maynej/Smart-Home/Imatges/10.png

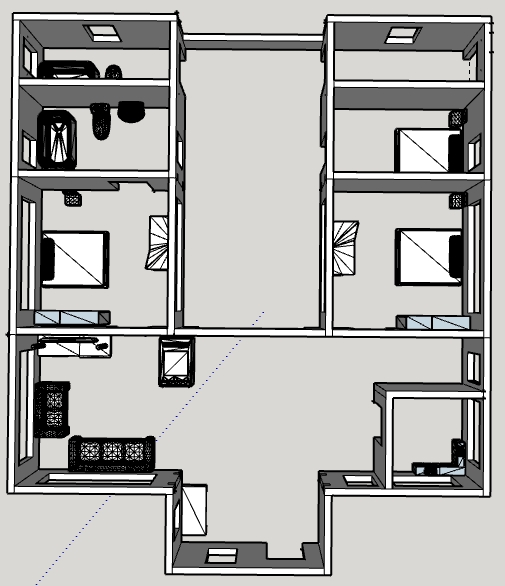
Imatges/10.png
