maynej/Smart-Home/Imatges/14.jpg

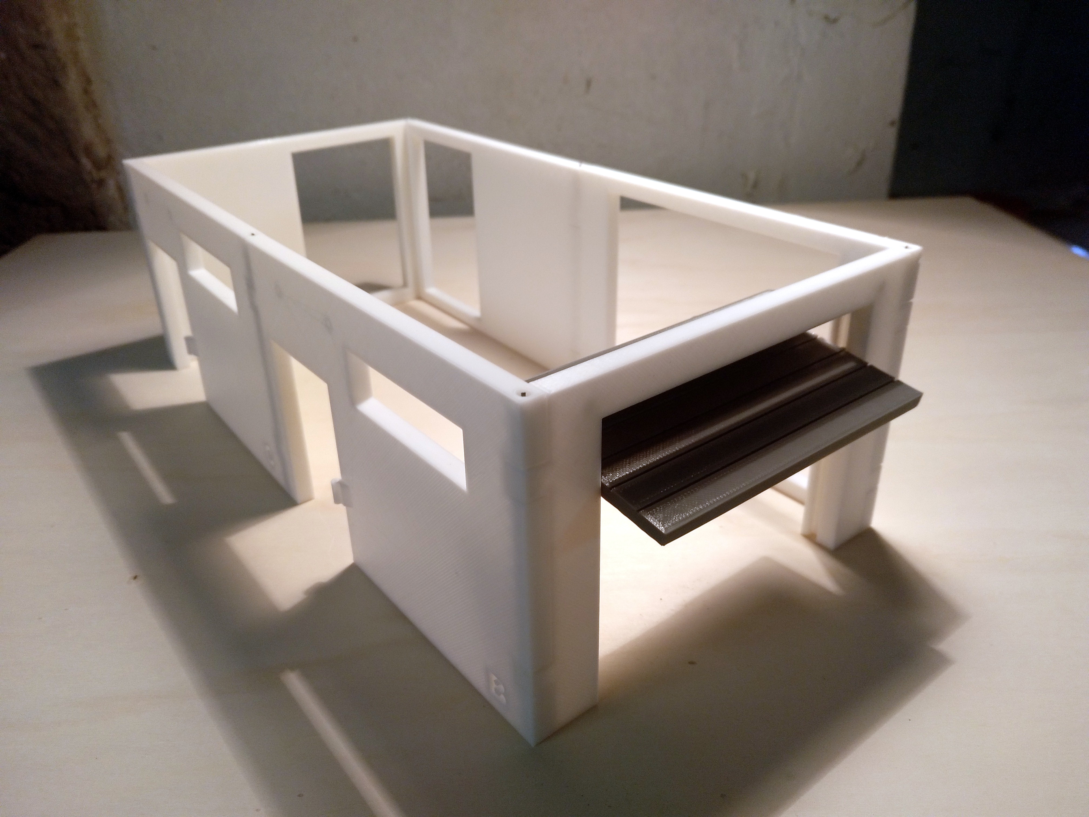
Imatges/14.jpg
