maynej/Smart-Home/Imatges/26.jpg

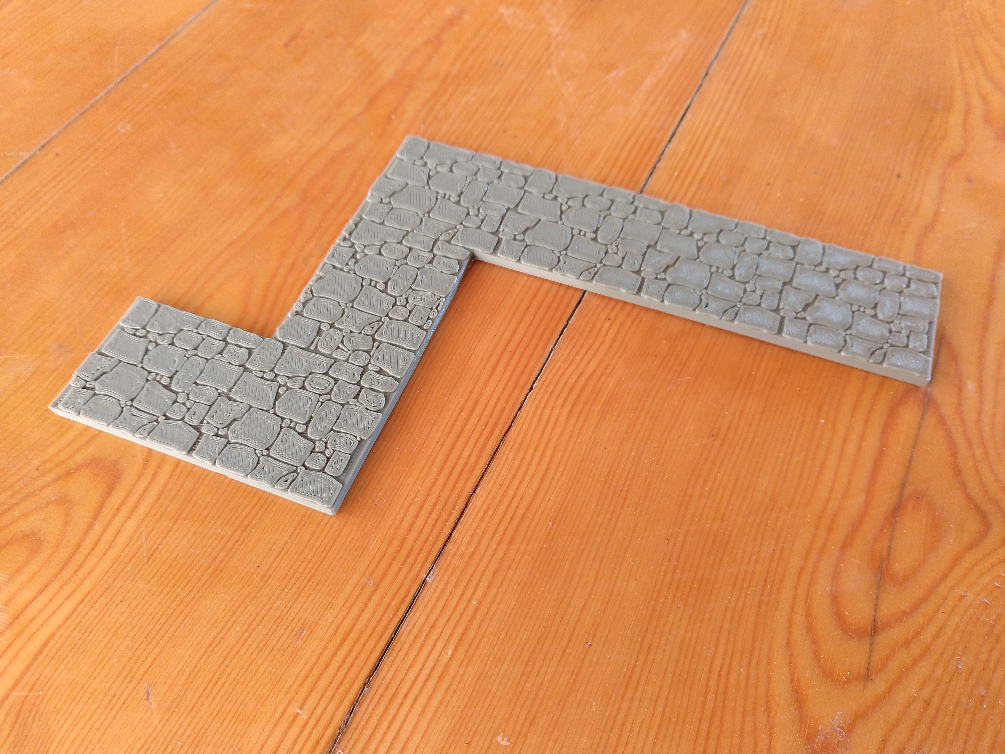
Imatges/26.jpg
