maynej/Smart-Home/Imatges/2020-08-14 22_23_18-Window.png

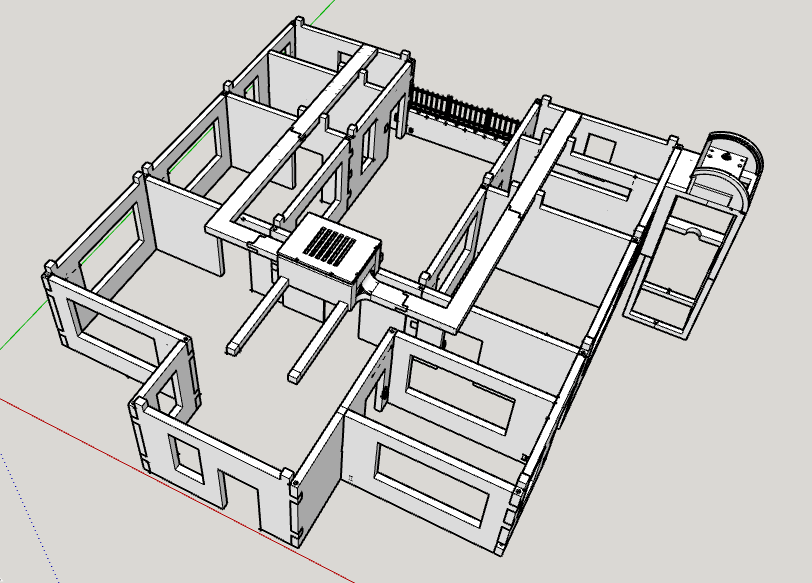
Imatges/2020-08-14 22_23_18-Window.png
