maynej/Smart-Home/Imatges/2020-08-14 22_24_21-Window.png

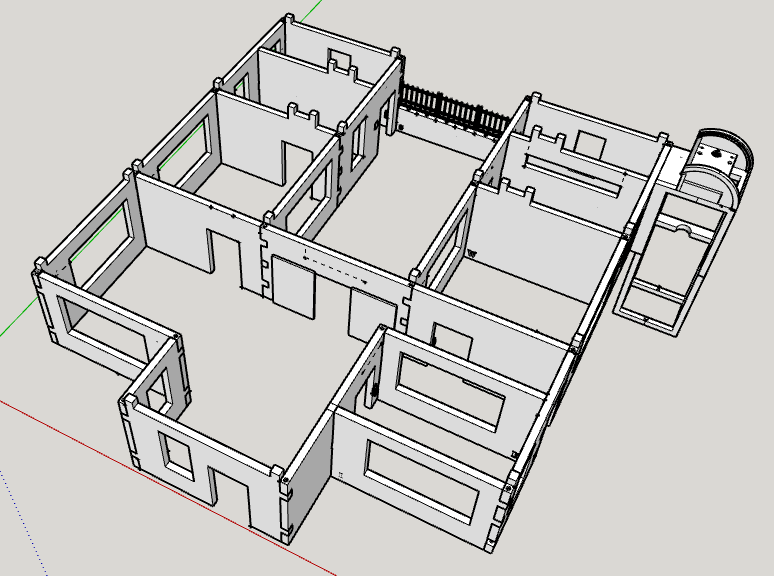
Imatges/2020-08-14 22_24_21-Window.png
