maynej/Smart-Home/Imatges/Casa1.png

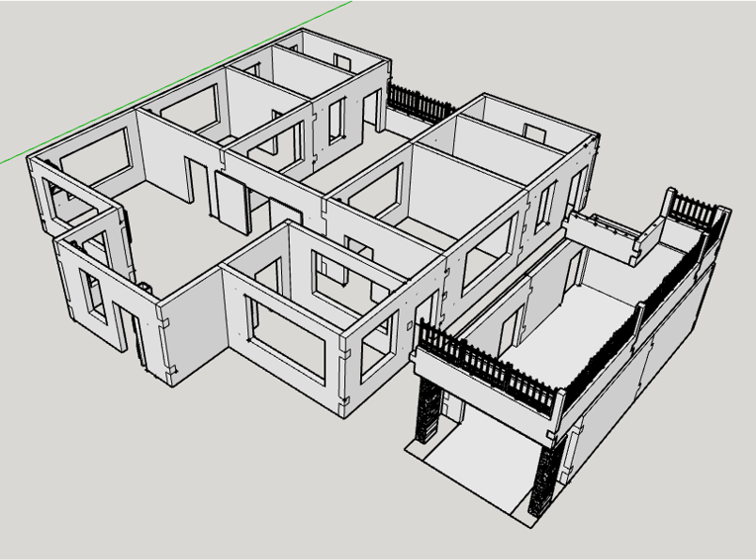
Imatges/Casa1.png
