maynej/Smart-Home/Imatges/IMG_20210501_202601_113.jpg

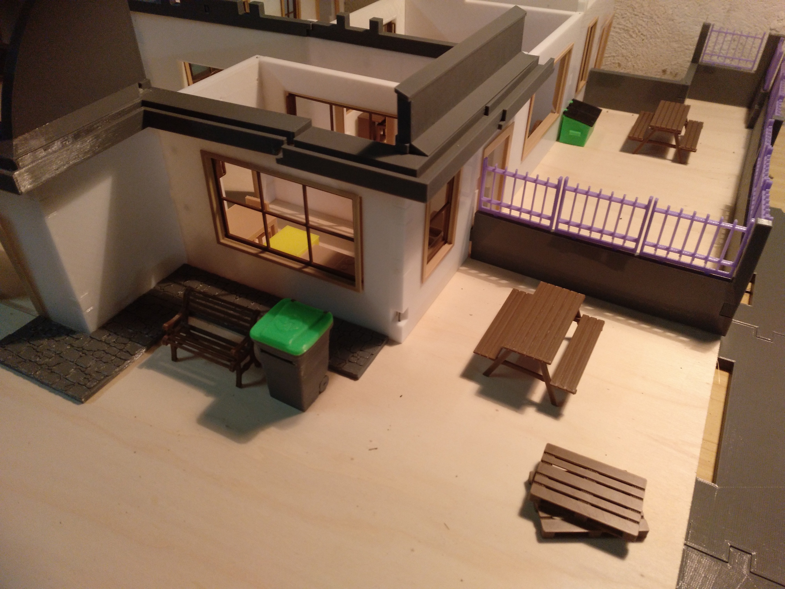
Imatges/IMG_20210501_202601_113.jpg
