maynej/Smart-Home/Imatges/IMG_20210501_202634_148~3.jpg

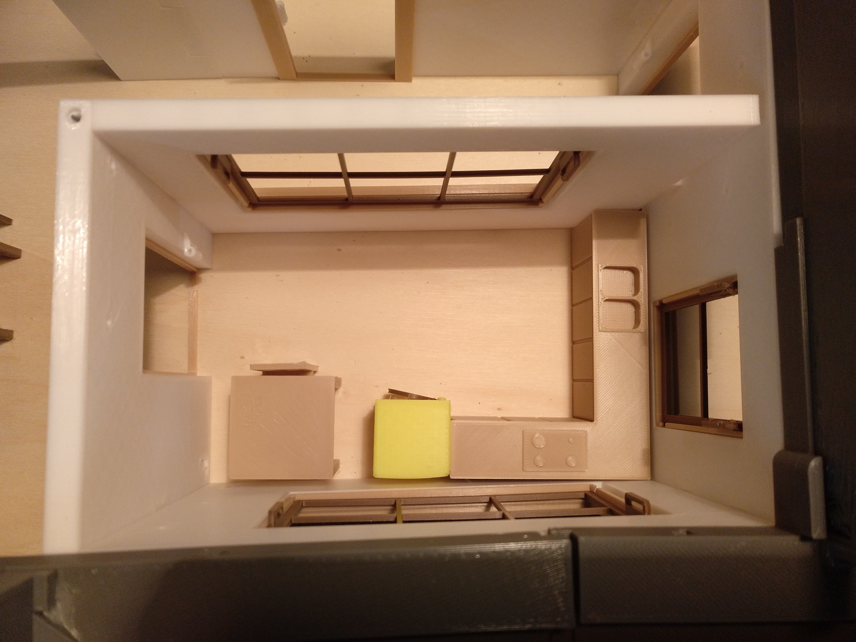
Imatges/IMG_20210501_202634_148~3.jpg
