maynej/Smart-Home/Imatges/IMG_20210501_202759_694~2.jpg

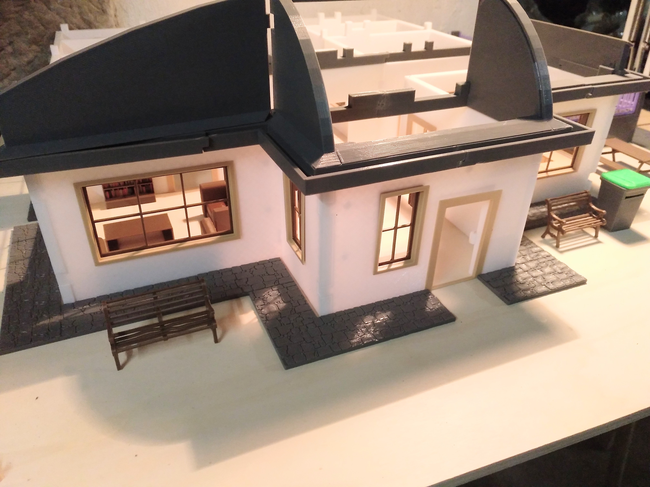
Imatges/IMG_20210501_202759_694~2.jpg
