maynej/Smart-Home/Imatges/IMG_20210501_202805_900~2.jpg

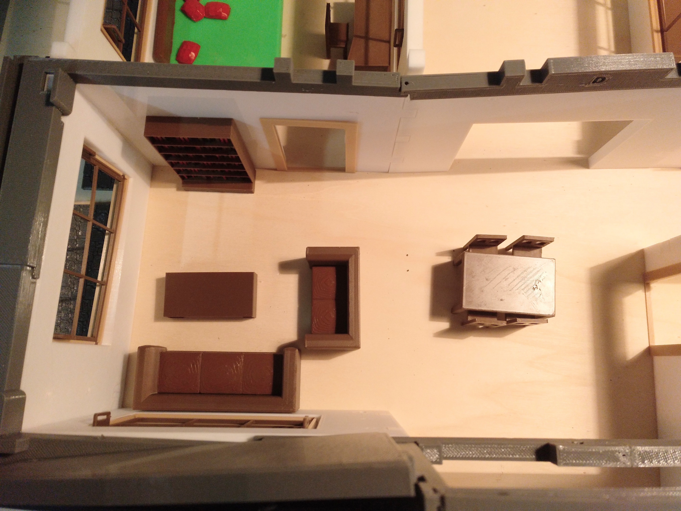
Imatges/IMG_20210501_202805_900~2.jpg
