maynej/Smart-Home/Imatges/IMG_20210501_202834_873.jpg

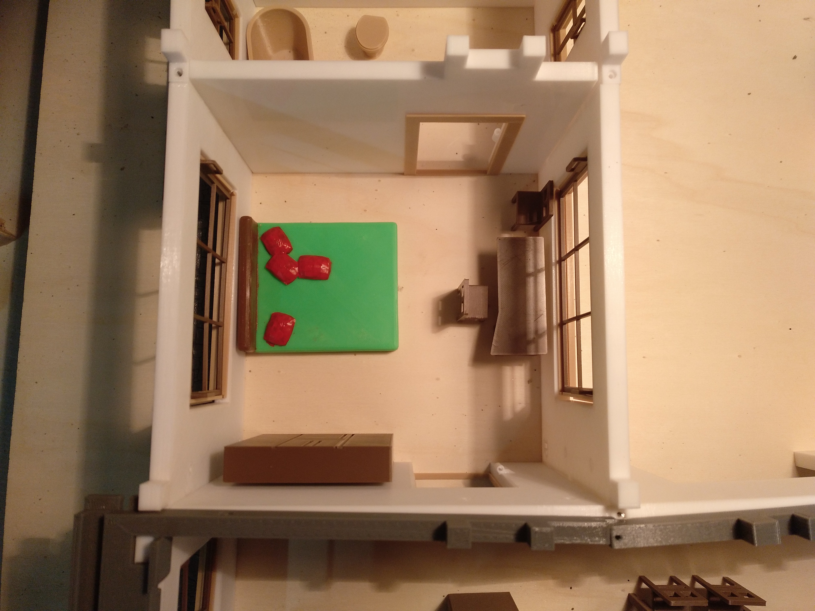
Imatges/IMG_20210501_202834_873.jpg
