maynej/Smart-Home/Imatges/IMG_20210501_202842_626.jpg

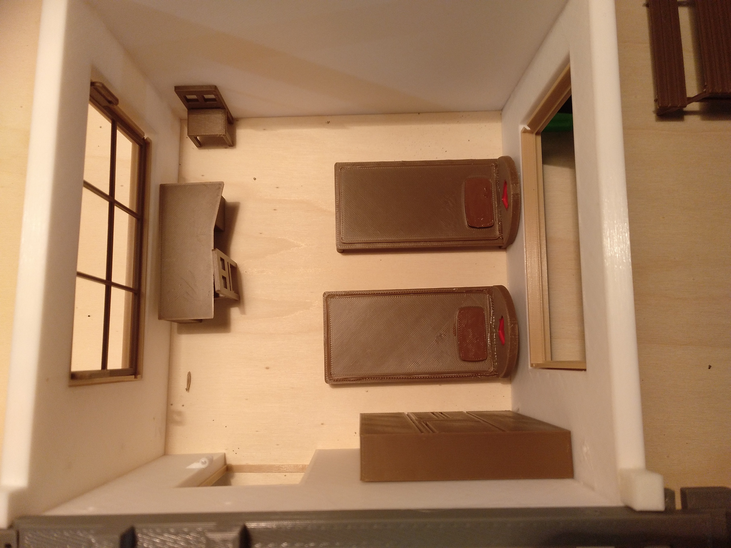
Imatges/IMG_20210501_202842_626.jpg
