maynej/Smart-Home/Imatges/IMG_20210501_202906_033.jpg

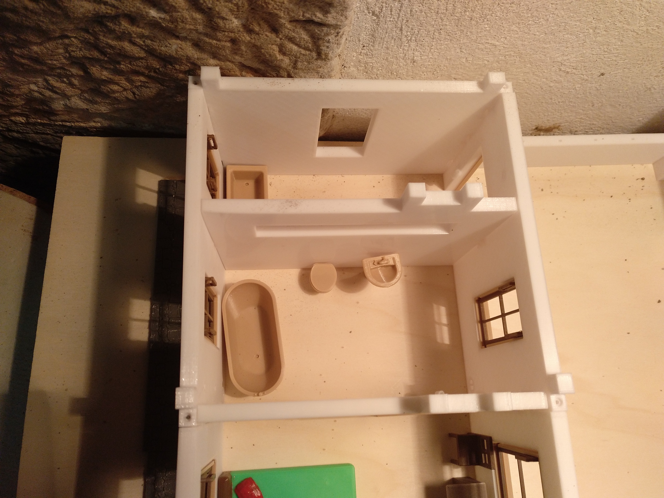
Imatges/IMG_20210501_202906_033.jpg
