maynej/Smart-Home/Imatges/IMG_20210501_202918_298~2.jpg

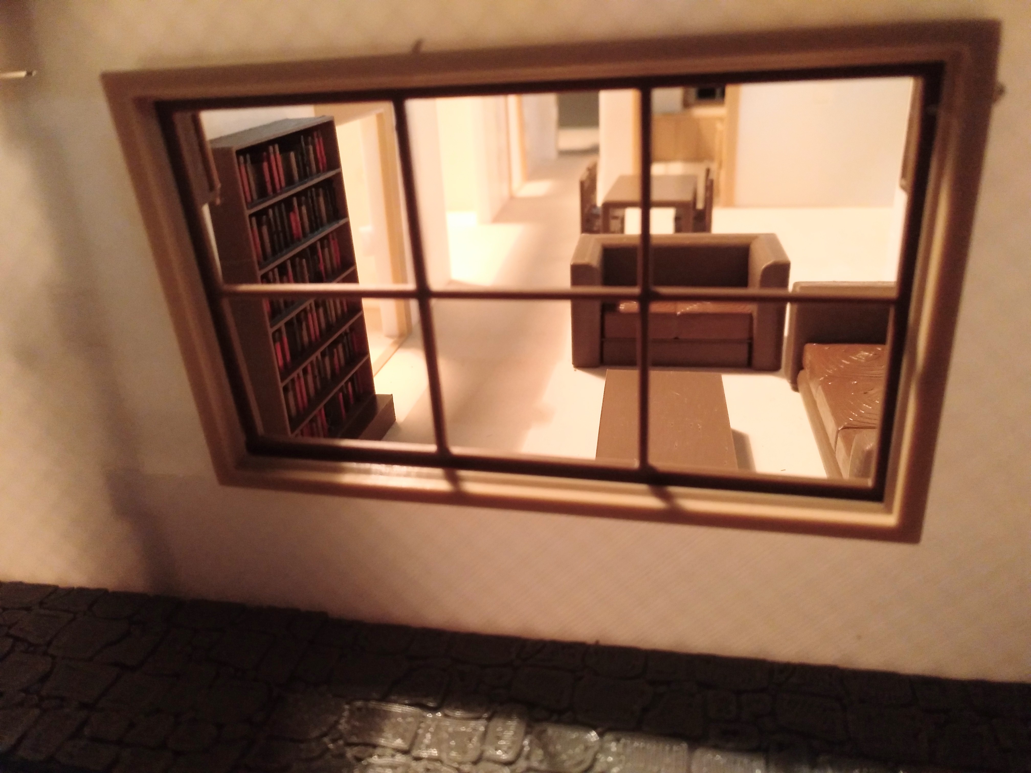
Imatges/IMG_20210501_202918_298~2.jpg
