maynej/Smart-Home/Imatges/IMG_20210501_202927_855.jpg

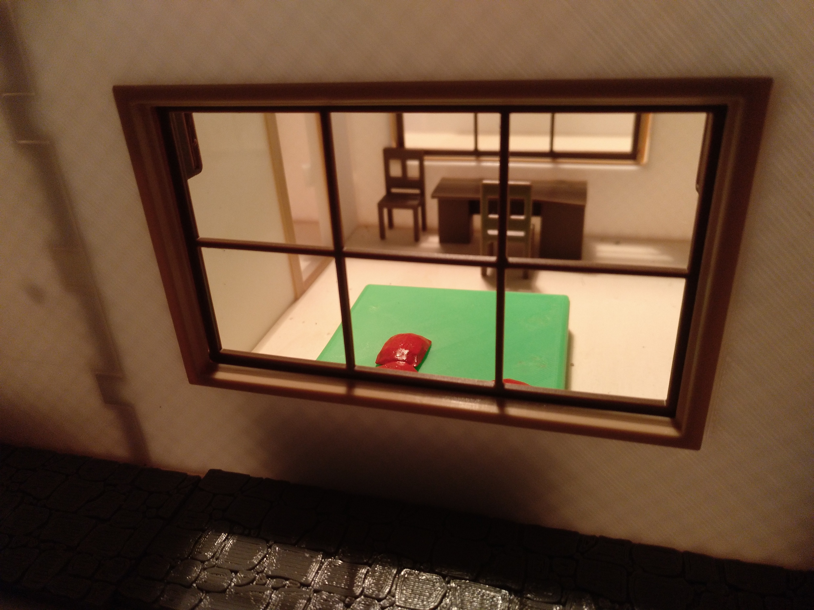
Imatges/IMG_20210501_202927_855.jpg
