maynej/Smart-Home/Imatges/IMG_20210501_202935_807.jpg

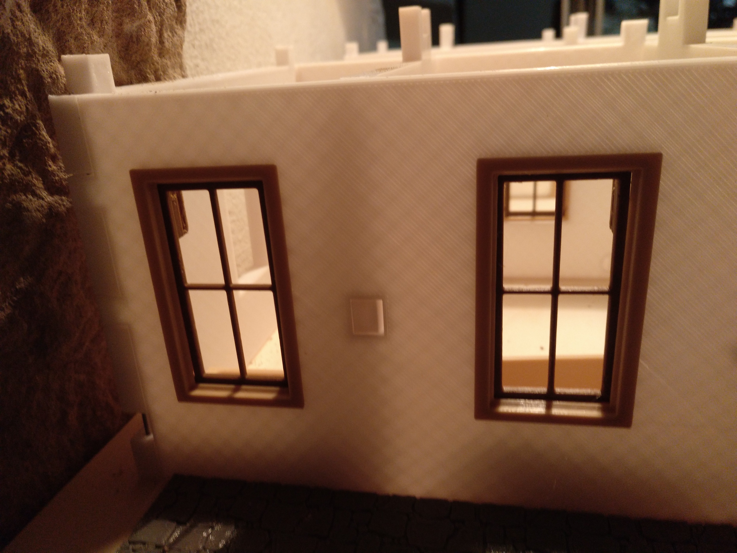
Imatges/IMG_20210501_202935_807.jpg
