maynej/Smart-Home/Imatges/IMG_20210501_202944_740.jpg

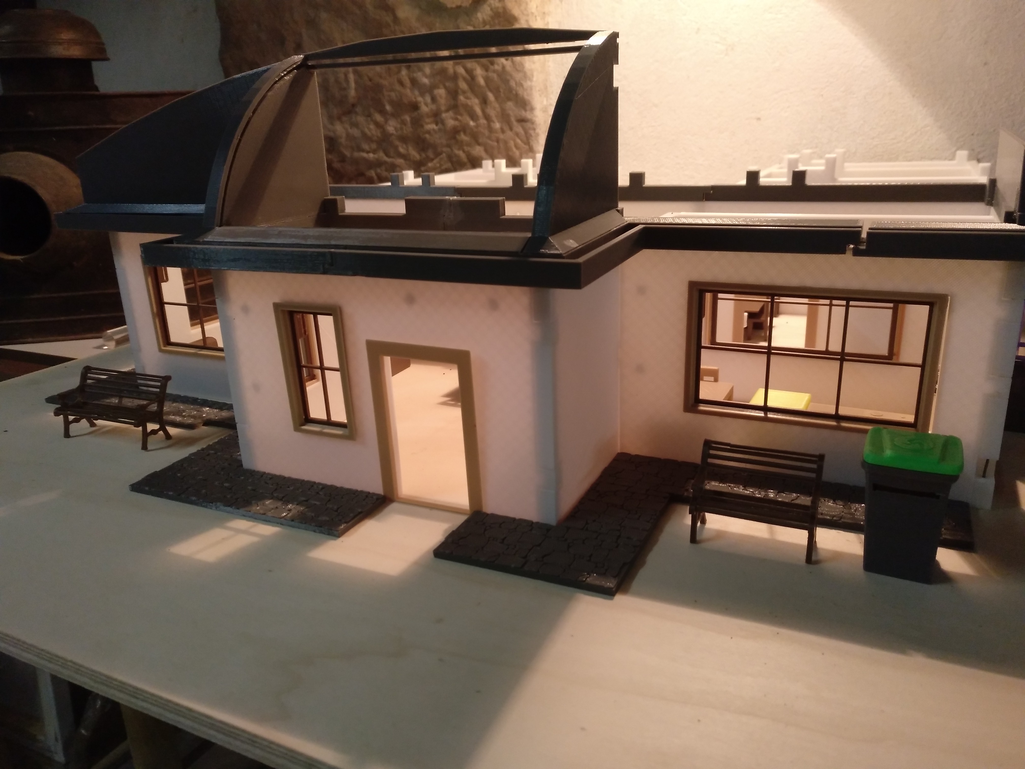
Imatges/IMG_20210501_202944_740.jpg
