maynej/Smart-Home/Imatges/IMG_20210501_202952_292.jpg

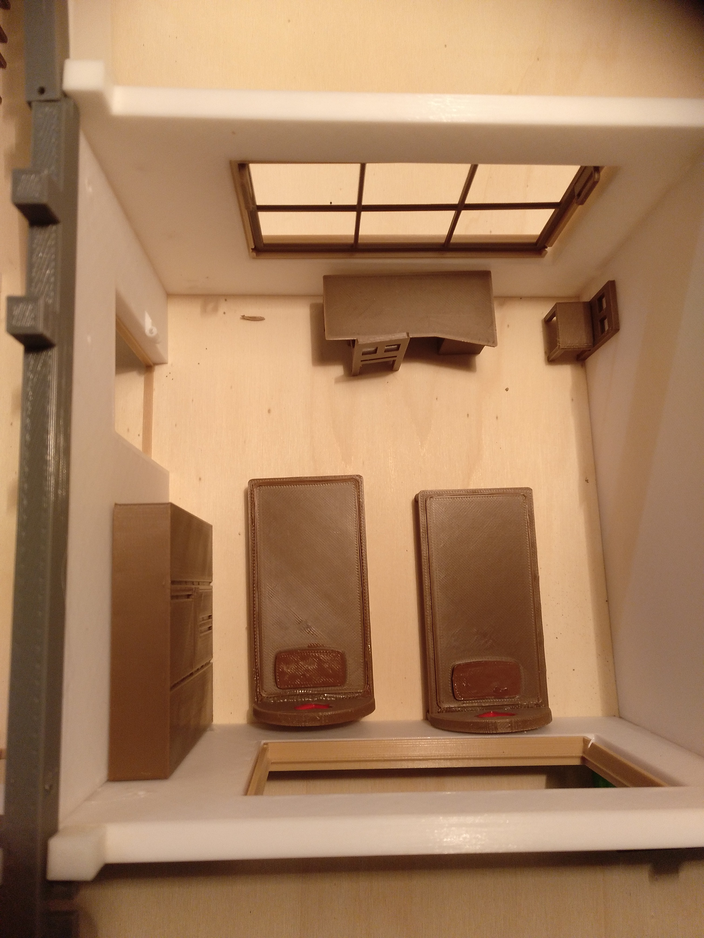
Imatges/IMG_20210501_202952_292.jpg
