maynej/Smart-Home/Imatges/IMG_20210501_203002_859.jpg

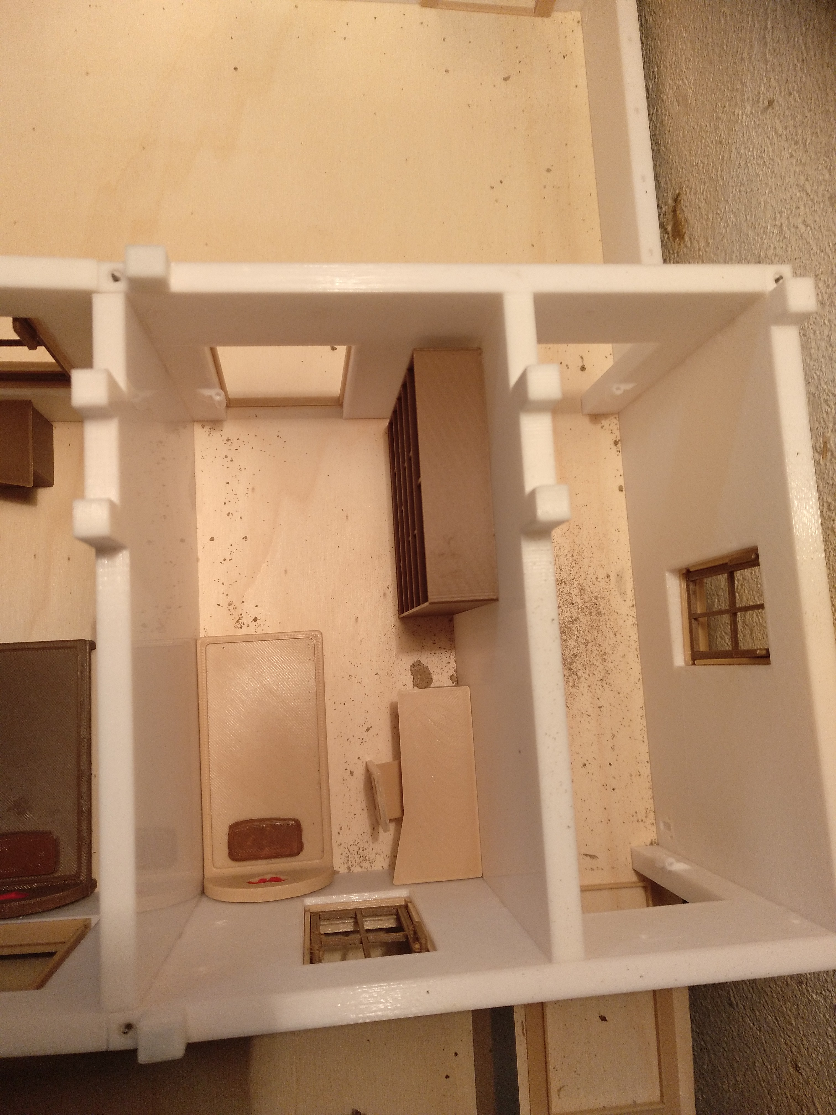
Imatges/IMG_20210501_203002_859.jpg
