maynej/Smart-Home/Imatges/P9200007.jpg

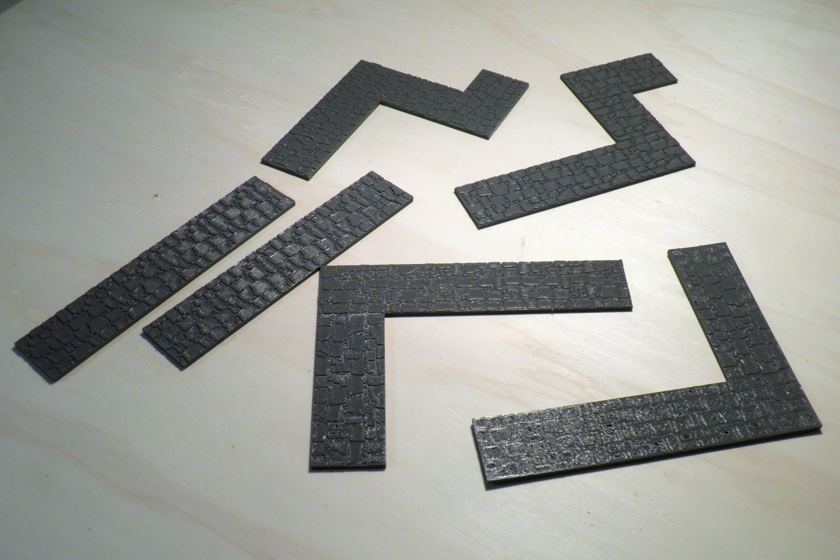
Imatges/P9200007.jpg
