maynej/Smart-Home/Imatges/WhatsApp Image 2020-09-02 at 09.48.22 (1).jpeg

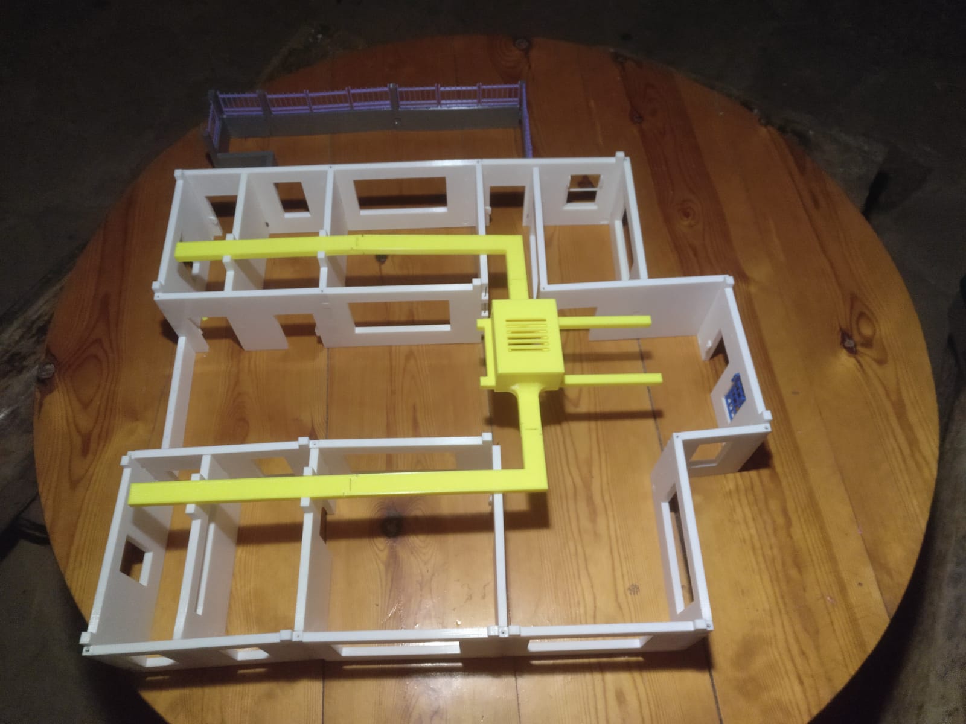
Imatges/WhatsApp Image 2020-09-02 at 09.48.22 (1).jpeg
