maynej/Smart-Home/Imatges/WhatsApp Image 2020-10-18 at 17.20.31.jpeg

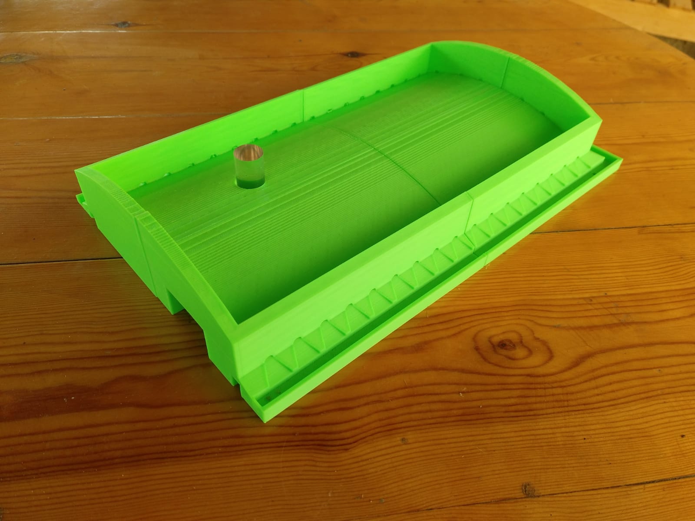
Imatges/WhatsApp Image 2020-10-18 at 17.20.31.jpeg
