maynej/Smart-Home/STL_SMARTHOME/Casa/Teulada/Teulada Frontal/TeuladaFrontal_a_transparent2.stl

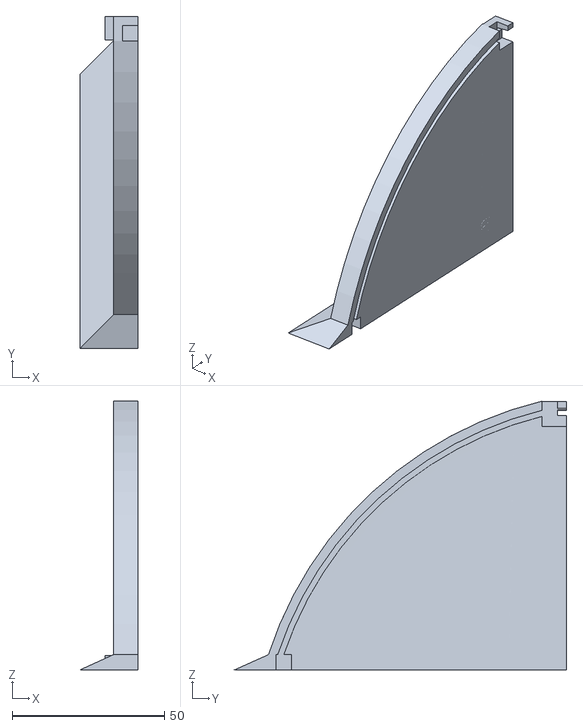
[picture p151: CAD file, 2021-07-27]
STL_SMARTHOME/Casa/Teulada/Teulada Frontal/TeuladaFrontal_a_transparent2.stl
19.0 x 109.0 x 88.2
