maynej/Smart-Home/STL_SMARTHOME/Casa/Teulada/TubDesaiguaCurb.stl

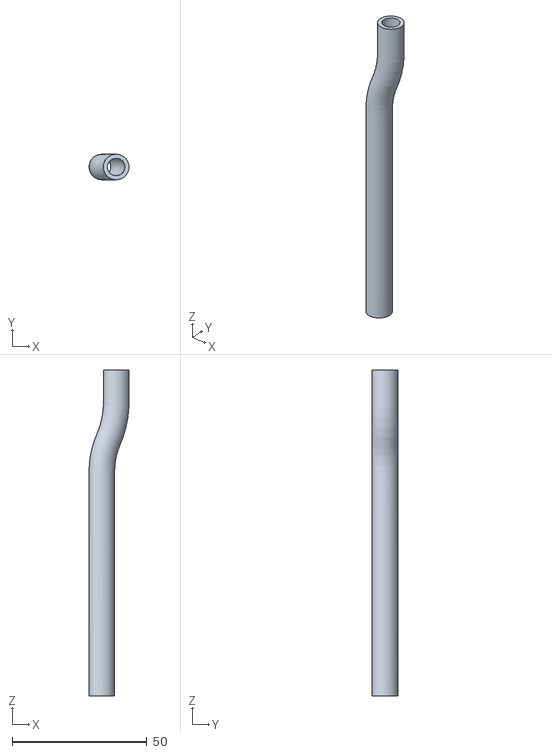
[picture p153: CAD file, 2021-07-27]
STL_SMARTHOME/Casa/Teulada/TubDesaiguaCurb.stl
14.8 x 9.49 x 120.9
