maynej/Smart-Home/STL_SMARTHOME/Casa/Vorera/VoreraEsquerraPedres3.stl

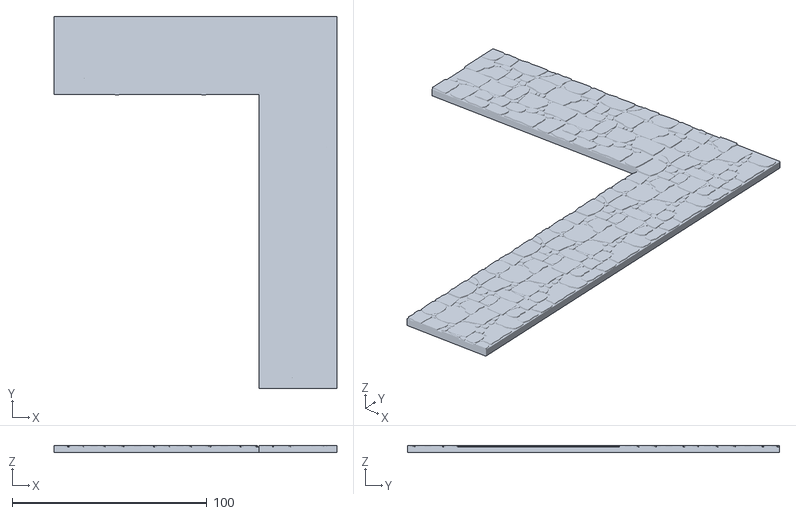
[picture p154: CAD file, 2021-07-27]
STL_SMARTHOME/Casa/Vorera/VoreraEsquerraPedres3.stl
145.3 x 191.0 x 3.71
