maynej/Smart-Home/STL_SMARTHOME/Garatge/PalancaPortaGaratge.stl

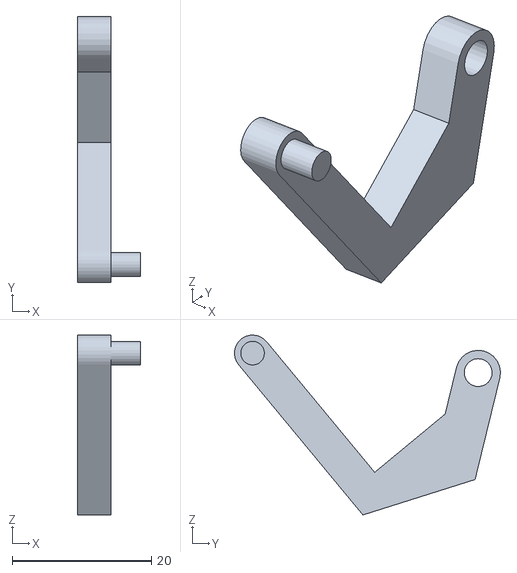
[picture p155: CAD file, 2021-07-27]
STL_SMARTHOME/Garatge/PalancaPortaGaratge.stl
9.00 x 38.1 x 25.8
