maynej/Smart-Home/STL_SMARTHOME/Jardi/GeneradorEolic/Motor.stl

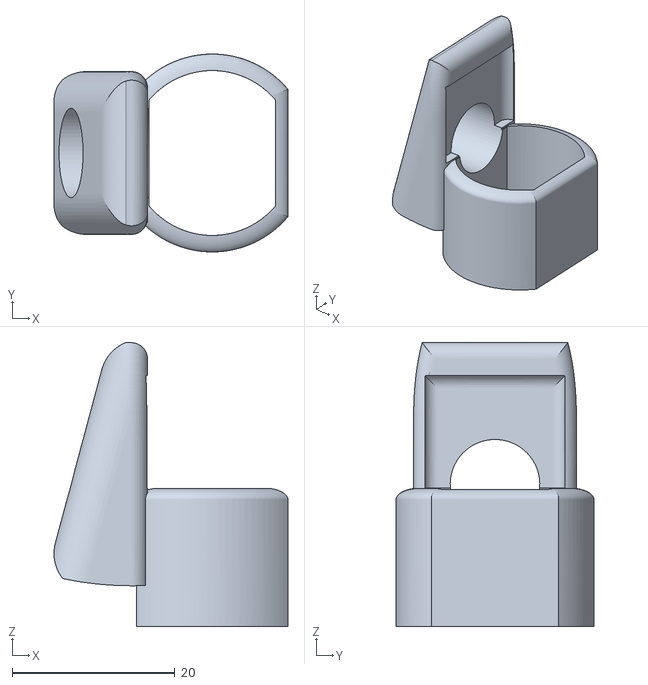
[picture p156: CAD file, 2021-07-27]
STL_SMARTHOME/Jardi/GeneradorEolic/Motor.stl
28.7 x 24.3 x 34.9
