maynej/Smart-Home/STL_SMARTHOME/Jardi/Piscina2.stl

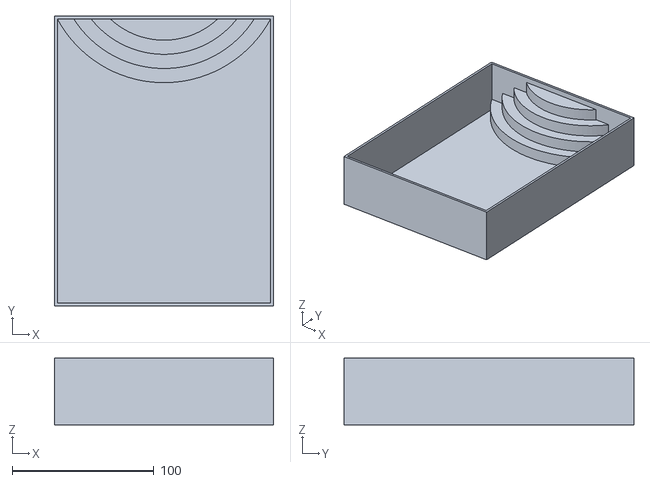
[picture p157: CAD file, 2021-07-27]
STL_SMARTHOME/Jardi/Piscina2.stl
154.5 x 204.5 x 47.0
