maynej/Smart-Home/STL_SMARTHOME/Jardi/SeguidorSolar/SuportCellulaSolar180x80.stl

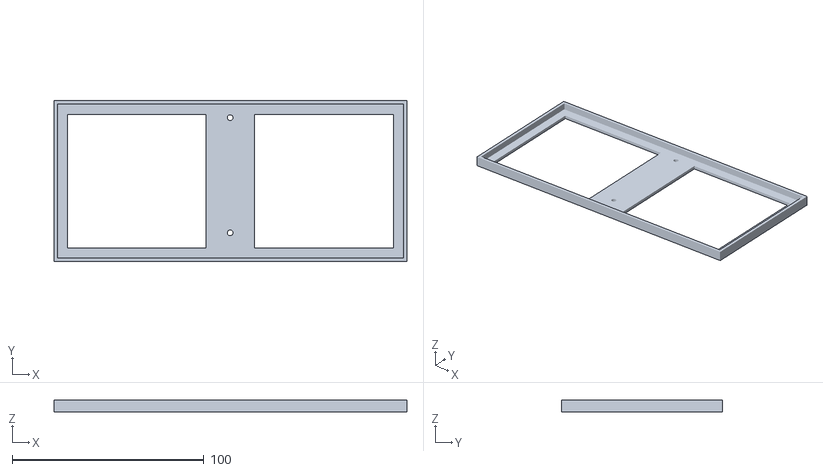
[picture p158: CAD file, 2021-07-27]
STL_SMARTHOME/Jardi/SeguidorSolar/SuportCellulaSolar180x80.stl
184.0 x 84.0 x 6.00
