maynej/Smart-Home/STL_SMARTHOME/Jardi/SolarWeather/front-cover.stl

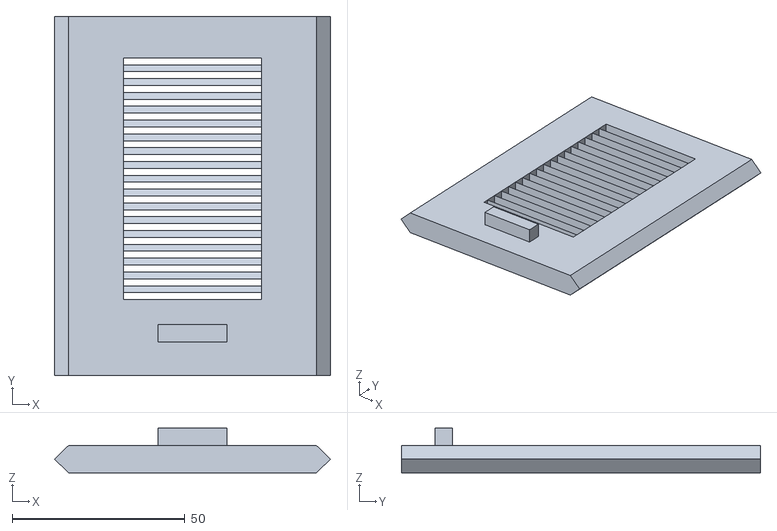
[picture p159: CAD file, 2021-07-27]
STL_SMARTHOME/Jardi/SolarWeather/front-cover.stl
80.0 x 104.0 x 13.0
