maynej/Smart-Home/STL_SMARTHOME/Jardi/TurbinaAigua/Cover.STL

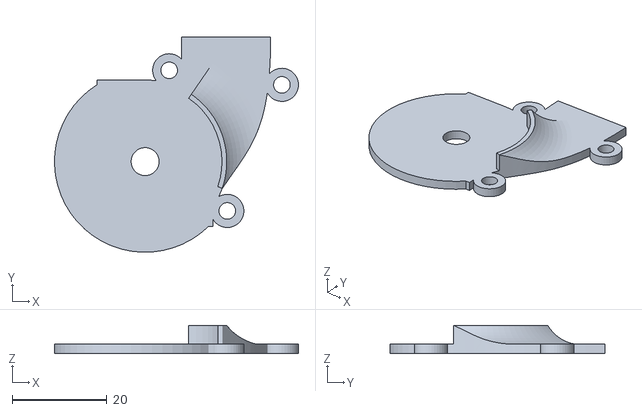
[picture p160: CAD file, 2021-07-27]
STL_SMARTHOME/Jardi/TurbinaAigua/Cover.STL
51.4 x 45.4 x 6.00
