maynej/Smart-Home/STL_SMARTHOME/Casa/AireCondicionat/AireCondicionatC.stl

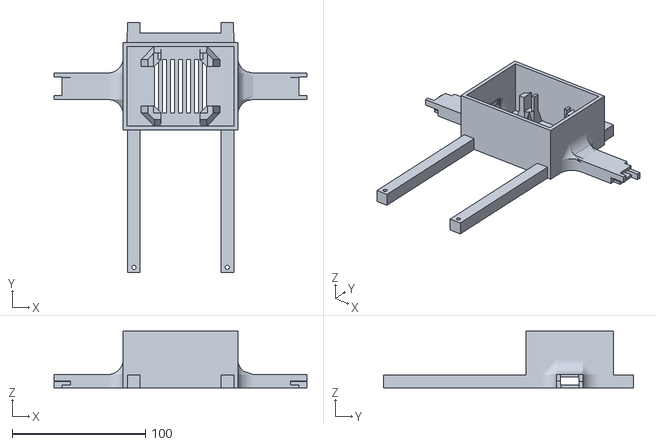
[picture p161: CAD file, 2021-07-27]
STL_SMARTHOME/Casa/AireCondicionat/AireCondicionatC.stl
190.0 x 188.0 x 42.5
