maynej/Smart-Home/STL_SMARTHOME/Casa/Ascensor/CabinaAscensorTapa.stl

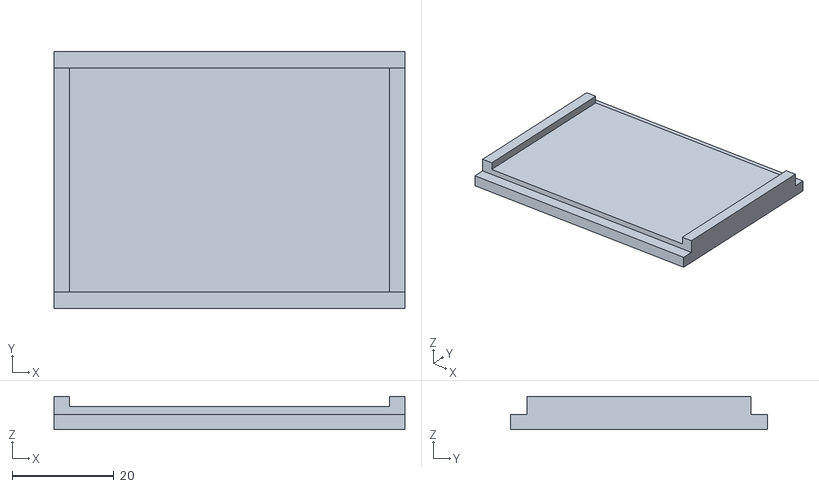
[picture p162: CAD file, 2021-07-27]
STL_SMARTHOME/Casa/Ascensor/CabinaAscensorTapa.stl
69.0 x 50.5 x 6.50
