maynej/Smart-Home/STL_SMARTHOME/Casa/Finestres/VidrieraGran.stl

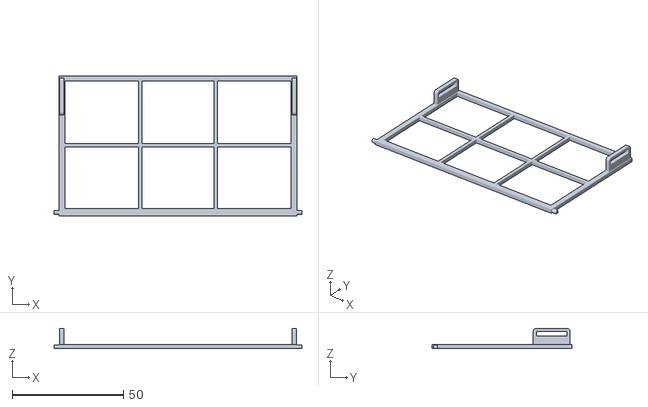
[picture p163: CAD file, 2021-07-27]
STL_SMARTHOME/Casa/Finestres/VidrieraGran.stl
111.4 x 62.8 x 9.18
