maynej/Smart-Home/STL_SMARTHOME/Casa/Mobiliari/Bany/WC.stl

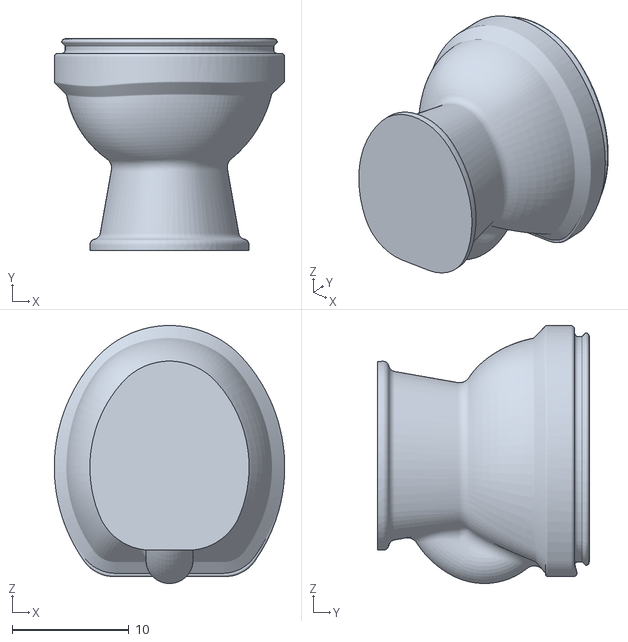
[picture p164: CAD file, 2021-07-27]
STL_SMARTHOME/Casa/Mobiliari/Bany/WC.stl
19.7 x 18.1 x 22.1
