maynej/Smart-Home/STL_SMARTHOME/Casa/Mobiliari/Cuina/TaulaCuina.stl

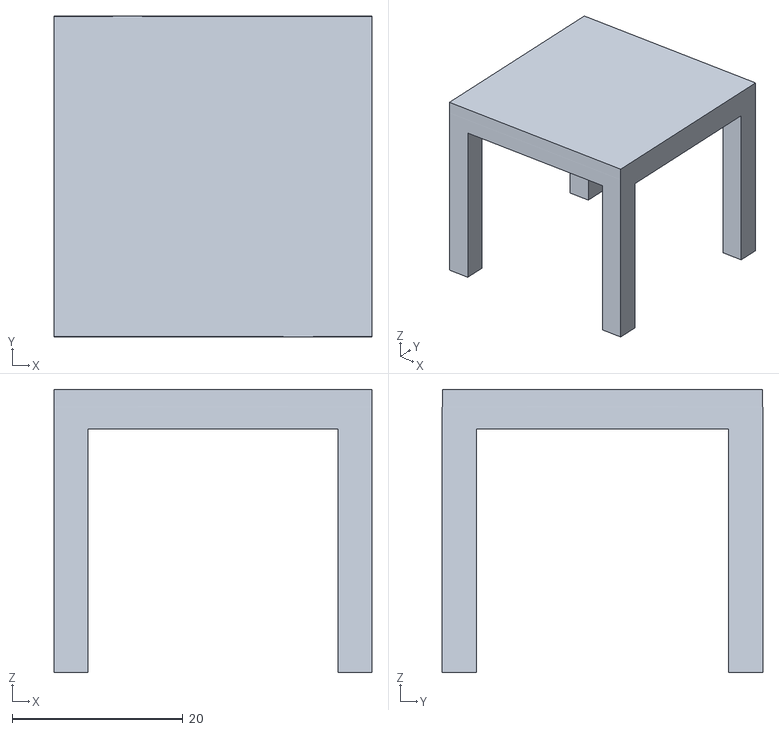
[picture p165: CAD file, 2021-07-27]
STL_SMARTHOME/Casa/Mobiliari/Cuina/TaulaCuina.stl
37.2 x 37.5 x 33.1
