maynej/Smart-Home/STL_SMARTHOME/Casa/Mobiliari/Dormitoris/Llit180x200.stl

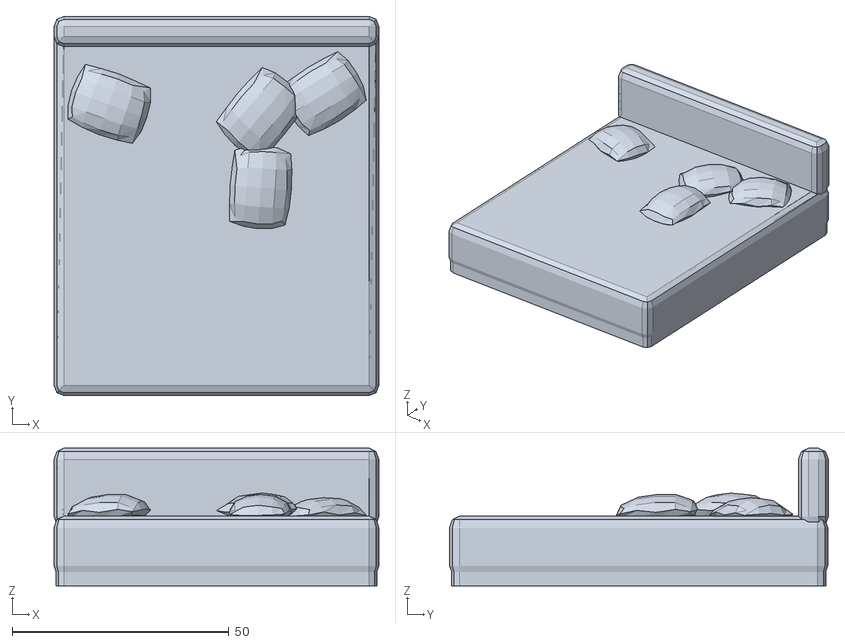
[picture p166: CAD file, 2021-07-27]
STL_SMARTHOME/Casa/Mobiliari/Dormitoris/Llit180x200.stl
75.0 x 87.5 x 31.8
