maynej/Smart-Home/STL_SMARTHOME/Casa/Mobiliari/Exterior/BancJardi.stl

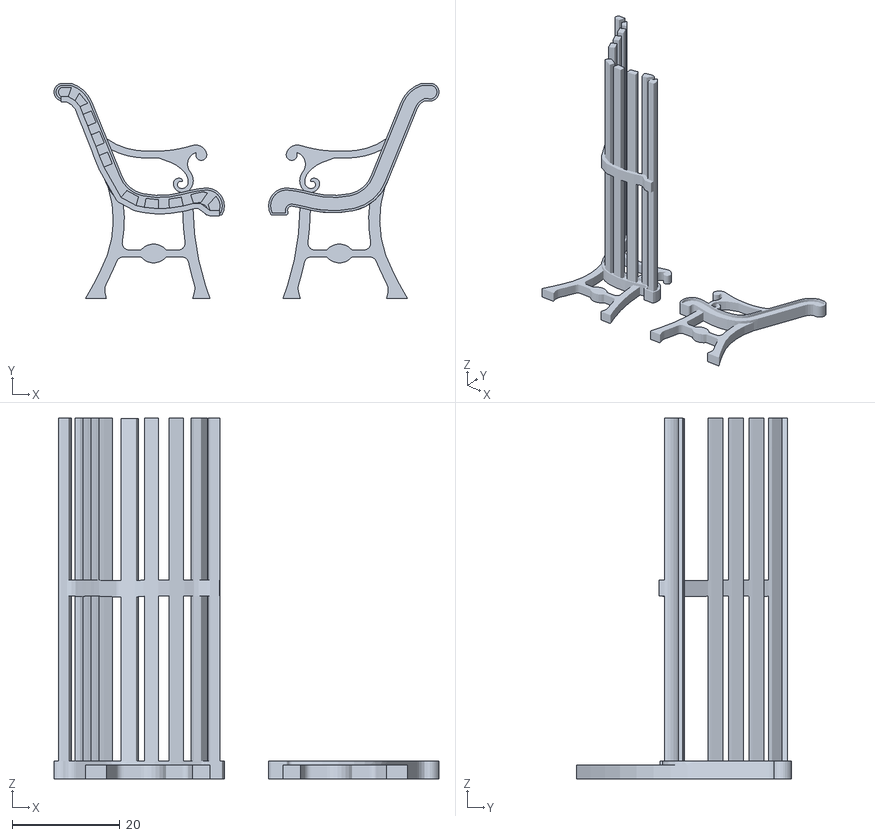
[picture p167: CAD file, 2021-07-27]
STL_SMARTHOME/Casa/Mobiliari/Exterior/BancJardi.stl
71.3 x 39.9 x 66.8
