maynej/Smart-Home/STL_SMARTHOME/Casa/Mobiliari/Salo/Taula.stl

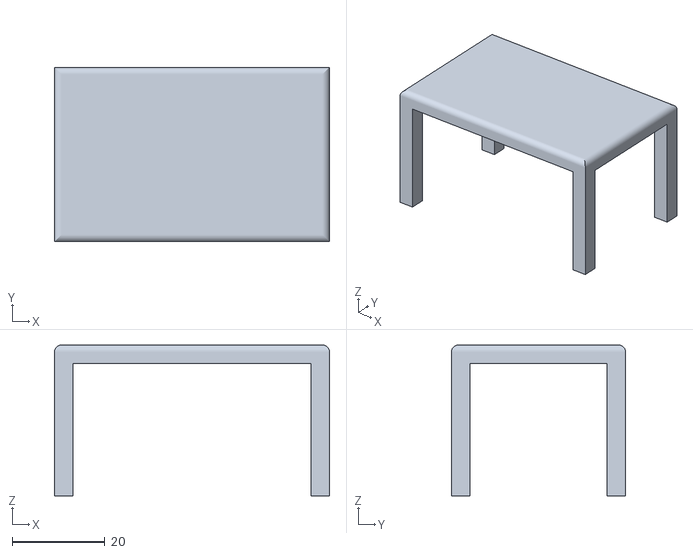
[picture p168: CAD file, 2021-07-27]
STL_SMARTHOME/Casa/Mobiliari/Salo/Taula.stl
59.2 x 37.5 x 32.5
