maynej/Smart-Home/STL_SMARTHOME/Casa/PatiGaratge/MurA.stl

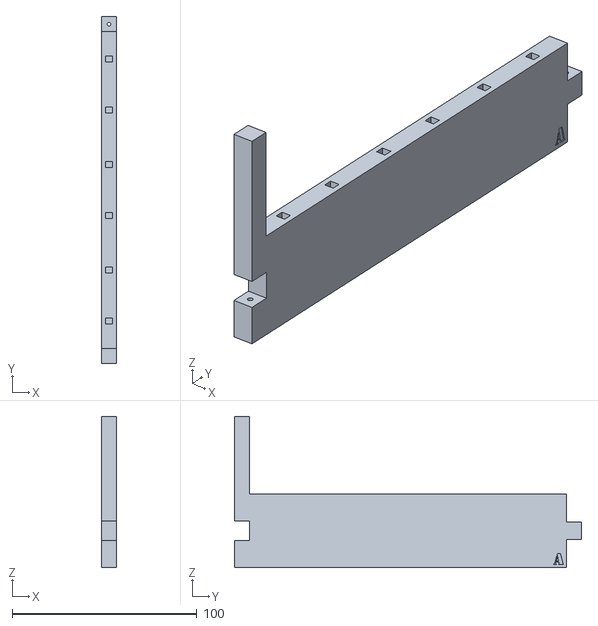
[picture p169: CAD file, 2021-07-27]
STL_SMARTHOME/Casa/PatiGaratge/MurA.stl
8.00 x 188.0 x 82.0
