maynej/Smart-Home/STL_SMARTHOME/Casa/Portes/Porta_Dreta.stl

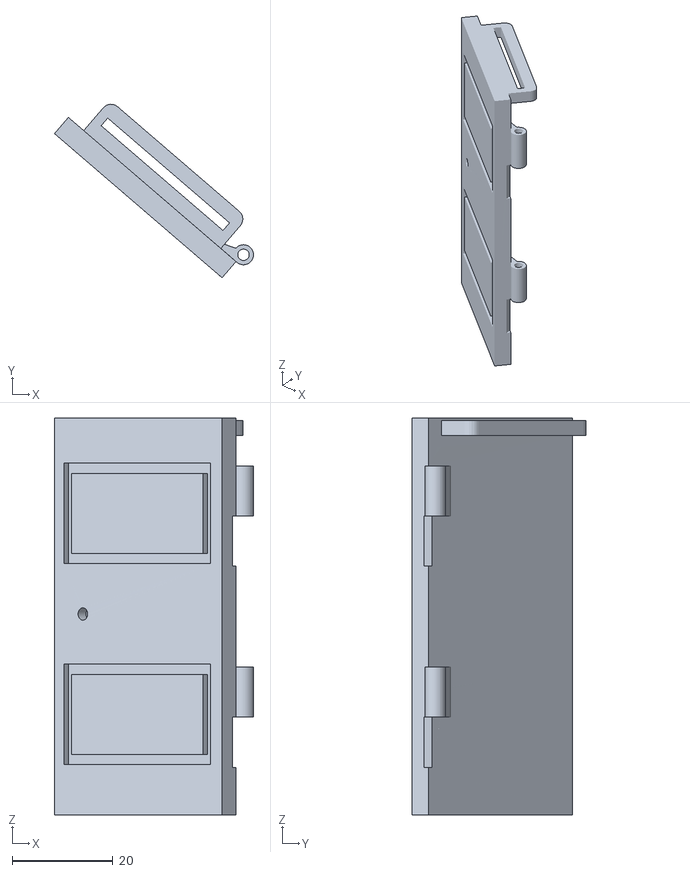
[picture p170: CAD file, 2021-07-27]
STL_SMARTHOME/Casa/Portes/Porta_Dreta.stl
39.6 x 34.5 x 79.0
