maynej/Smart-Home/STL_SMARTHOME/Casa/Teulada/Suport_Teulada Frontal/SuportTeuladaA.stl

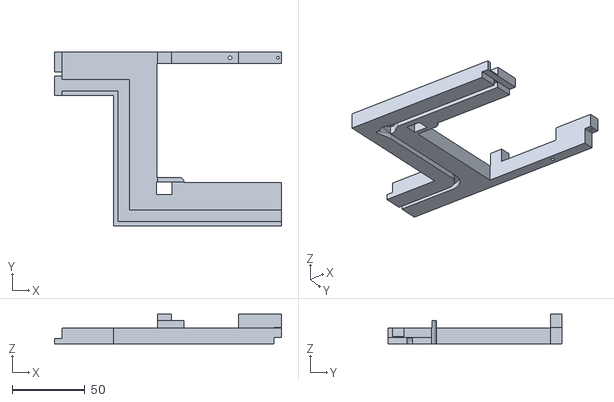
[picture p171: CAD file, 2021-07-27]
STL_SMARTHOME/Casa/Teulada/Suport_Teulada Frontal/SuportTeuladaA.stl
156.4 x 120.0 x 20.5
