maynej/Smart-Home/STL_SMARTHOME/Casa/Teulada/Teulada Frontal/TeuladaFrontal_a_transparent3.stl

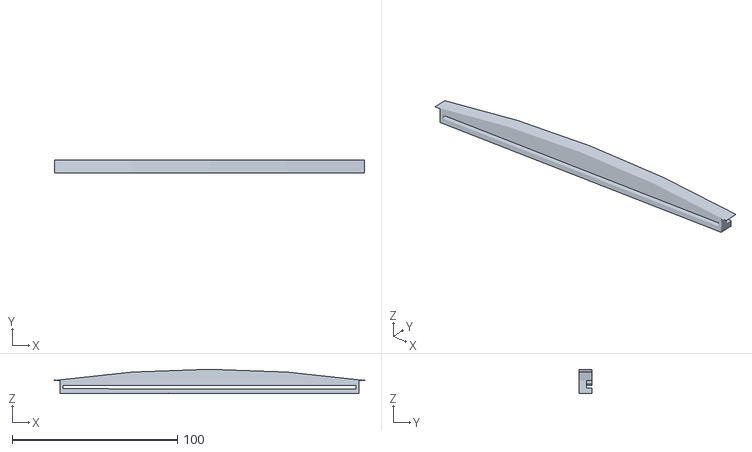
[picture p172: CAD file, 2021-07-27]
STL_SMARTHOME/Casa/Teulada/Teulada Frontal/TeuladaFrontal_a_transparent3.stl
187.5 x 8.02 x 14.8
