maynej/Smart-Home/STL_SMARTHOME/Casa/Vorera/VoreraDretaPedres1.stl

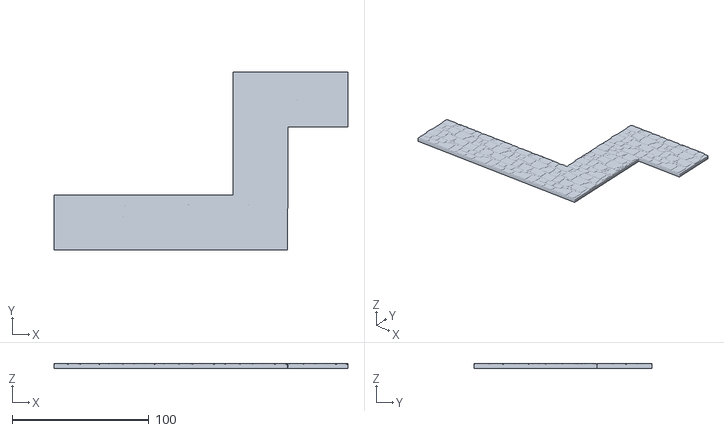
[picture p173: CAD file, 2021-07-27]
STL_SMARTHOME/Casa/Vorera/VoreraDretaPedres1.stl
214.8 x 129.7 x 3.81
