maynej/Smart-Home/STL_SMARTHOME/Garatge/GaratgeA.stl

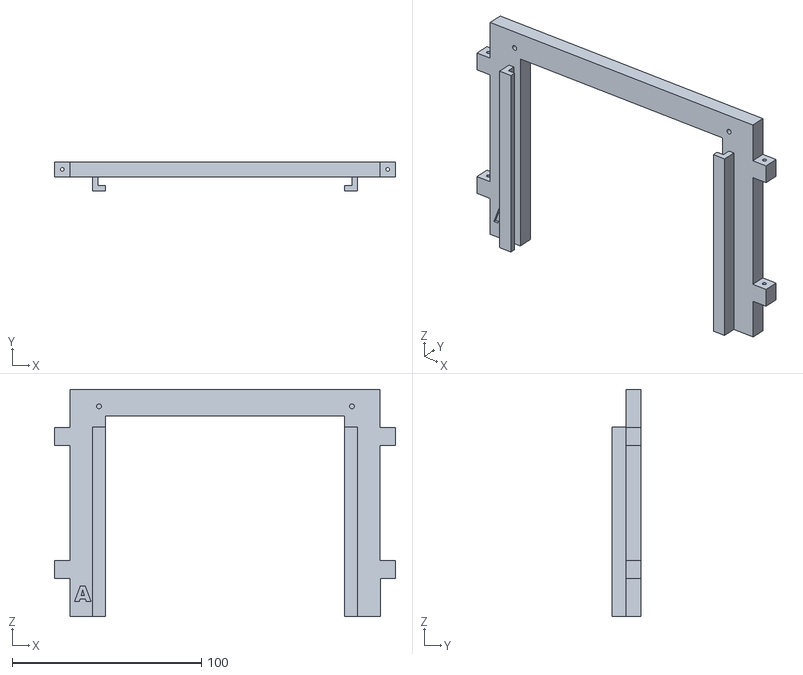
[picture p174: CAD file, 2021-07-27]
STL_SMARTHOME/Garatge/GaratgeA.stl
180.0 x 15.5 x 120.0
