maynej/Smart-Home/STL_SMARTHOME/Jardi/GeneradorEolic/PalesTurbina.stl

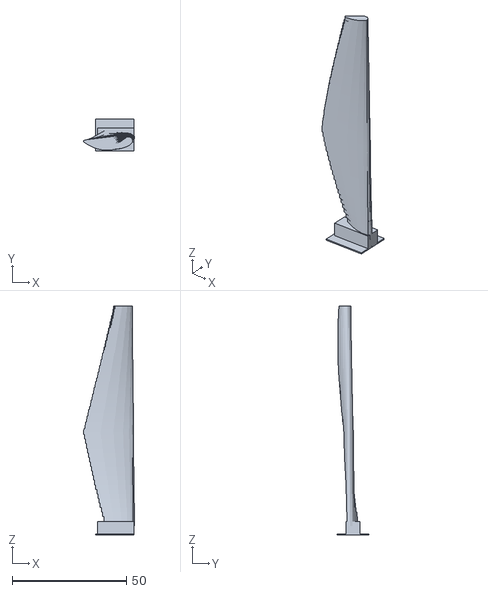
[picture p175: CAD file, 2021-07-27]
STL_SMARTHOME/Jardi/GeneradorEolic/PalesTurbina.stl
22.5 x 14.0 x 100.4
