maynej/Smart-Home/STL_SMARTHOME/Jardi/Hort.stl

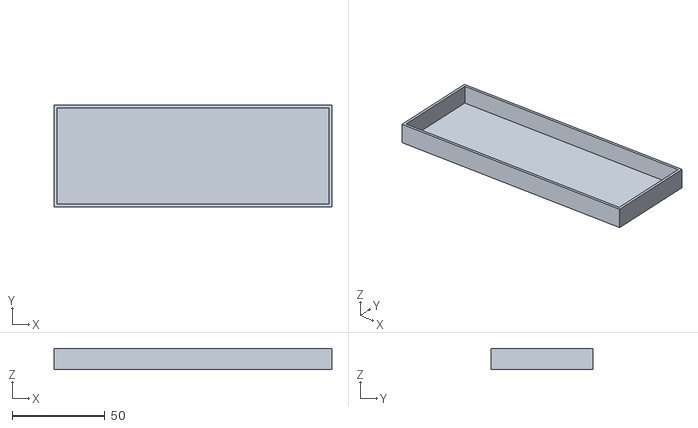
[picture p176: CAD file, 2021-07-27]
STL_SMARTHOME/Jardi/Hort.stl
150.0 x 55.0 x 11.5
