maynej/Smart-Home/STL_SMARTHOME/Jardi/SeguidorSolar/SuportCellulaSolar150x130.stl

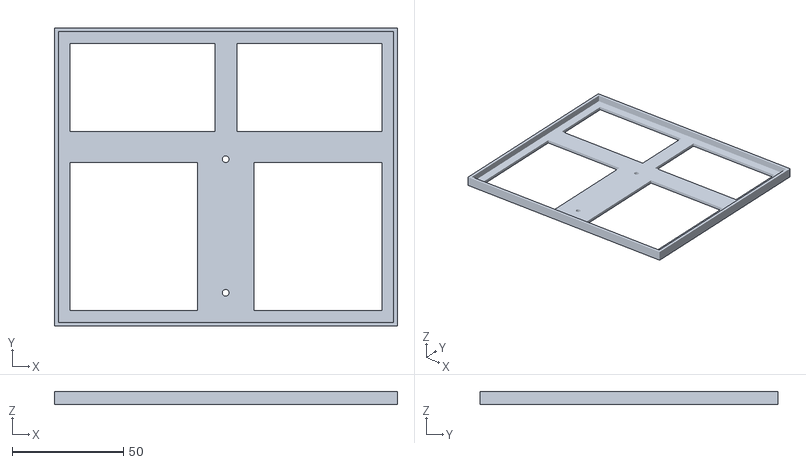
[picture p177: CAD file, 2021-07-27]
STL_SMARTHOME/Jardi/SeguidorSolar/SuportCellulaSolar150x130.stl
154.0 x 134.0 x 6.00
