maynej/Smart-Home/STL_SMARTHOME/Jardi/TurbinaAigua/Housing.STL

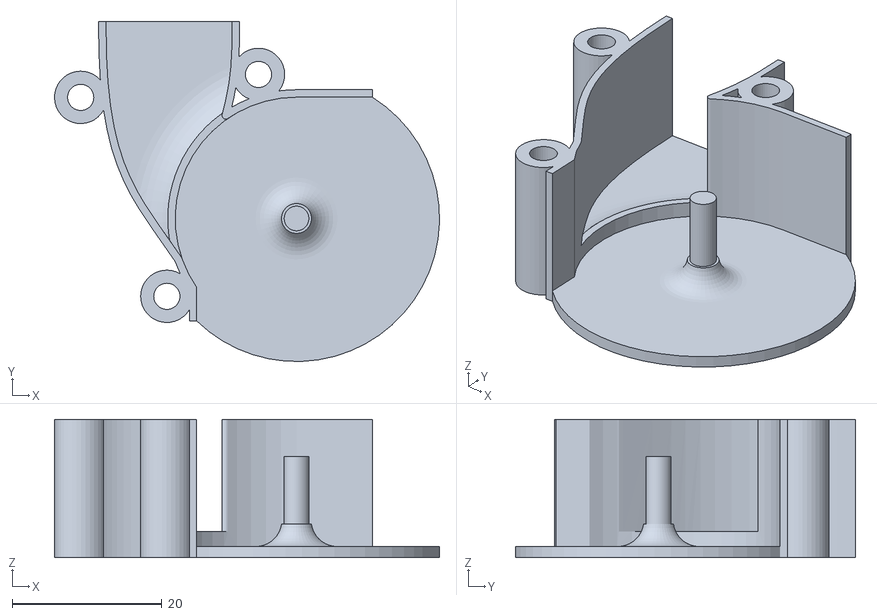
[picture p178: CAD file, 2021-07-27]
STL_SMARTHOME/Jardi/TurbinaAigua/Housing.STL
51.4 x 45.4 x 18.5
