maynej/Smart-Home/STL_SMARTHOME/Casa/AireCondicionat/TubAireE.stl

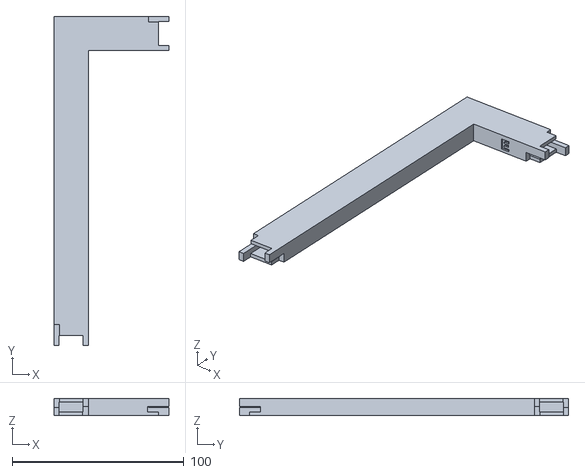
[picture p179: CAD file, 2021-07-27]
STL_SMARTHOME/Casa/AireCondicionat/TubAireE.stl
67.1 x 192.0 x 10.0
