maynej/Smart-Home/STL_SMARTHOME/Casa/Ascensor/Ascensor2.stl

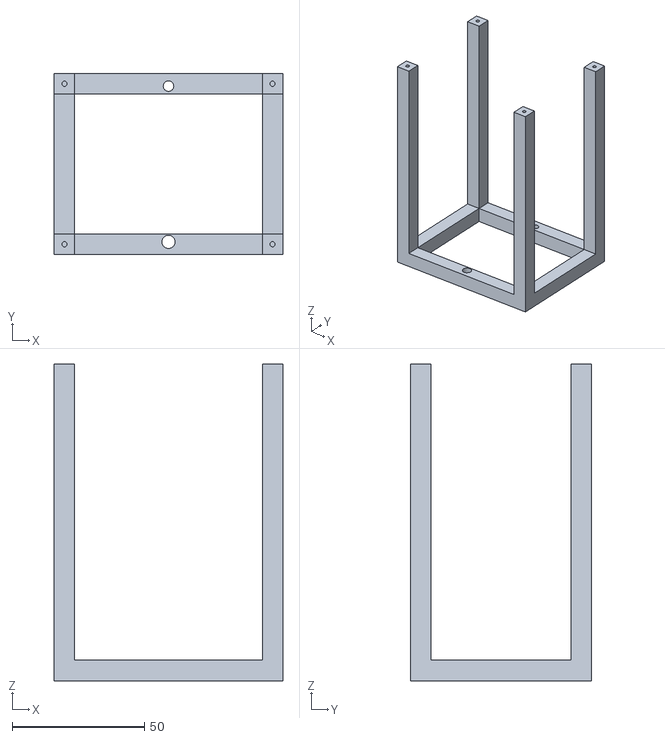
[picture p180: CAD file, 2021-07-27]
STL_SMARTHOME/Casa/Ascensor/Ascensor2.stl
86.5 x 68.5 x 120.0
