maynej/Smart-Home/STL_SMARTHOME/Casa/Finestres/VidrieraPetita.stl

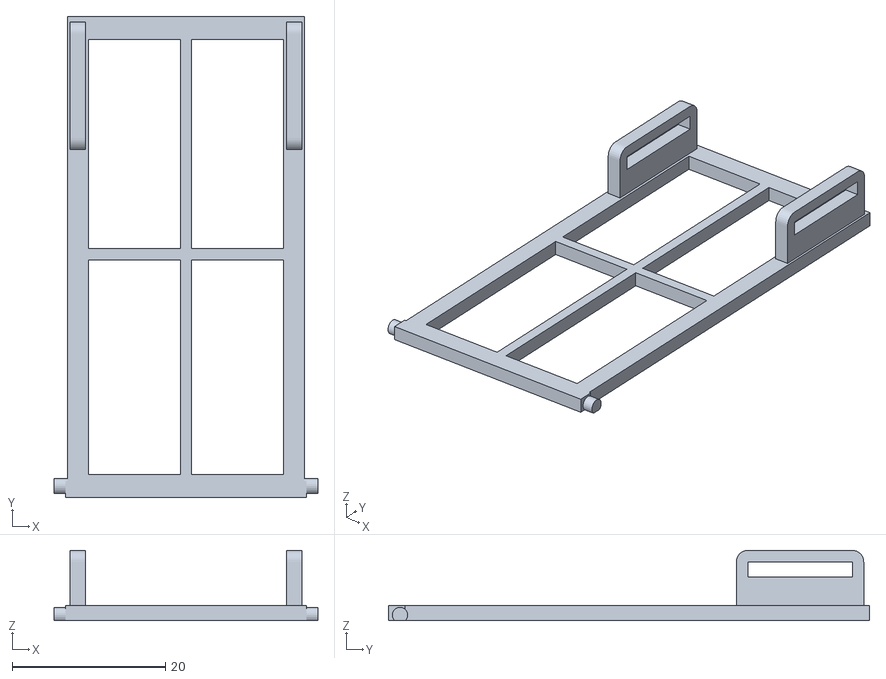
[picture p181: CAD file, 2021-07-27]
STL_SMARTHOME/Casa/Finestres/VidrieraPetita.stl
34.4 x 62.8 x 9.18
