maynej/Smart-Home/STL_SMARTHOME/Casa/Mobiliari/Bany/BanyeraRectangular.stl

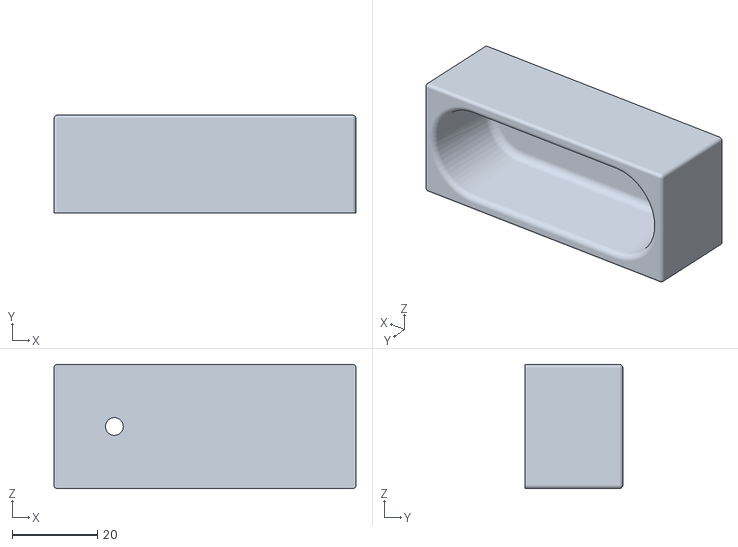
[picture p182: CAD file, 2021-07-27]
STL_SMARTHOME/Casa/Mobiliari/Bany/BanyeraRectangular.stl
70.8 x 22.9 x 29.2
