maynej/Smart-Home/STL_SMARTHOME/Casa/Mobiliari/Cuina/TapaRentadora.stl

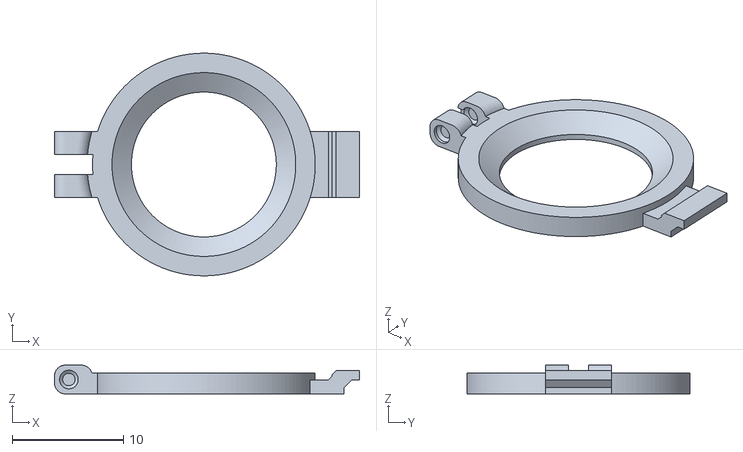
[picture p183: CAD file, 2021-07-27]
STL_SMARTHOME/Casa/Mobiliari/Cuina/TapaRentadora.stl
27.4 x 20.0 x 2.59
