maynej/Smart-Home/STL_SMARTHOME/Casa/Mobiliari/Dormitoris/Cadira.stl

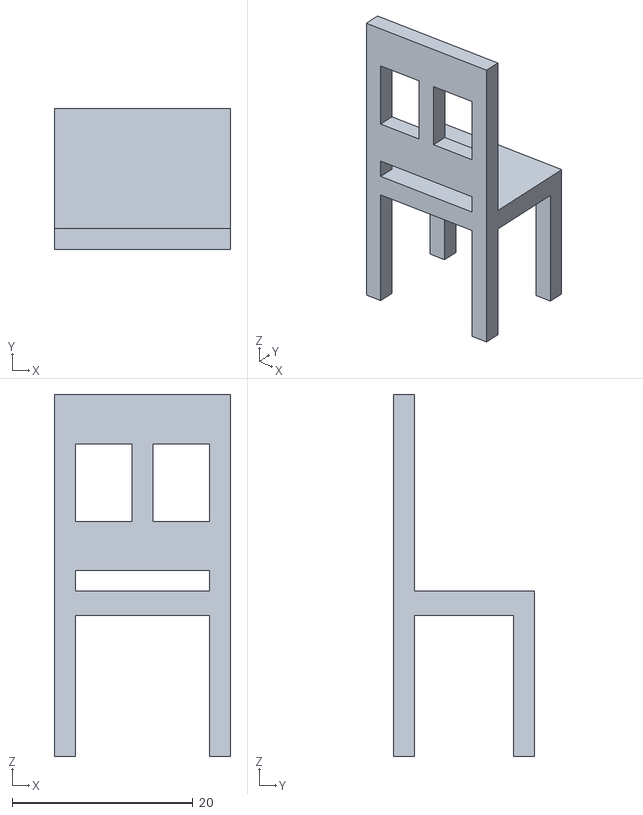
[picture p184: CAD file, 2021-07-27]
STL_SMARTHOME/Casa/Mobiliari/Dormitoris/Cadira.stl
19.5 x 15.6 x 40.1
