maynej/Smart-Home/STL_SMARTHOME/Casa/Mobiliari/Exterior/TaulaBase.stl

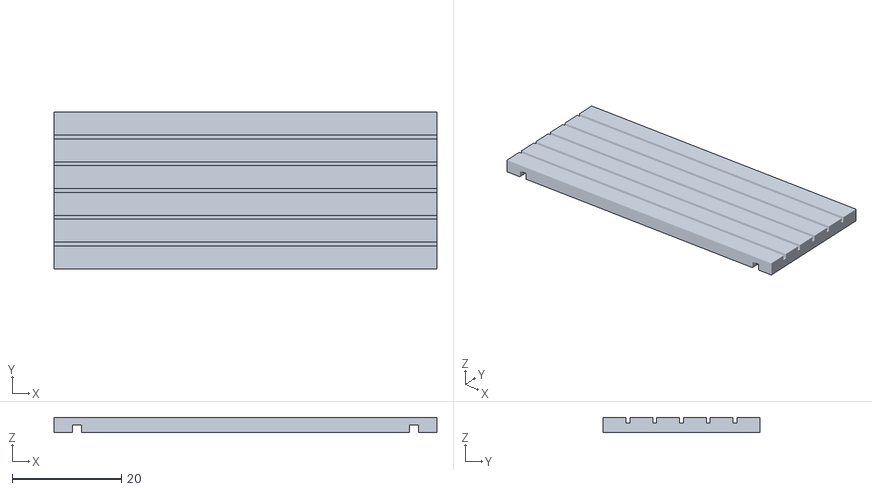
[picture p185: CAD file, 2021-07-27]
STL_SMARTHOME/Casa/Mobiliari/Exterior/TaulaBase.stl
70.0 x 28.7 x 2.80
