maynej/Smart-Home/STL_SMARTHOME/Casa/Mobiliari/Salo/Sofa3.stl

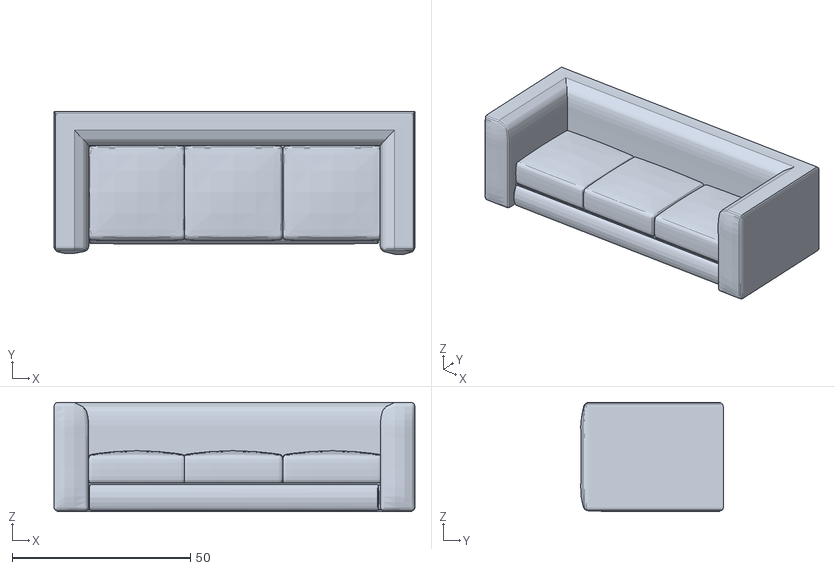
[picture p186: CAD file, 2021-07-27]
STL_SMARTHOME/Casa/Mobiliari/Salo/Sofa3.stl
101.3 x 40.0 x 30.6
