maynej/Smart-Home/STL_SMARTHOME/Casa/Parets/ParetA.stl

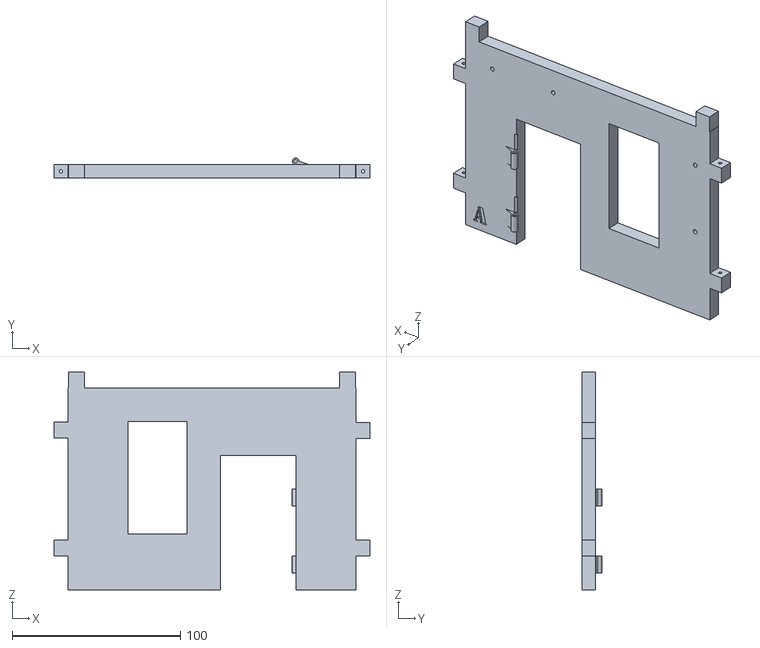
[picture p187: CAD file, 2021-07-27]
STL_SMARTHOME/Casa/Parets/ParetA.stl
188.0 x 12.0 x 129.5
