maynej/Smart-Home/STL_SMARTHOME/Casa/PatiGaratge/MurB.stl

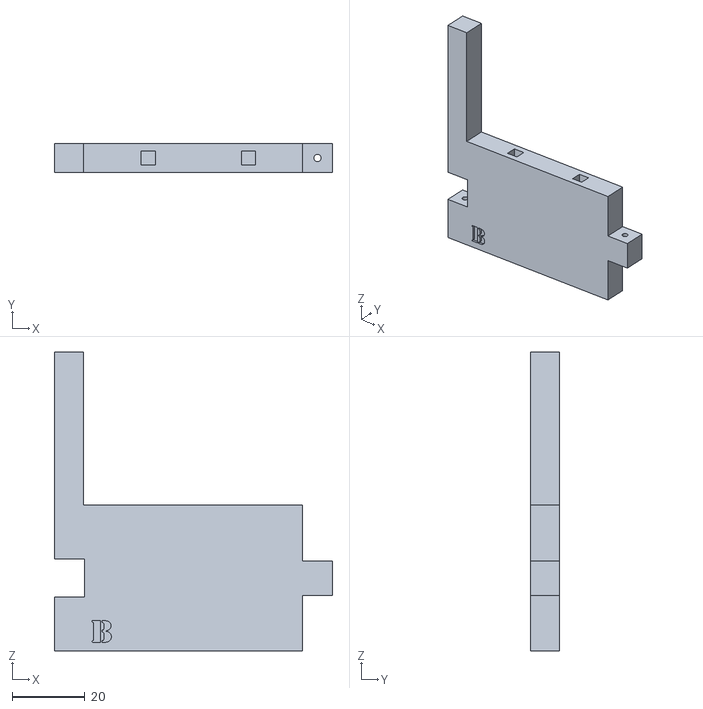
[picture p188: CAD file, 2021-07-27]
STL_SMARTHOME/Casa/PatiGaratge/MurB.stl
76.2 x 8.00 x 82.0
