maynej/Smart-Home/STL_SMARTHOME/Casa/Portes/Porta_Esquerra.stl

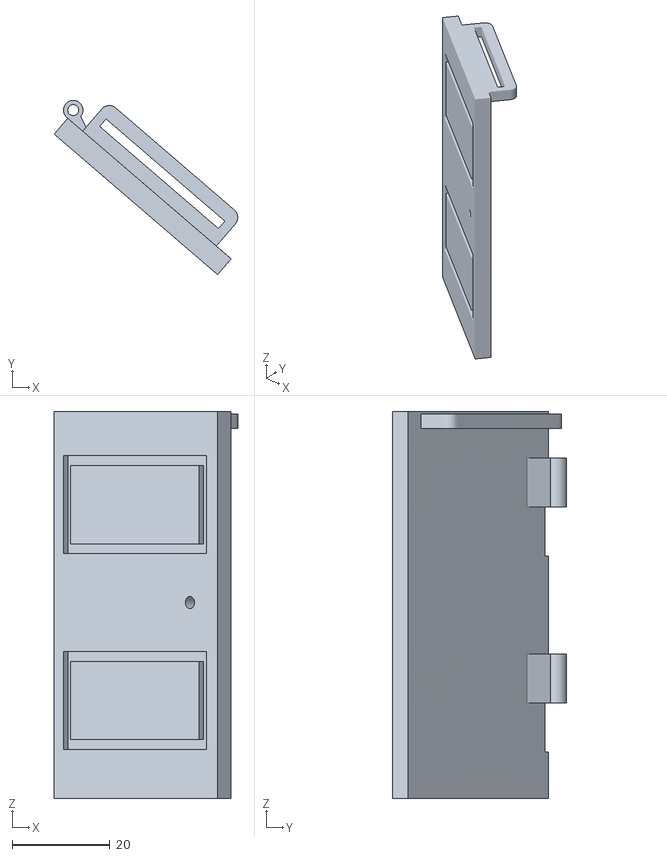
[picture p189: CAD file, 2021-07-27]
STL_SMARTHOME/Casa/Portes/Porta_Esquerra.stl
37.5 x 35.6 x 79.0
