maynej/Smart-Home/STL_SMARTHOME/Casa/Teulada/Suport_Teulada Frontal/SuportTeuladaB.stl

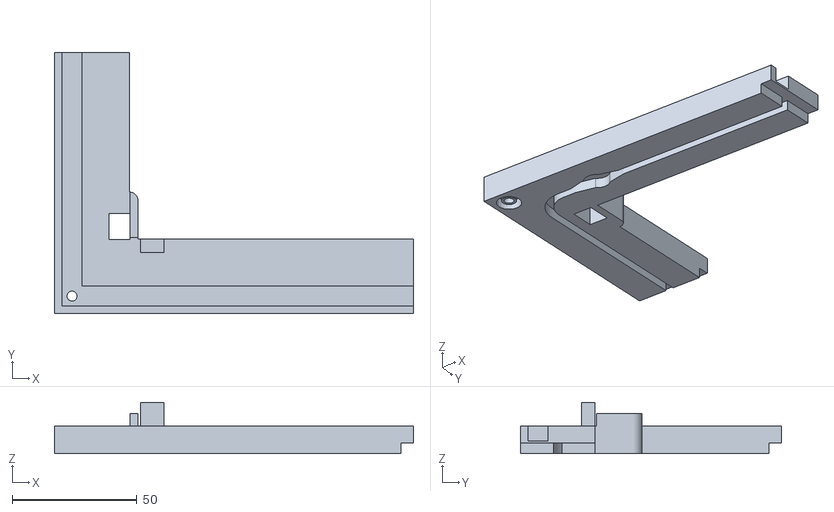
[picture p190: CAD file, 2021-07-27]
STL_SMARTHOME/Casa/Teulada/Suport_Teulada Frontal/SuportTeuladaB.stl
143.9 x 104.7 x 20.5
