maynej/Smart-Home/STL_SMARTHOME/Casa/Teulada/Teulada Frontal/TeuladaFrontal_e.stl

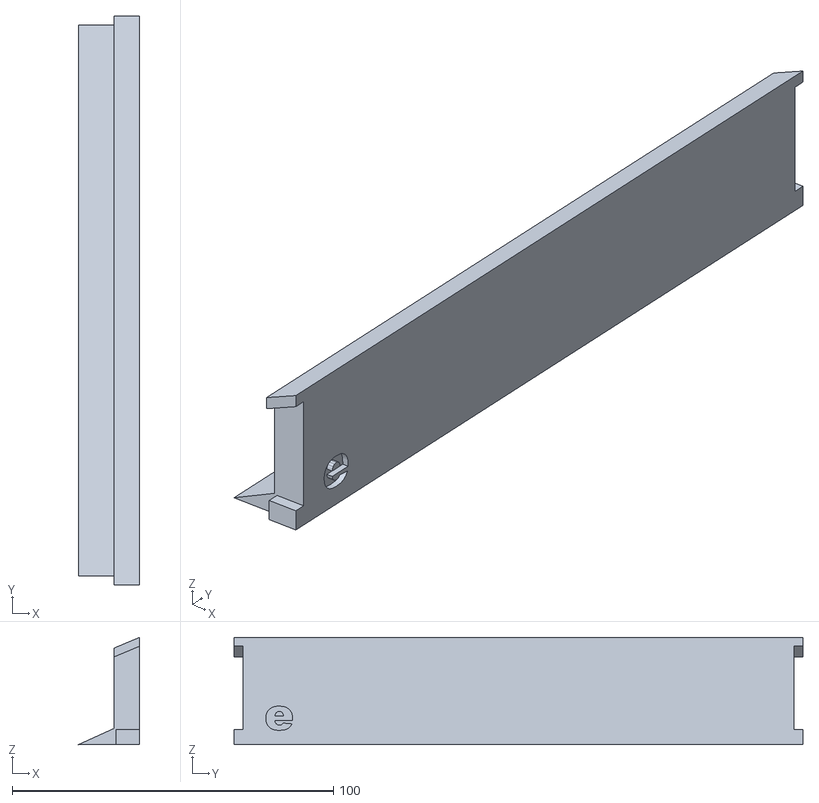
[picture p191: CAD file, 2021-07-27]
STL_SMARTHOME/Casa/Teulada/Teulada Frontal/TeuladaFrontal_e.stl
19.0 x 177.0 x 33.3
