maynej/Smart-Home/STL_SMARTHOME/Casa/Teulada/Teulada Posterior/TeulatVerdE1.stl

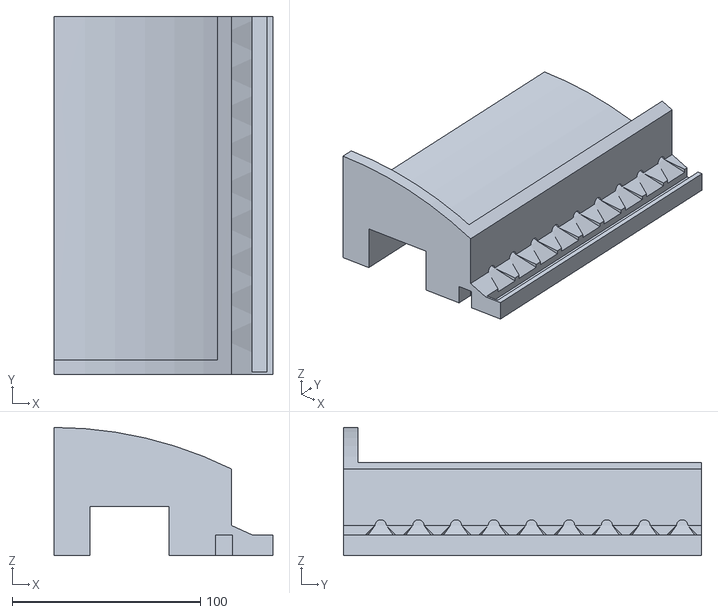
[picture p192: CAD file, 2021-07-27]
STL_SMARTHOME/Casa/Teulada/Teulada Posterior/TeulatVerdE1.stl
116.0 x 190.0 x 68.0
