maynej/Smart-Home/STL_SMARTHOME/Casa/Vorera/VoreraEsquerraPedres2.stl

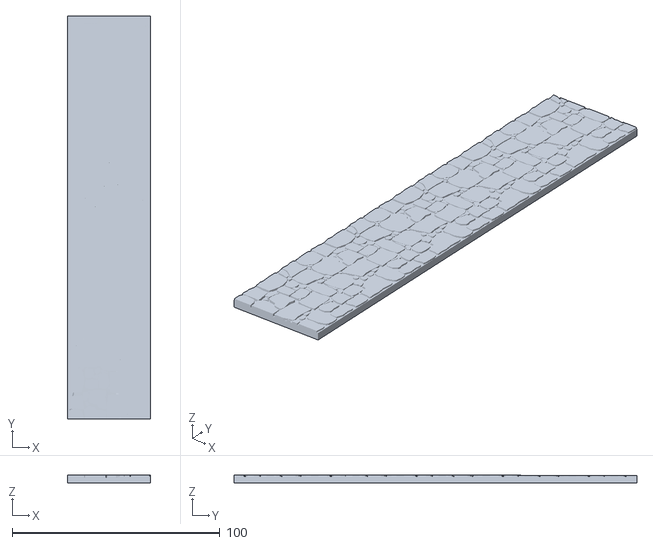
[picture p193: CAD file, 2021-07-27]
STL_SMARTHOME/Casa/Vorera/VoreraEsquerraPedres2.stl
40.0 x 194.0 x 3.70
