maynej/Smart-Home/STL_SMARTHOME/Garatge/GaratgeB.stl

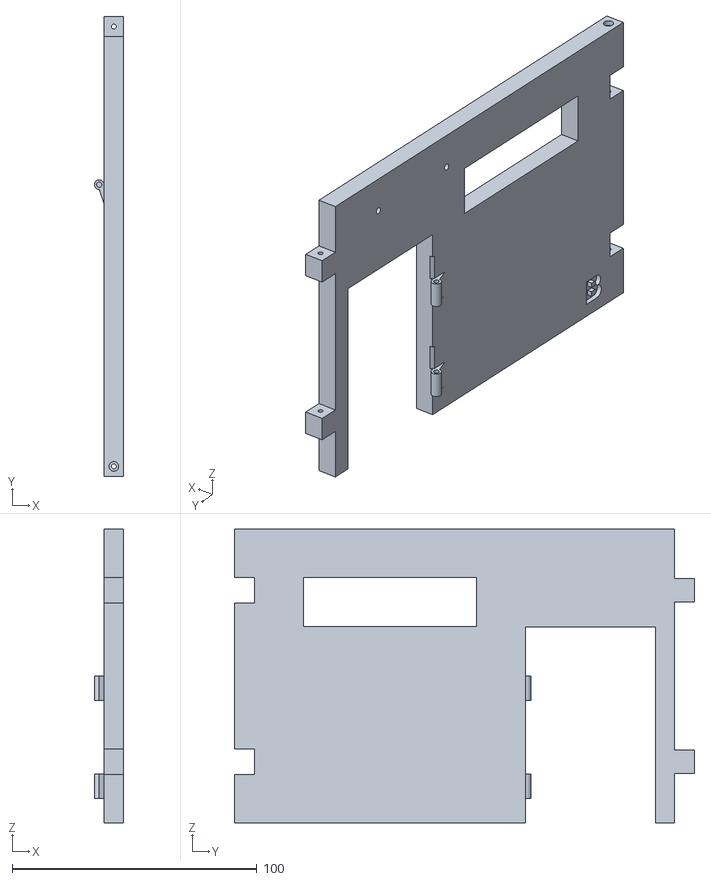
[picture p194: CAD file, 2021-07-27]
STL_SMARTHOME/Garatge/GaratgeB.stl
12.0 x 188.0 x 120.0
