maynej/Smart-Home/STL_SMARTHOME/Jardi/GeneradorEolic/Poste1.stl

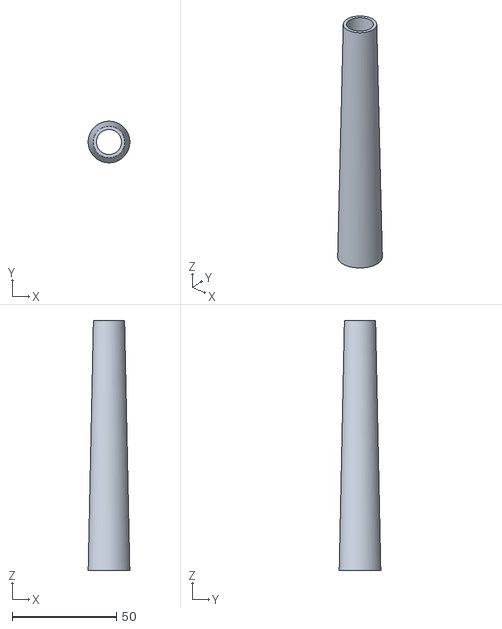
[picture p195: CAD file, 2021-07-27]
STL_SMARTHOME/Jardi/GeneradorEolic/Poste1.stl
20.0 x 20.0 x 120.0
