maynej/Smart-Home/STL_SMARTHOME/Jardi/Piscina.stl

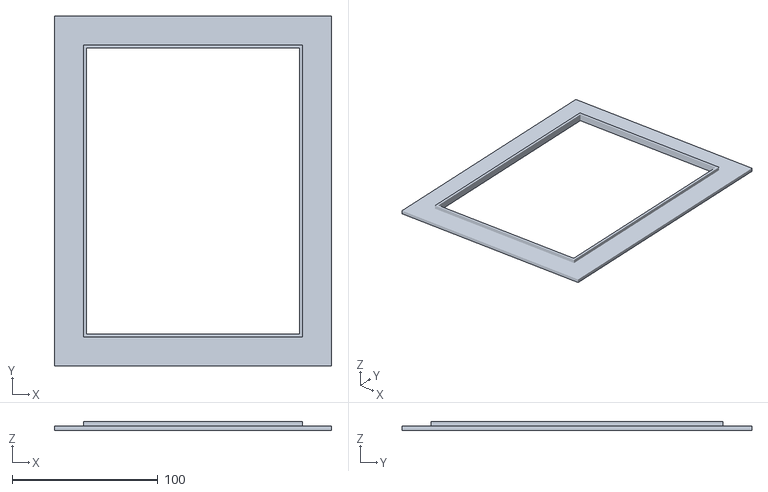
[picture p196: CAD file, 2021-07-27]
STL_SMARTHOME/Jardi/Piscina.stl
190.0 x 240.0 x 6.00
