maynej/Smart-Home/STL_SMARTHOME/Jardi/SeguidorSolar/BaseSuperiorSolar.STL

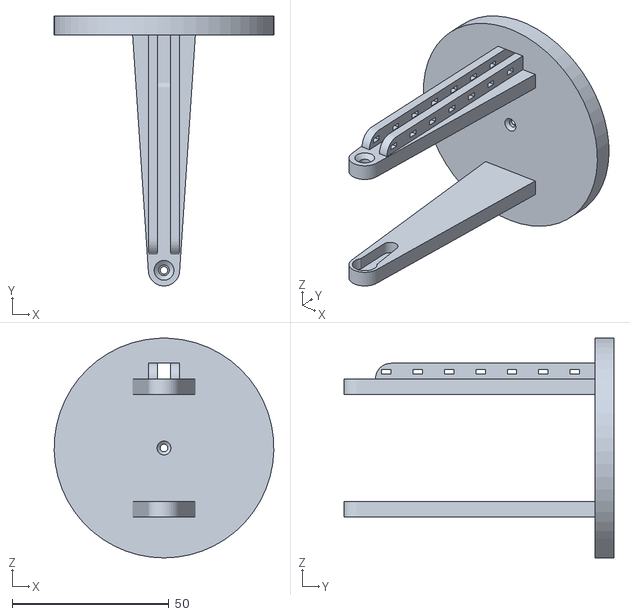
[picture p197: CAD file, 2021-07-27]
STL_SMARTHOME/Jardi/SeguidorSolar/BaseSuperiorSolar.STL
70.0 x 86.0 x 70.0
