maynej/Smart-Home/STL_SMARTHOME/Jardi/TurbinaAigua/rain-water-tank-ver.stl

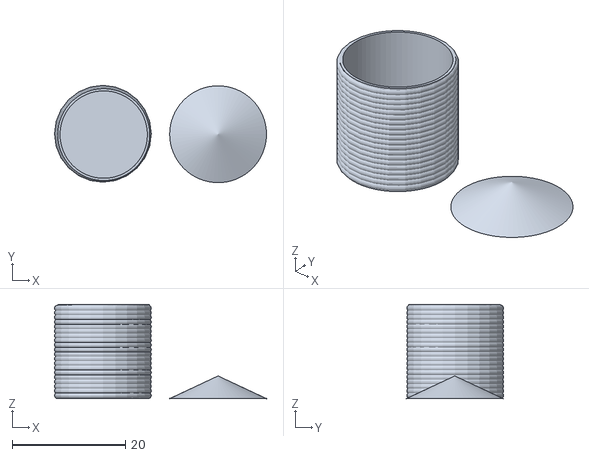
[picture p198: CAD file, 2021-07-27]
STL_SMARTHOME/Jardi/TurbinaAigua/rain-water-tank-ver.stl
37.4 x 17.2 x 16.6
