maynej/Smart-Home/STL_SMARTHOME/Casa/AireCondicionat/TubEsquerraA.stl

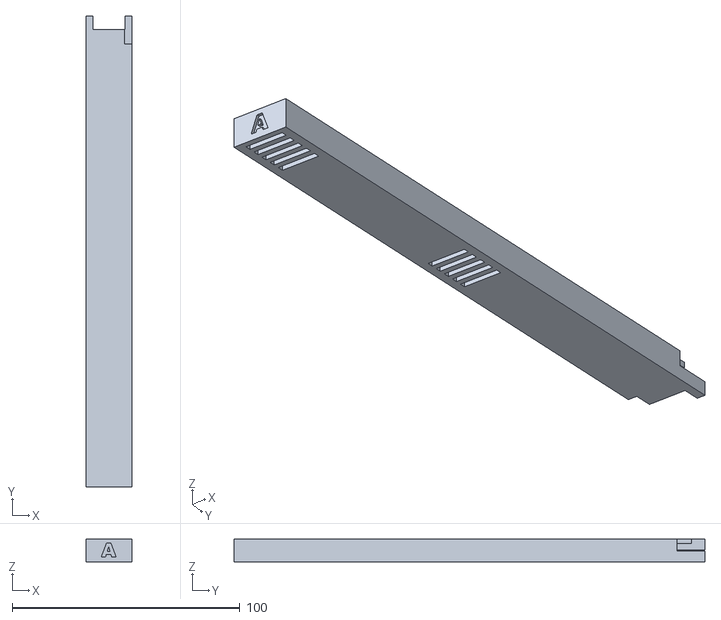
[picture p199: CAD file, 2021-07-27]
STL_SMARTHOME/Casa/AireCondicionat/TubEsquerraA.stl
20.0 x 207.0 x 10.00
