maynej/Smart-Home/STL_SMARTHOME/Casa/Ascensor/Ascensor1A_Motor.stl

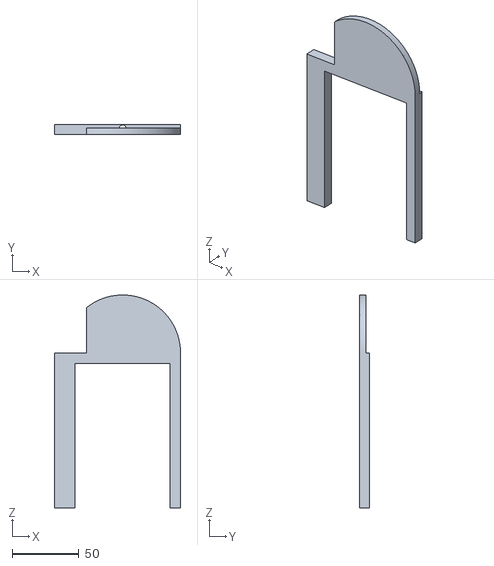
[picture p200: CAD file, 2021-07-27]
STL_SMARTHOME/Casa/Ascensor/Ascensor1A_Motor.stl
94.2 x 7.77 x 159.2
