maynej/Smart-Home/STL_SMARTHOME/Casa/Finestres/VidrieraCuina.stl

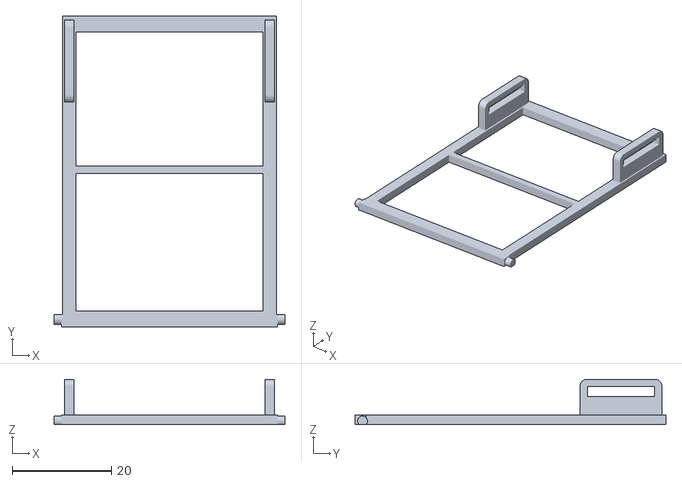
[picture p201: CAD file, 2021-07-27]
STL_SMARTHOME/Casa/Finestres/VidrieraCuina.stl
46.6 x 62.8 x 9.18
