maynej/Smart-Home/STL_SMARTHOME/Casa/Mobiliari/Bany/BanyeraGran.stl

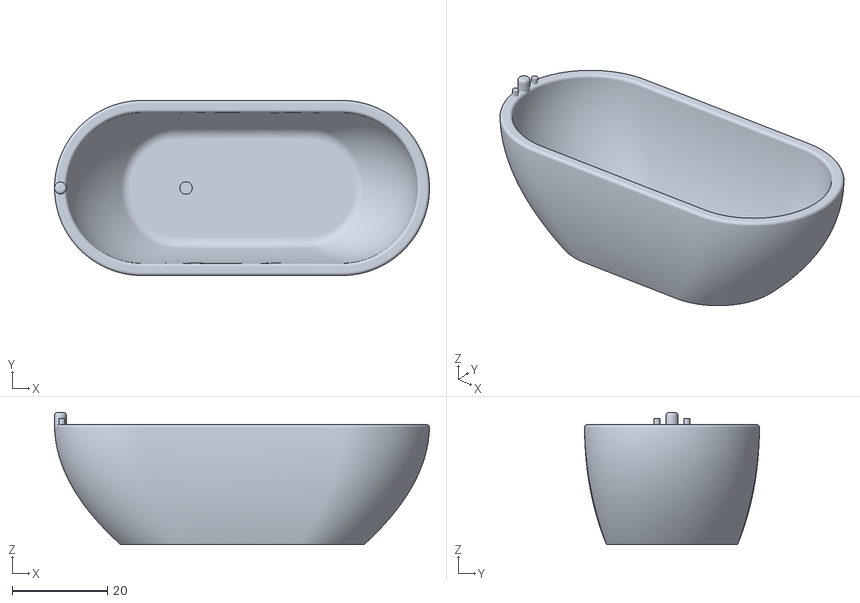
[picture p202: CAD file, 2021-07-27]
STL_SMARTHOME/Casa/Mobiliari/Bany/BanyeraGran.stl
78.7 x 36.7 x 27.7
