maynej/Smart-Home/STL_SMARTHOME/Casa/Mobiliari/Cuina/Rentadora.stl

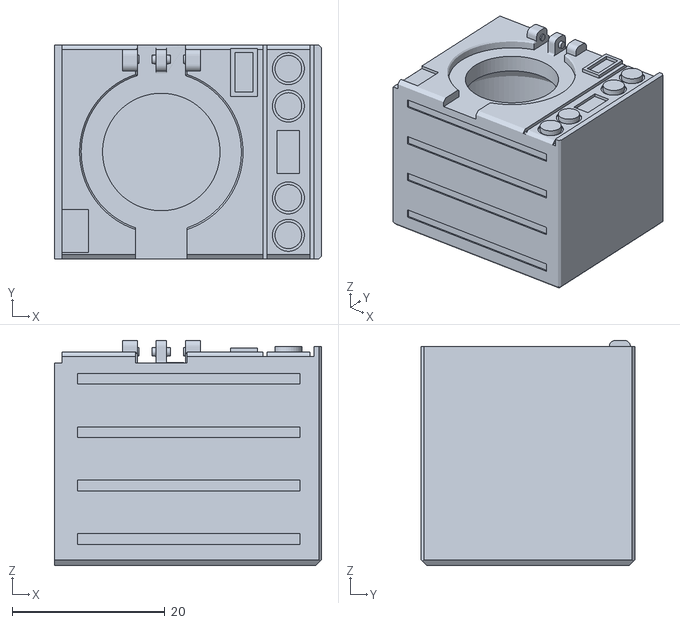
[picture p203: CAD file, 2021-07-27]
STL_SMARTHOME/Casa/Mobiliari/Cuina/Rentadora.stl
35.0 x 28.0 x 29.5
