maynej/Smart-Home/STL_SMARTHOME/Casa/Mobiliari/Dormitoris/Estanteria.stl

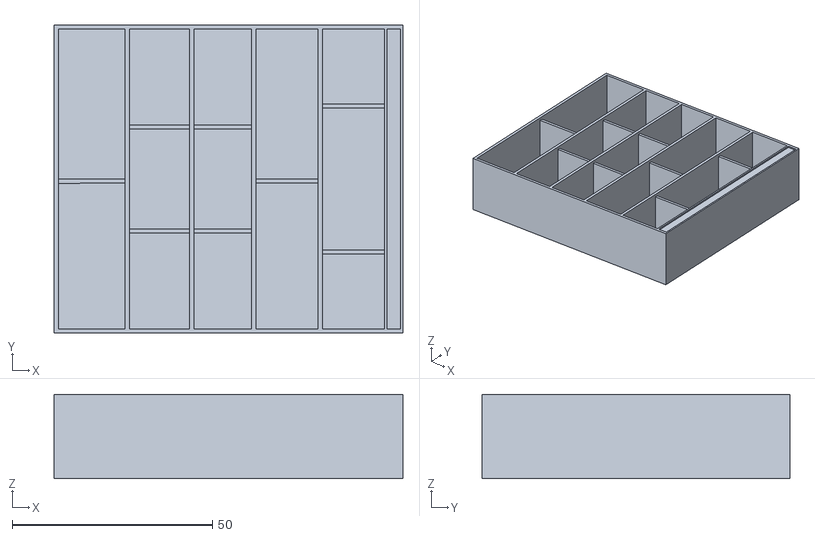
[picture p204: CAD file, 2021-07-27]
STL_SMARTHOME/Casa/Mobiliari/Dormitoris/Estanteria.stl
87.1 x 77.0 x 21.0
