maynej/Smart-Home/STL_SMARTHOME/Casa/Mobiliari/Exterior/TaulaPotes2.stl

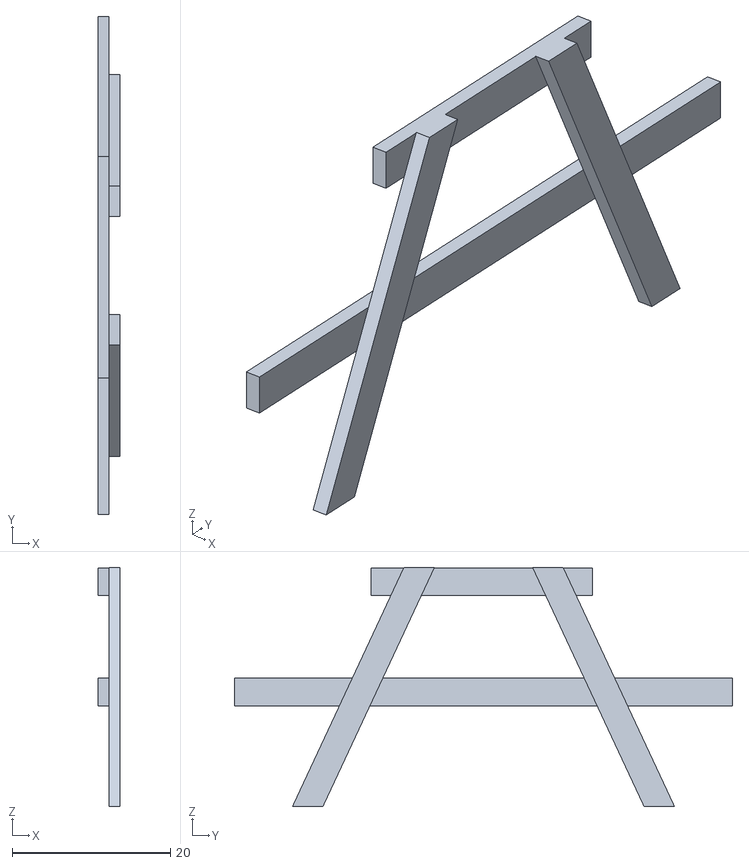
[picture p205: CAD file, 2021-07-27]
STL_SMARTHOME/Casa/Mobiliari/Exterior/TaulaPotes2.stl
2.80 x 63.0 x 30.2
