maynej/Smart-Home/STL_SMARTHOME/Casa/Mobiliari/Salo/TauletaSofa.stl

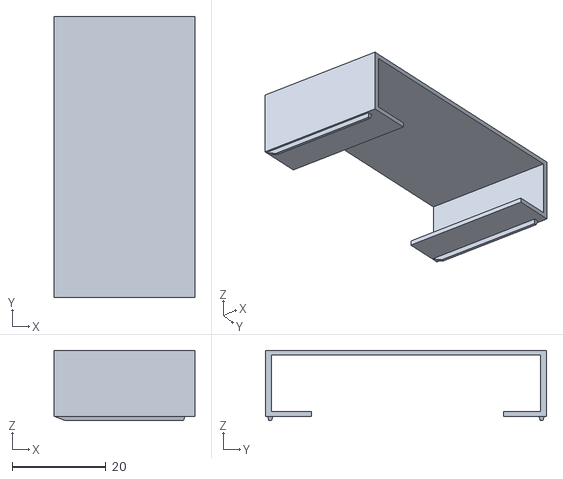
[picture p206: CAD file, 2021-07-27]
STL_SMARTHOME/Casa/Mobiliari/Salo/TauletaSofa.stl
30.0 x 60.0 x 15.0
