maynej/Smart-Home/STL_SMARTHOME/Casa/Parets/ReixaMur.stl

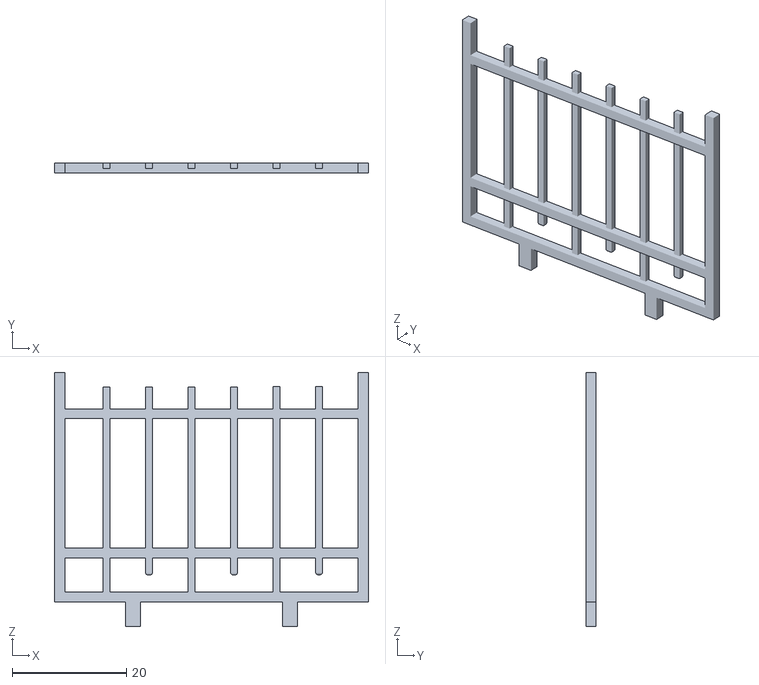
[picture p207: CAD file, 2021-07-27]
STL_SMARTHOME/Casa/Parets/ReixaMur.stl
54.9 x 1.73 x 44.5
