maynej/Smart-Home/STL_SMARTHOME/Casa/PatiGaratge/MurD.stl

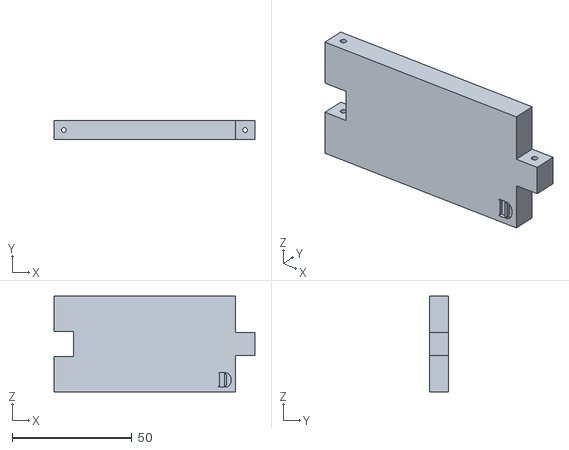
[picture p208: CAD file, 2021-07-27]
STL_SMARTHOME/Casa/PatiGaratge/MurD.stl
84.0 x 8.00 x 40.0
