maynej/Smart-Home/STL_SMARTHOME/Casa/Portes/EixCorredera.stl

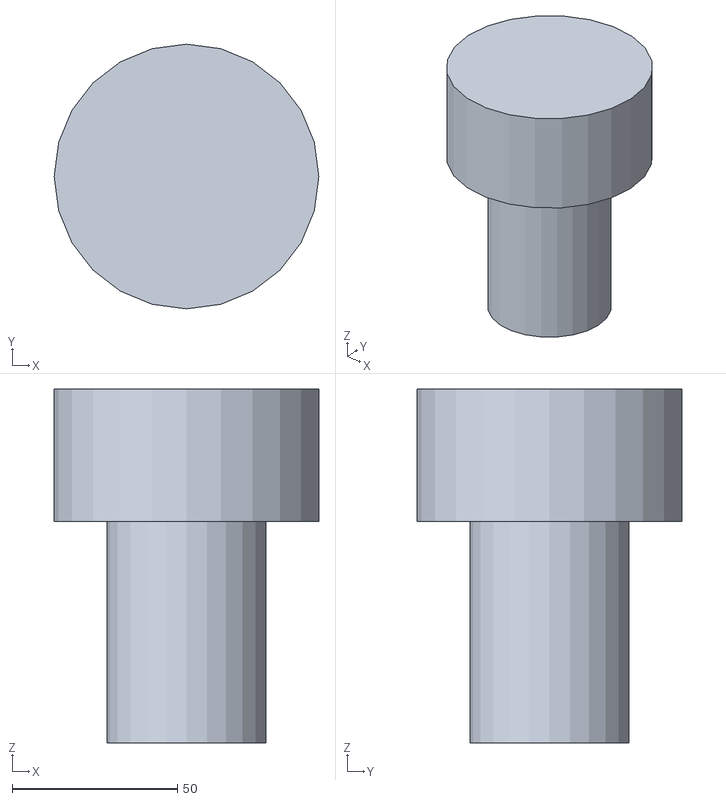
[picture p209: CAD file, 2021-07-27]
STL_SMARTHOME/Casa/Portes/EixCorredera.stl
80.0 x 80.0 x 107.0
