maynej/Smart-Home/STL_SMARTHOME/Casa/Teulada/Suport_Teulada Frontal/SuportTeuladaG.stl

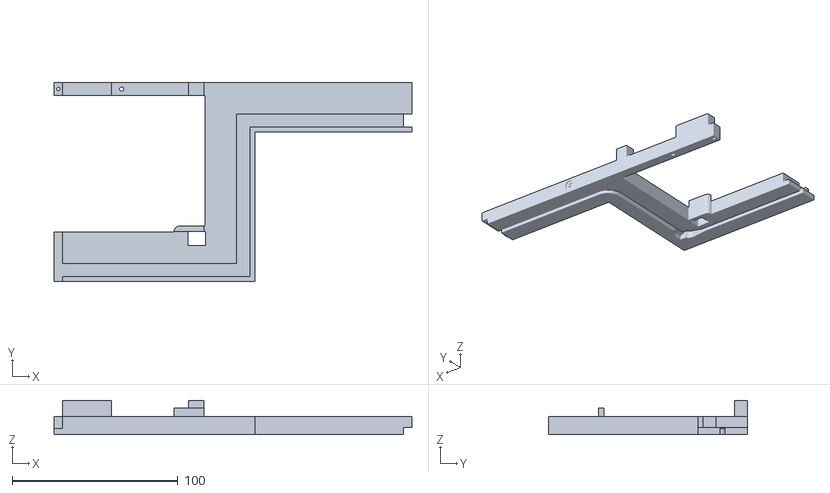
[picture p210: CAD file, 2021-07-27]
STL_SMARTHOME/Casa/Teulada/Suport_Teulada Frontal/SuportTeuladaG.stl
215.7 x 120.0 x 20.5
