maynej/Smart-Home/STL_SMARTHOME/Casa/Teulada/Teulada Frontal/TeuladaFrontal_b.stl

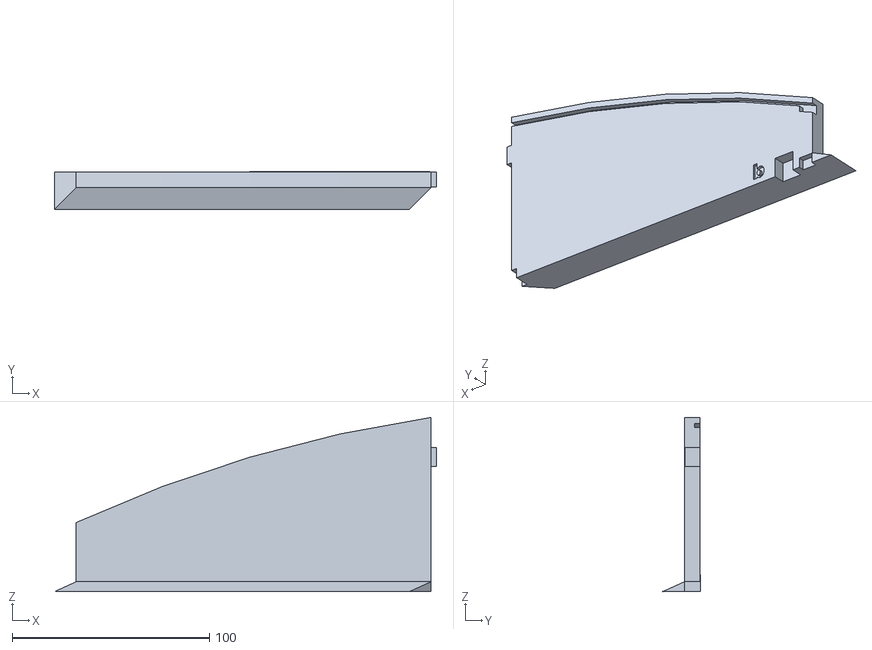
[picture p211: CAD file, 2021-07-27]
STL_SMARTHOME/Casa/Teulada/Teulada Frontal/TeuladaFrontal_b.stl
193.5 x 19.0 x 88.2
