maynej/Smart-Home/STL_SMARTHOME/Casa/Teulada/Teulada Posterior/TeulatVerdD3.stl

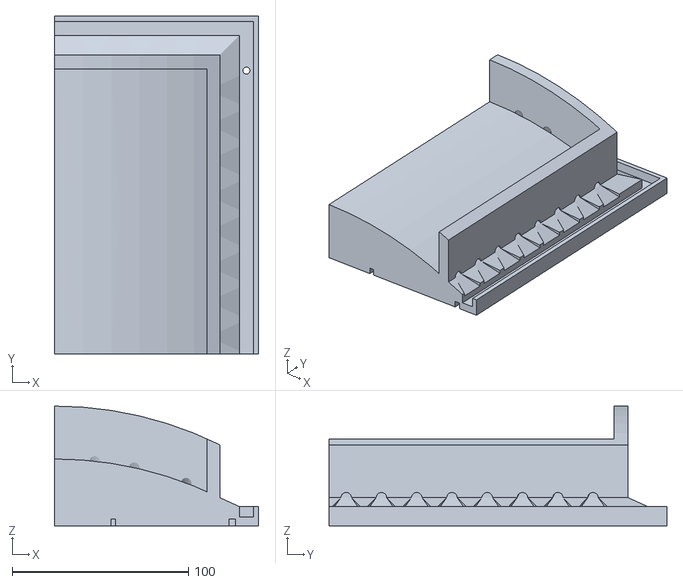
[picture p212: CAD file, 2021-07-27]
STL_SMARTHOME/Casa/Teulada/Teulada Posterior/TeulatVerdD3.stl
116.0 x 191.7 x 68.0
