maynej/Smart-Home/STL_SMARTHOME/Casa/Vorera/VoreraEsquerraPedres1.stl

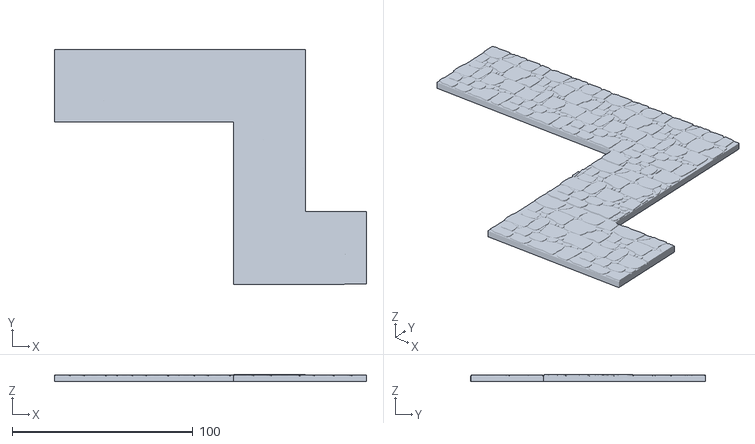
[picture p213: CAD file, 2021-07-27]
STL_SMARTHOME/Casa/Vorera/VoreraEsquerraPedres1.stl
172.7 x 130.0 x 3.88
