maynej/Smart-Home/STL_SMARTHOME/Garatge/ClipPortaGaratge.stl

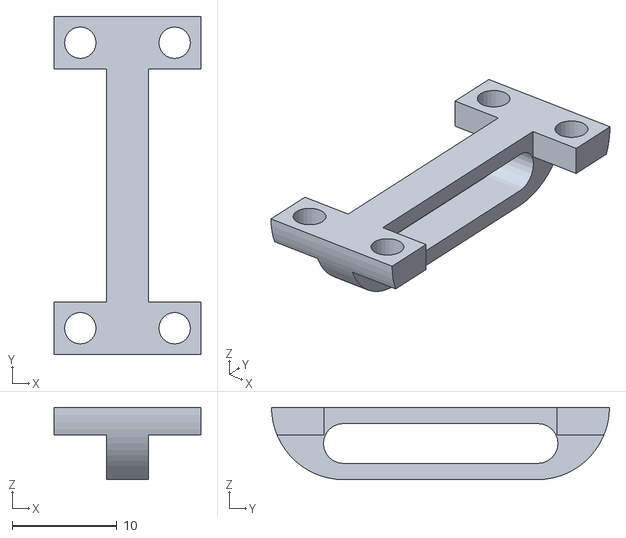
[picture p214: CAD file, 2021-07-27]
STL_SMARTHOME/Garatge/ClipPortaGaratge.stl
14.0 x 32.2 x 6.90
