maynej/Smart-Home/STL_SMARTHOME/Jardi/GeneradorEolic/Poste2.stl

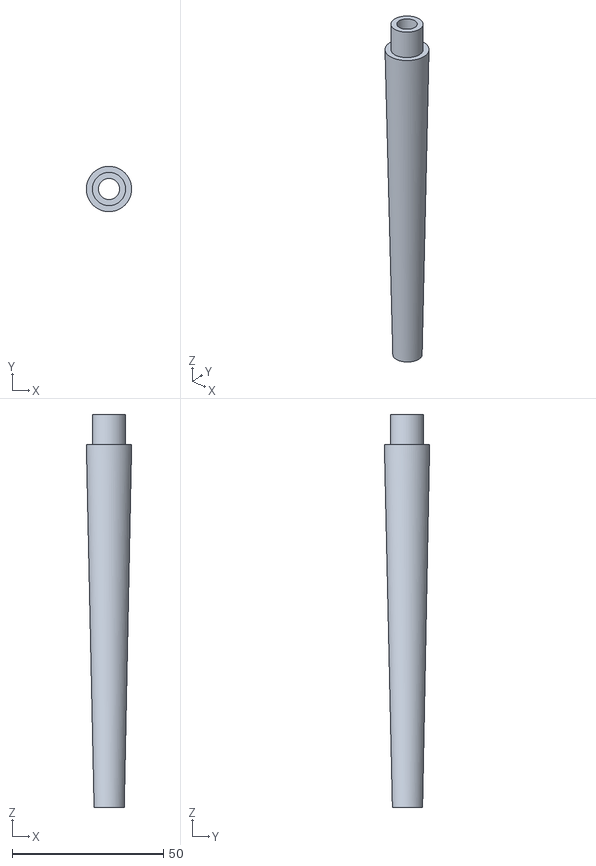
[picture p215: CAD file, 2021-07-27]
STL_SMARTHOME/Jardi/GeneradorEolic/Poste2.stl
15.0 x 15.0 x 130.0
