maynej/Smart-Home/STL_SMARTHOME/Jardi/SeguidorSolar/BaseInferiorSolar.stl

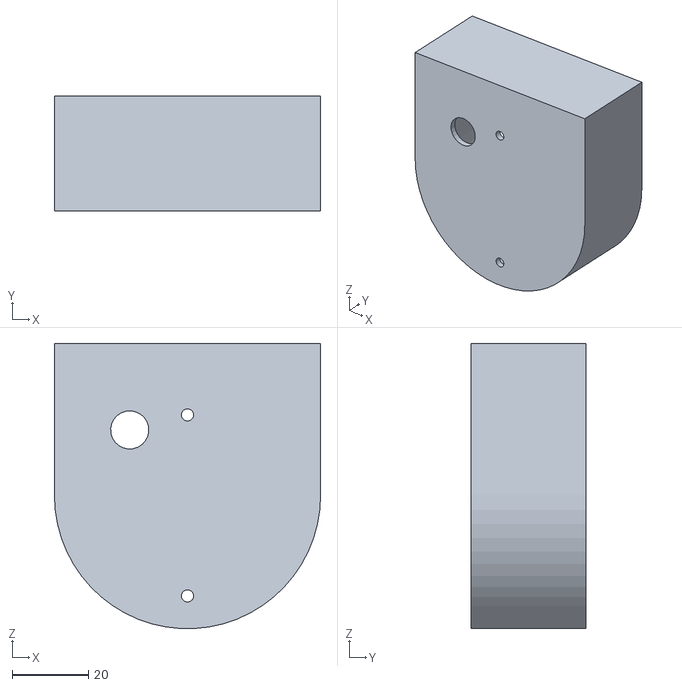
[picture p216: CAD file, 2021-07-27]
STL_SMARTHOME/Jardi/SeguidorSolar/BaseInferiorSolar.stl
70.0 x 30.1 x 74.9
