maynej/Smart-Home/STL_SMARTHOME/Jardi/TurbinaAigua/Duct.STL

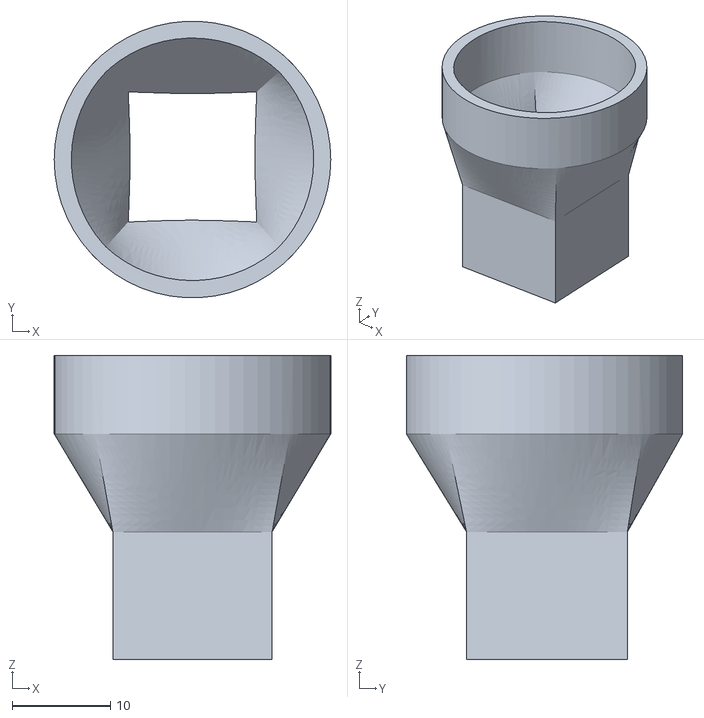
[picture p217: CAD file, 2021-07-27]
STL_SMARTHOME/Jardi/TurbinaAigua/Duct.STL
28.2 x 28.2 x 31.0
