maynej/Smart-Home/STL_SMARTHOME/Casa/Ascensor/Acoblador.stl

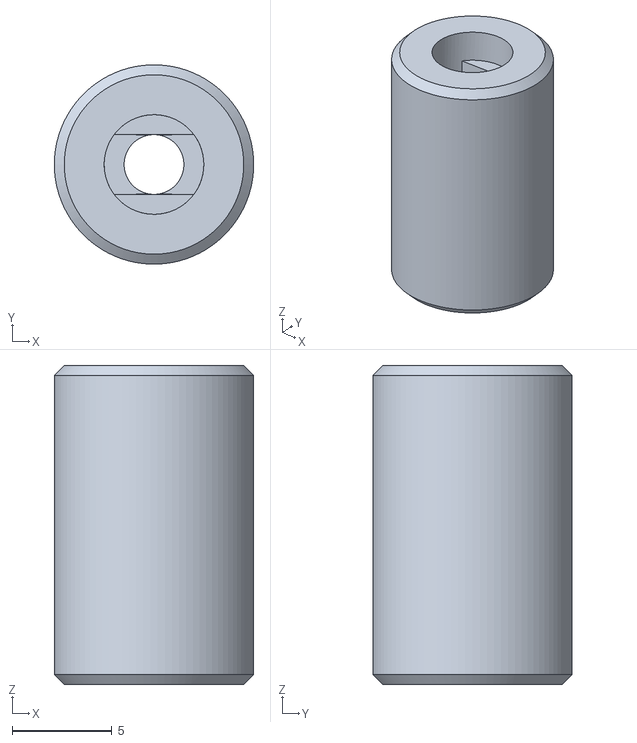
[picture p218: CAD file, 2021-07-27]
STL_SMARTHOME/Casa/Ascensor/Acoblador.stl
10.0 x 9.99 x 16.0
