maynej/Smart-Home/STL_SMARTHOME/Casa/Finestres/MarcFinestraGran.stl

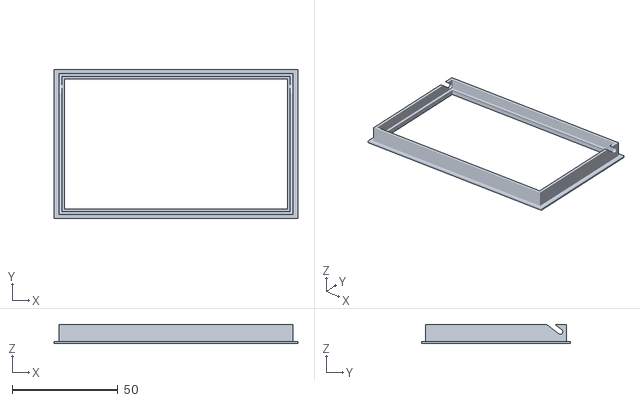
[picture p219: CAD file, 2021-07-27]
STL_SMARTHOME/Casa/Finestres/MarcFinestraGran.stl
115.2 x 70.3 x 9.06
