maynej/Smart-Home/STL_SMARTHOME/Casa/Mobiliari/Dormitoris/LlitIndividual.stl

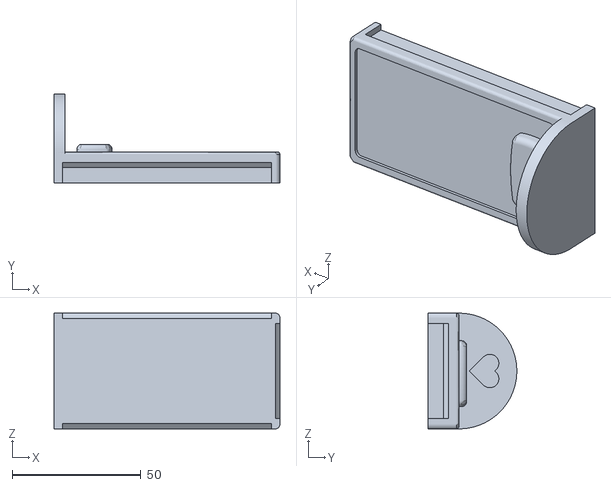
[picture p220: CAD file, 2021-07-27]
STL_SMARTHOME/Casa/Mobiliari/Dormitoris/LlitIndividual.stl
87.9 x 34.5 x 45.0
