maynej/Smart-Home/STL_SMARTHOME/Casa/Mobiliari/Salo/Llibreria.stl

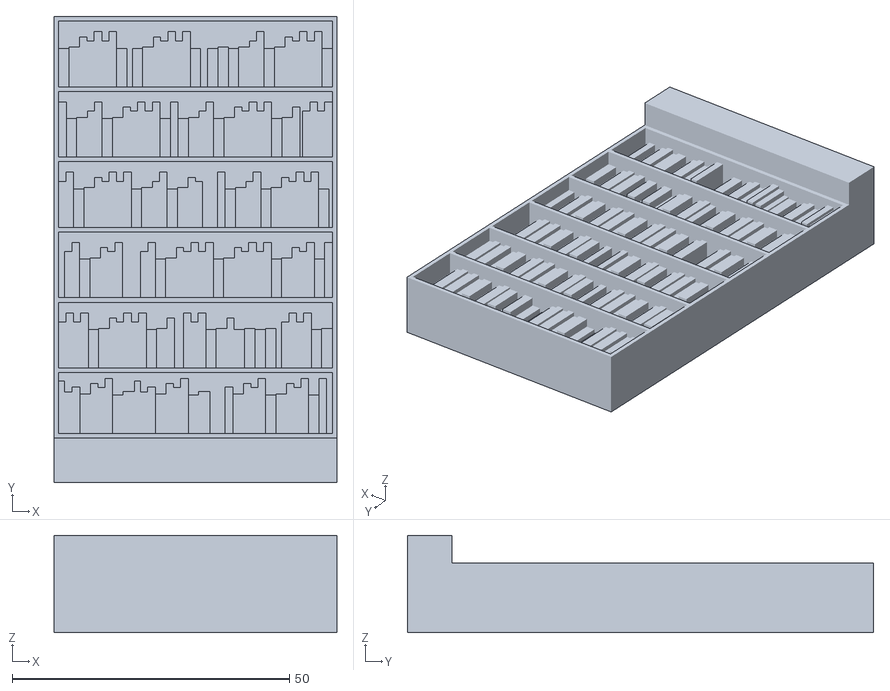
[picture p221: CAD file, 2021-07-27]
STL_SMARTHOME/Casa/Mobiliari/Salo/Llibreria.stl
51.0 x 84.0 x 17.5
