maynej/Smart-Home/STL_SMARTHOME/Casa/Parets/ParetG.stl

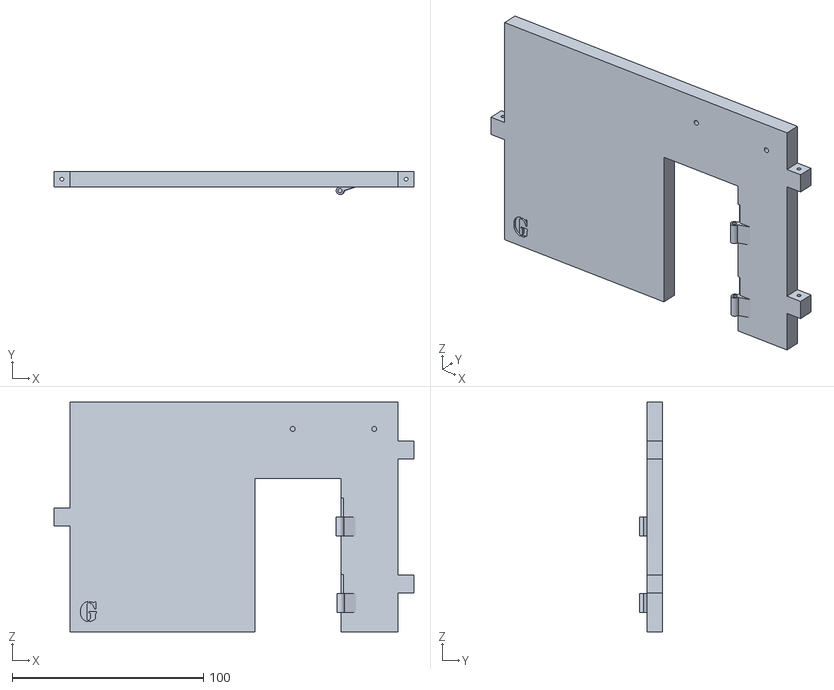
[picture p222: CAD file, 2021-07-27]
STL_SMARTHOME/Casa/Parets/ParetG.stl
188.0 x 12.0 x 120.0
