maynej/Smart-Home/STL_SMARTHOME/Casa/PatiGaratge/MurC.stl

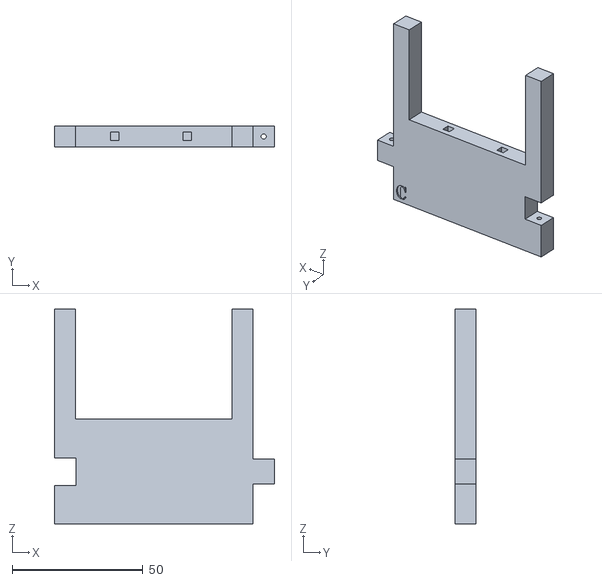
[picture p223: CAD file, 2021-07-27]
STL_SMARTHOME/Casa/PatiGaratge/MurC.stl
84.0 x 8.00 x 82.0
