maynej/Smart-Home/STL_SMARTHOME/Casa/Portes/EixCorredera2.stl

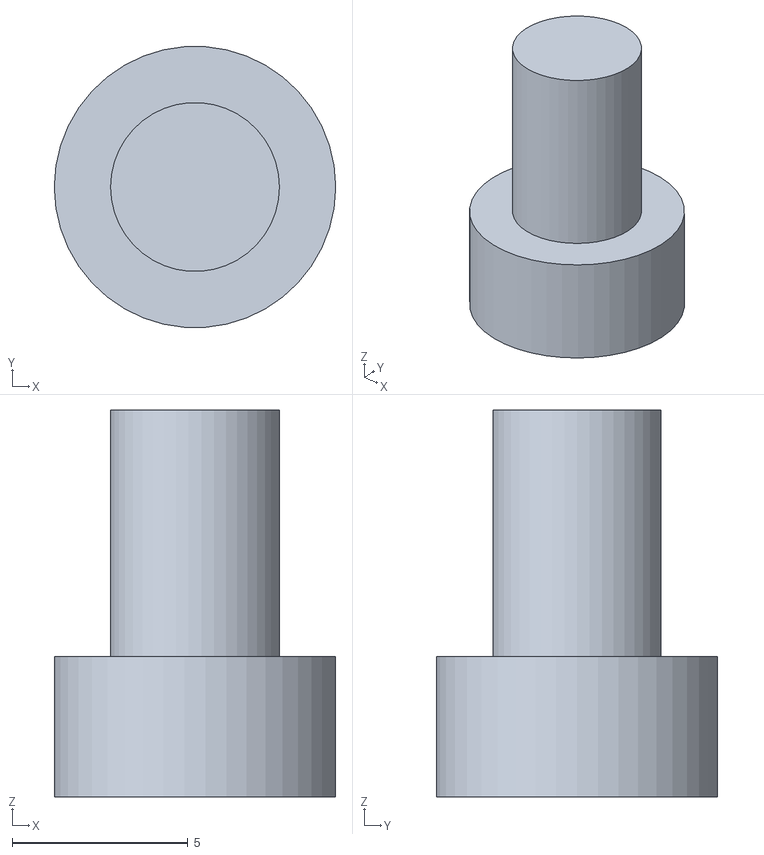
[picture p224: CAD file, 2021-07-27]
STL_SMARTHOME/Casa/Portes/EixCorredera2.stl
8.00 x 7.98 x 11.0
