maynej/Smart-Home/STL_SMARTHOME/Casa/Teulada/Suport_Teulada Frontal/SuportTeuladaC.stl

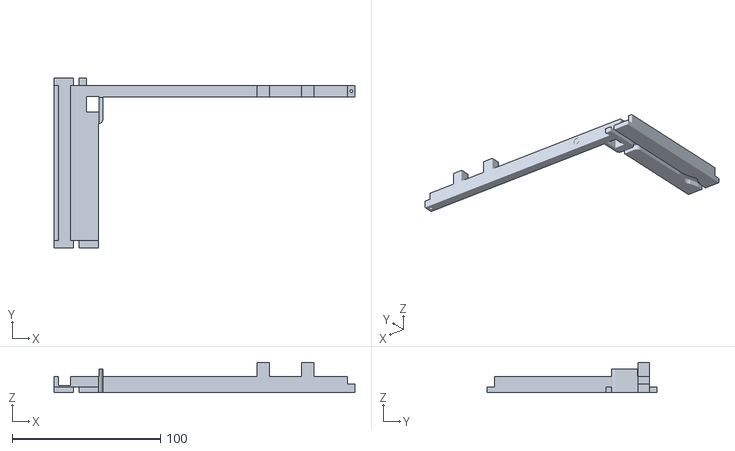
[picture p225: CAD file, 2021-07-27]
STL_SMARTHOME/Casa/Teulada/Suport_Teulada Frontal/SuportTeuladaC.stl
202.7 x 114.5 x 20.5
