maynej/Smart-Home/STL_SMARTHOME/Casa/Vorera/VoreraEsquerraPedres4.stl

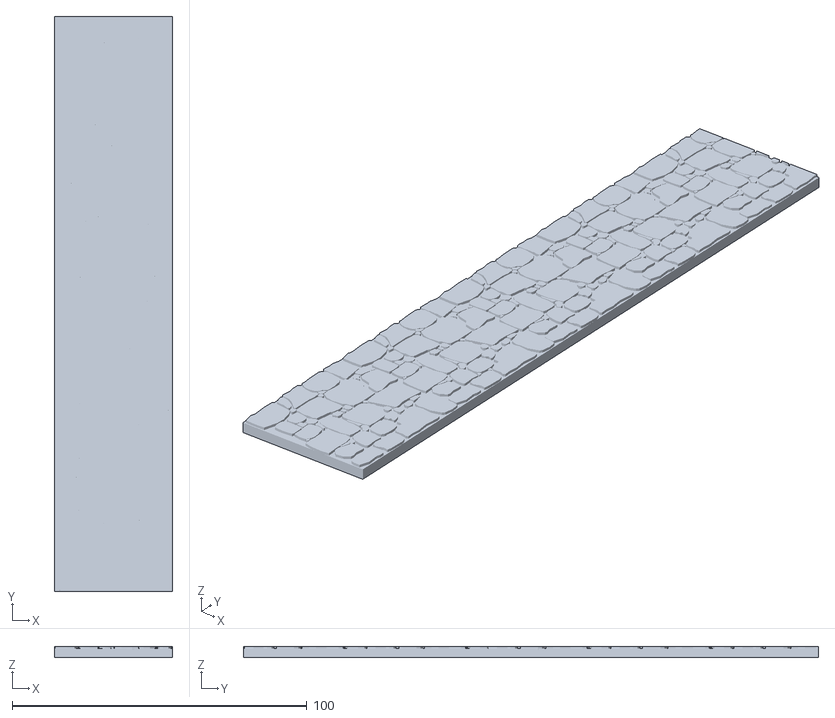
[picture p226: CAD file, 2021-07-27]
STL_SMARTHOME/Casa/Vorera/VoreraEsquerraPedres4.stl
40.0 x 195.1 x 3.76
