maynej/Smart-Home/STL_SMARTHOME/Garatge/PortaSuperiorGaratge.stl

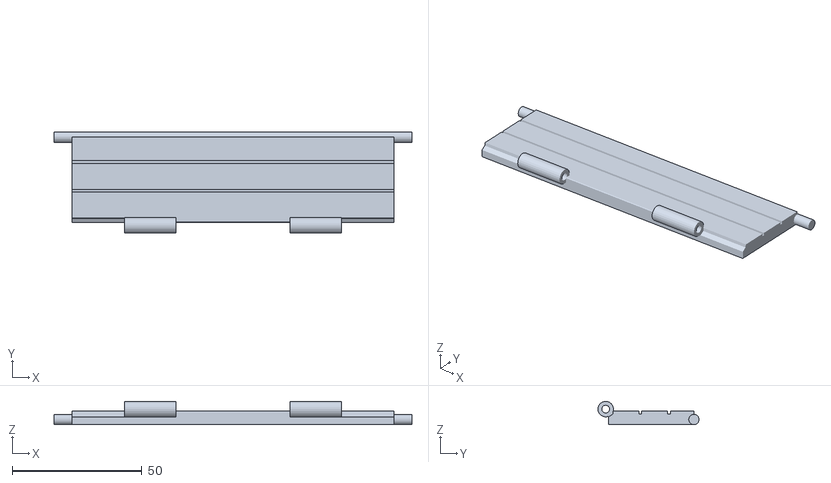
[picture p227: CAD file, 2021-07-27]
STL_SMARTHOME/Garatge/PortaSuperiorGaratge.stl
138.0 x 39.0 x 9.00
