maynej/Smart-Home/STL_SMARTHOME/Jardi/GeneradorEolic/PuntaPales.stl

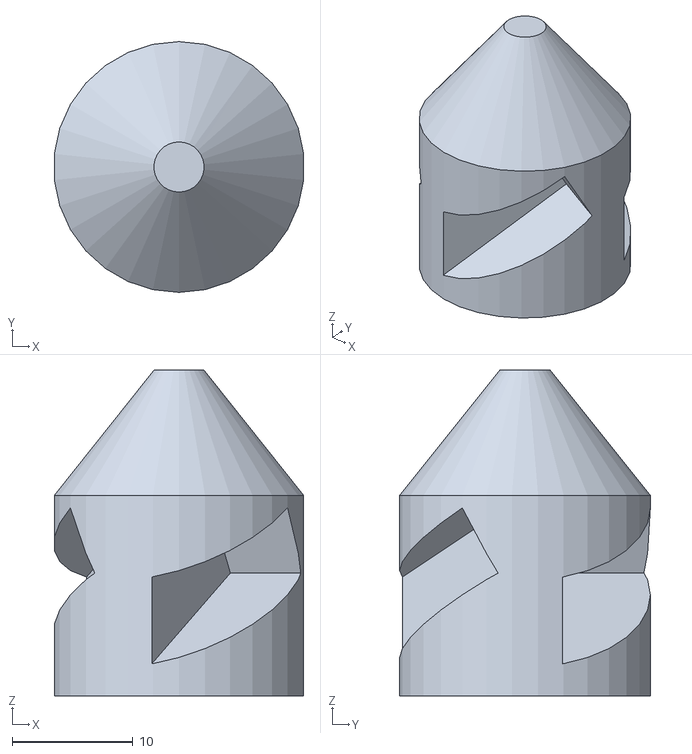
[picture p228: CAD file, 2021-07-27]
STL_SMARTHOME/Jardi/GeneradorEolic/PuntaPales.stl
20.7 x 20.8 x 27.0
