maynej/Smart-Home/STL_SMARTHOME/Jardi/SeguidorSolar/SuportLDR.STL

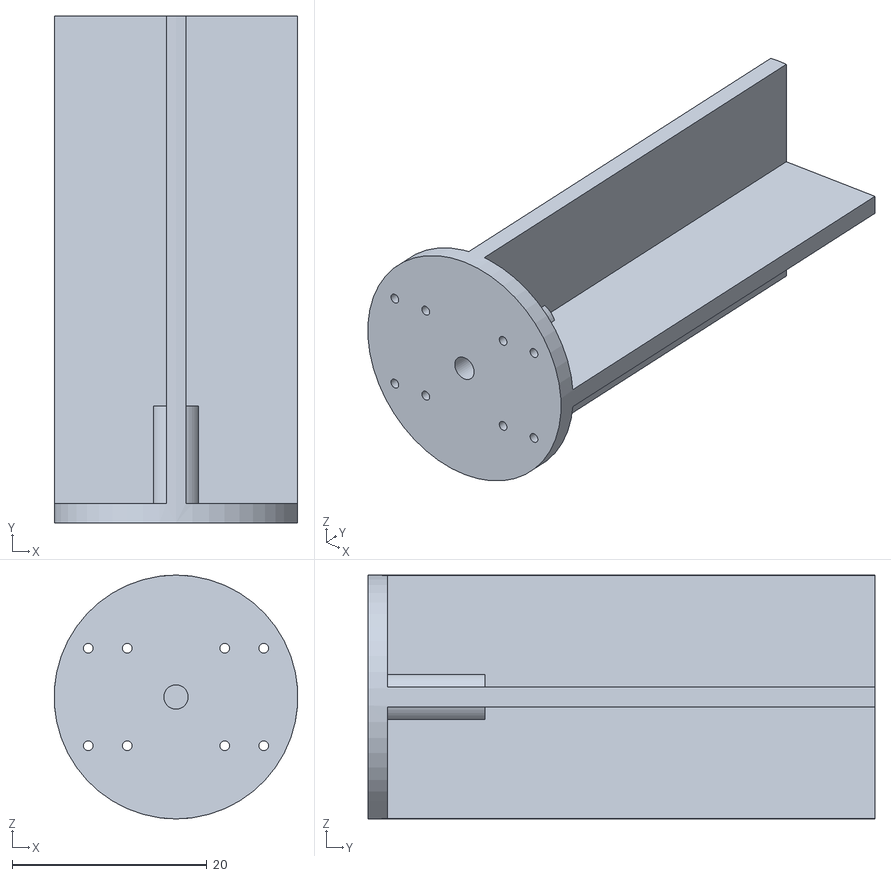
[picture p229: CAD file, 2021-07-27]
STL_SMARTHOME/Jardi/SeguidorSolar/SuportLDR.STL
24.9 x 52.0 x 25.0
