maynej/Smart-Home/STL_SMARTHOME/Jardi/TurbinaAigua/Rotor.STL

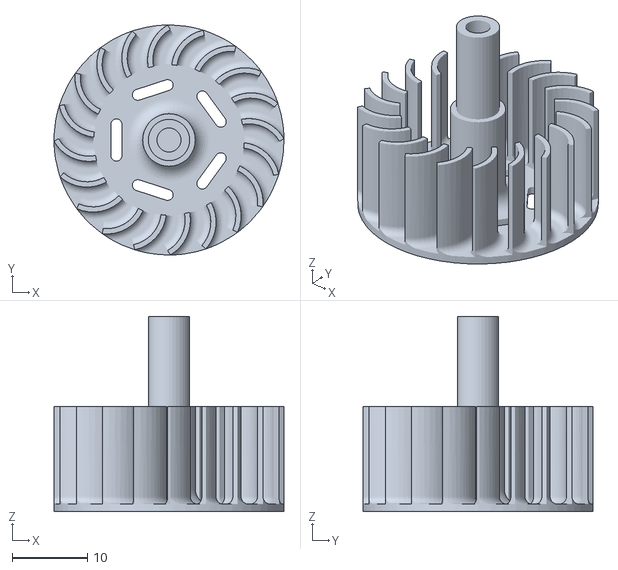
[picture p230: CAD file, 2021-07-27]
STL_SMARTHOME/Jardi/TurbinaAigua/Rotor.STL
30.6 x 30.6 x 26.0
