maynej/Smart-Home/STL_SMARTHOME/Casa/AireCondicionat/TapaAireD.stl

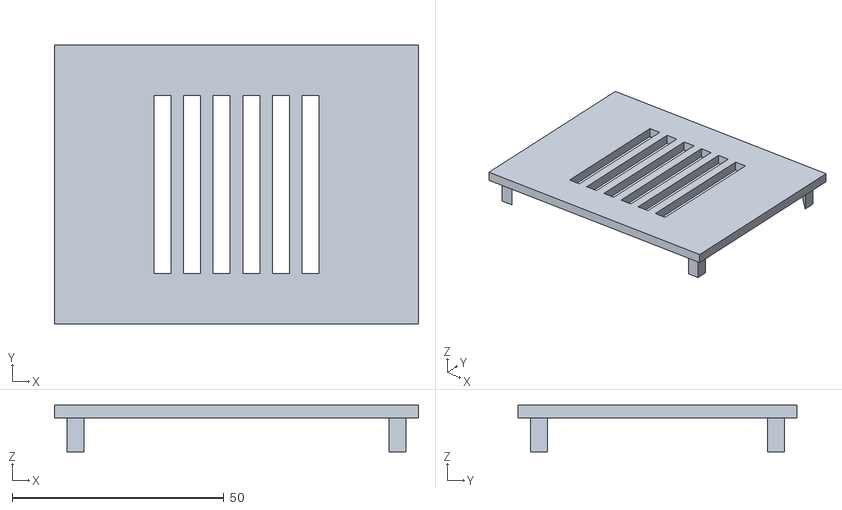
[picture p231: CAD file, 2021-07-27]
STL_SMARTHOME/Casa/AireCondicionat/TapaAireD.stl
86.0 x 66.0 x 11.0
