maynej/Smart-Home/STL_SMARTHOME/Casa/Ascensor/CabinaAscensor.stl

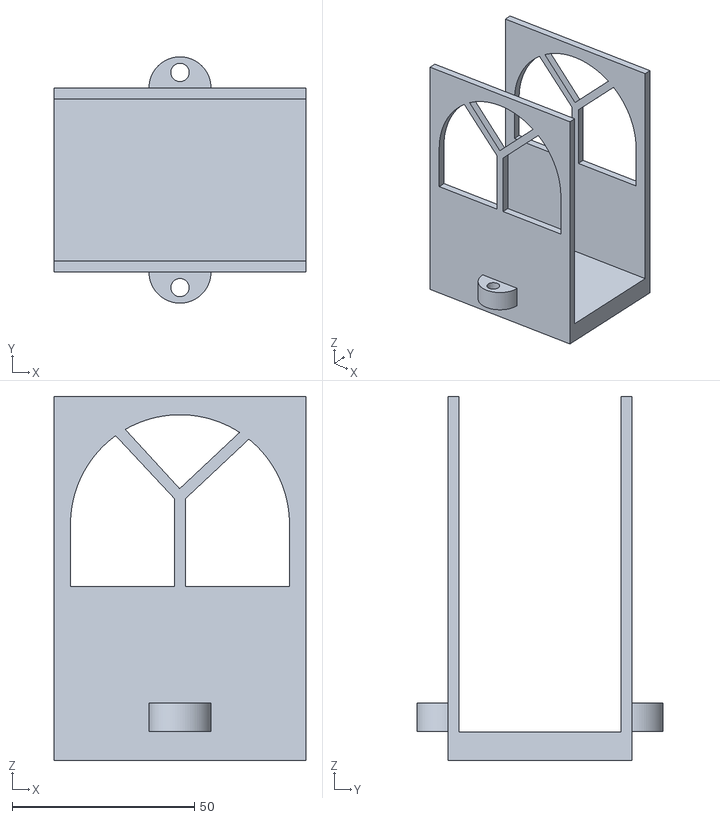
[picture p232: CAD file, 2021-07-27]
STL_SMARTHOME/Casa/Ascensor/CabinaAscensor.stl
69.0 x 67.5 x 99.7
