maynej/Smart-Home/STL_SMARTHOME/Casa/Finestres/VidrieraPetita_SenseMotor.stl

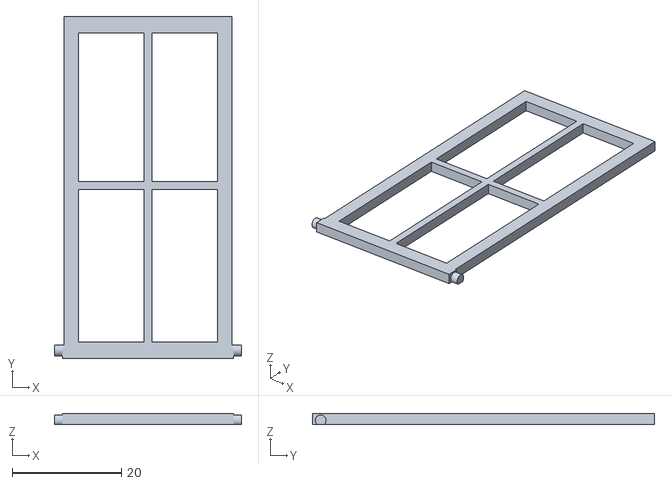
[picture p233: CAD file, 2021-07-27]
STL_SMARTHOME/Casa/Finestres/VidrieraPetita_SenseMotor.stl
34.4 x 62.8 x 2.00
