maynej/Smart-Home/STL_SMARTHOME/Casa/Mobiliari/Dormitoris/Armari.stl

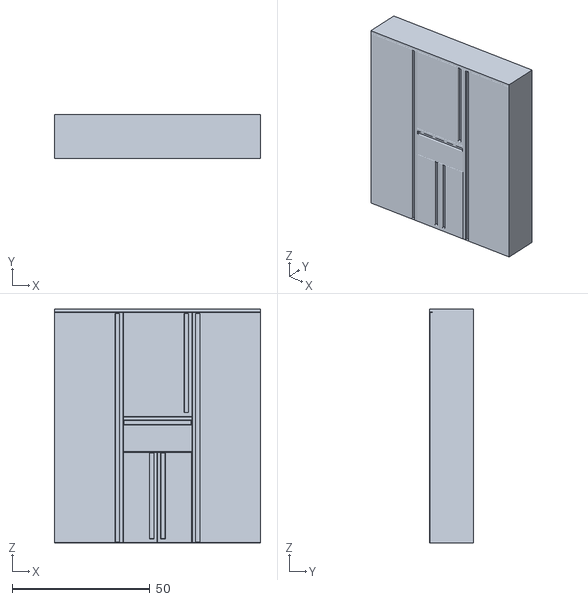
[picture p234: CAD file, 2021-07-27]
STL_SMARTHOME/Casa/Mobiliari/Dormitoris/Armari.stl
75.0 x 16.0 x 85.0
