maynej/Smart-Home/STL_SMARTHOME/Casa/Parets/ParetQ.stl

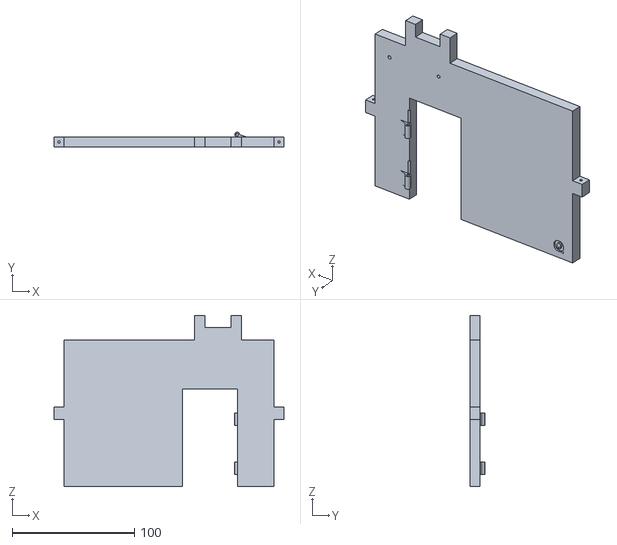
[picture p235: CAD file, 2021-07-27]
STL_SMARTHOME/Casa/Parets/ParetQ.stl
188.0 x 12.0 x 140.0
