maynej/Smart-Home/STL_SMARTHOME/Casa/PatiGaratge/MurE.stl

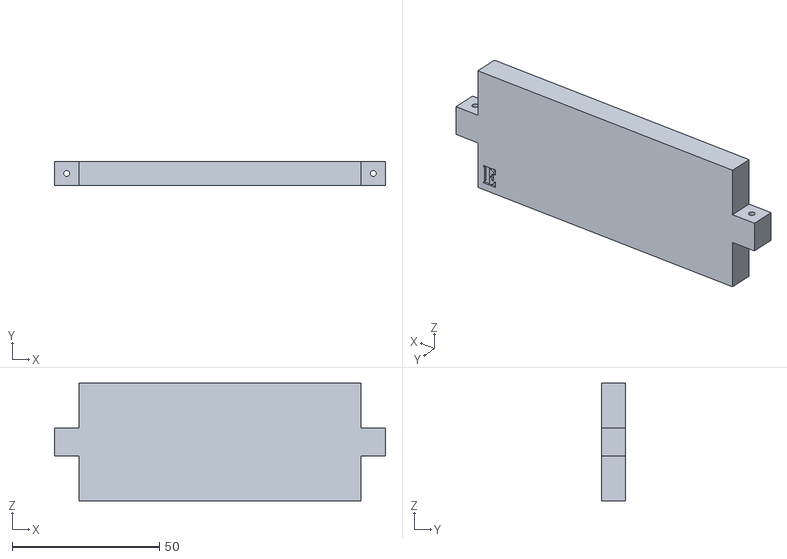
[picture p236: CAD file, 2021-07-27]
STL_SMARTHOME/Casa/PatiGaratge/MurE.stl
112.5 x 8.00 x 40.0
