maynej/Smart-Home/STL_SMARTHOME/Casa/Portes/PomPorta.stl

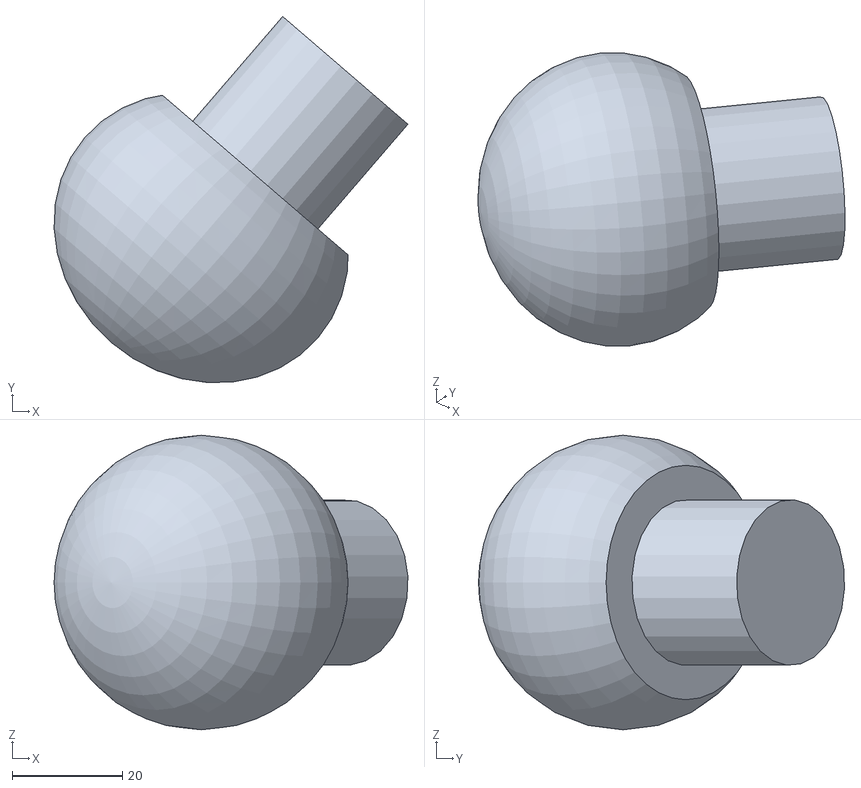
[picture p237: CAD file, 2021-07-27]
STL_SMARTHOME/Casa/Portes/PomPorta.stl
64.1 x 66.3 x 53.3
