maynej/Smart-Home/STL_SMARTHOME/Casa/Teulada/Suport_Teulada Frontal/SuportTeuladaE.stl

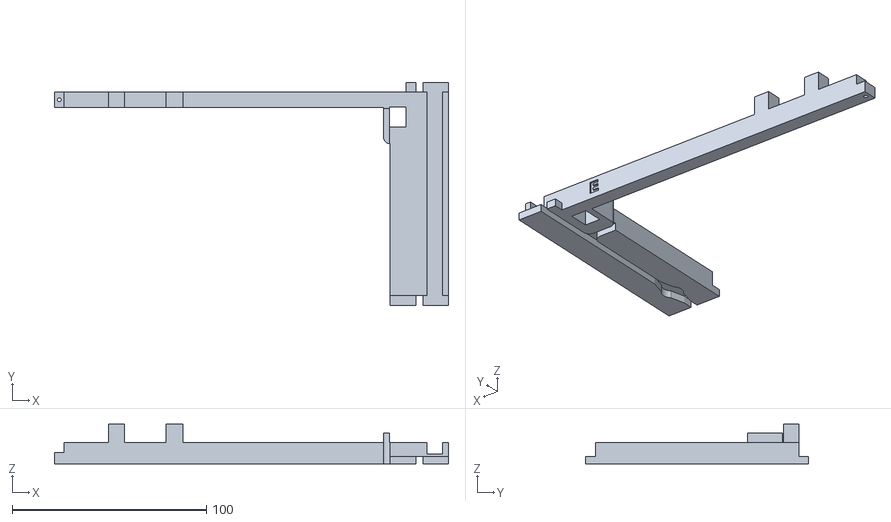
[picture p238: CAD file, 2021-07-27]
STL_SMARTHOME/Casa/Teulada/Suport_Teulada Frontal/SuportTeuladaE.stl
202.7 x 114.8 x 20.5
