maynej/Smart-Home/STL_SMARTHOME/Casa/Teulada/Teulada Frontal/TeuladaFrontal_c1.stl

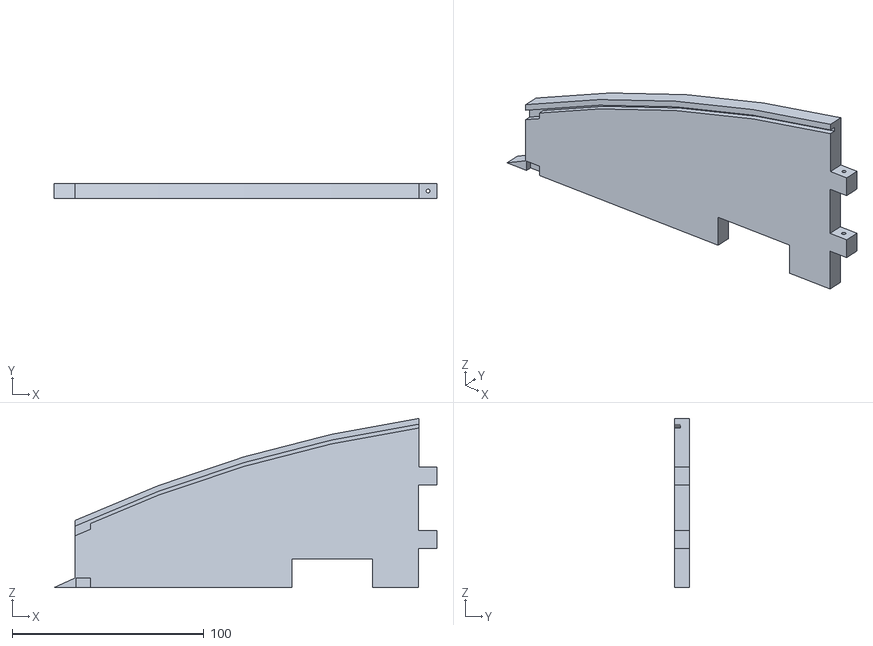
[picture p239: CAD file, 2021-07-27]
STL_SMARTHOME/Casa/Teulada/Teulada Frontal/TeuladaFrontal_c1.stl
199.5 x 7.75 x 88.1
