maynej/Smart-Home/STL_SMARTHOME/Garatge/GaratgeD.stl

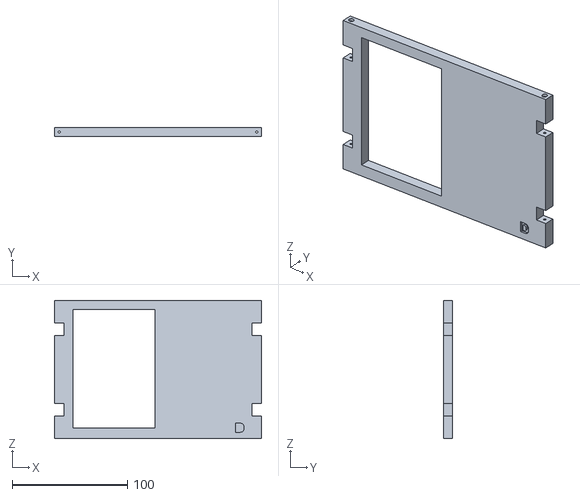
[picture p240: CAD file, 2021-07-27]
STL_SMARTHOME/Garatge/GaratgeD.stl
180.0 x 8.00 x 120.0
