maynej/Smart-Home/STL_SMARTHOME/Jardi/GeneradorEolic/BaseTurbina.stl

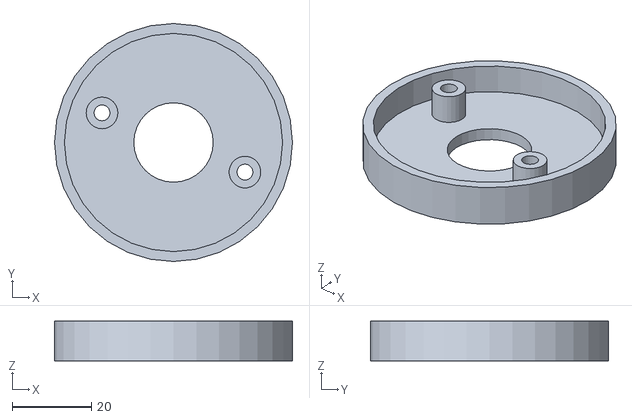
[picture p241: CAD file, 2021-07-27]
STL_SMARTHOME/Jardi/GeneradorEolic/BaseTurbina.stl
60.0 x 60.0 x 10.0
