maynej/Smart-Home/STL_SMARTHOME/Jardi/SeguidorSolar/SuportPanell.STL

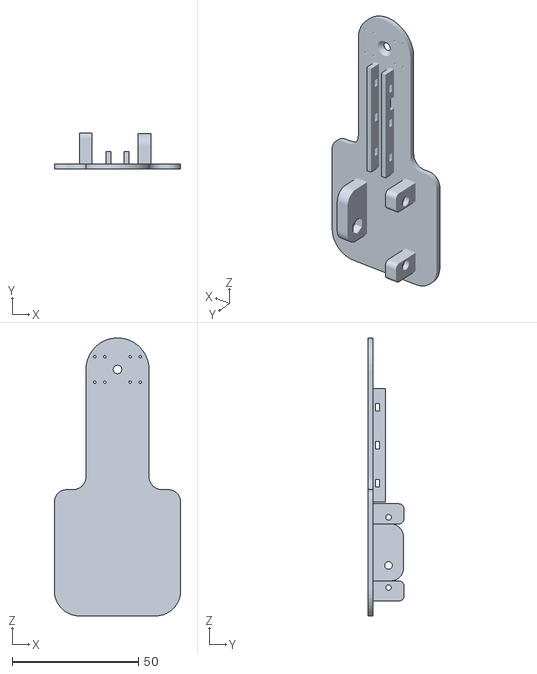
[picture p242: CAD file, 2021-07-27]
STL_SMARTHOME/Jardi/SeguidorSolar/SuportPanell.STL
50.0 x 14.2 x 110.0
