maynej/Smart-Home/STL_SMARTHOME/Casa/Finestres/MarcFinestraPetita.stl

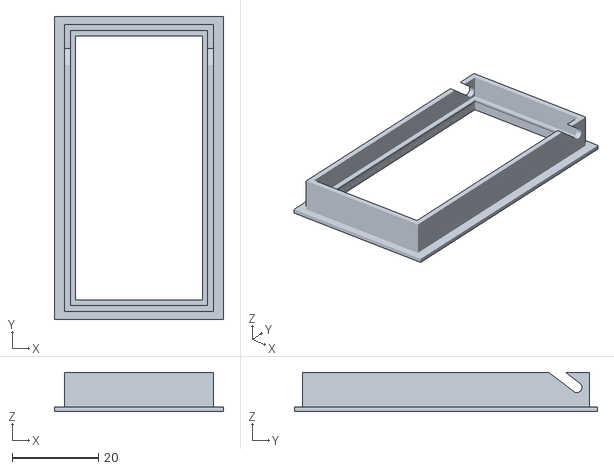
[picture p243: CAD file, 2021-07-27]
STL_SMARTHOME/Casa/Finestres/MarcFinestraPetita.stl
39.2 x 70.3 x 9.06
