maynej/Smart-Home/STL_SMARTHOME/Casa/Parets/ParetV.stl

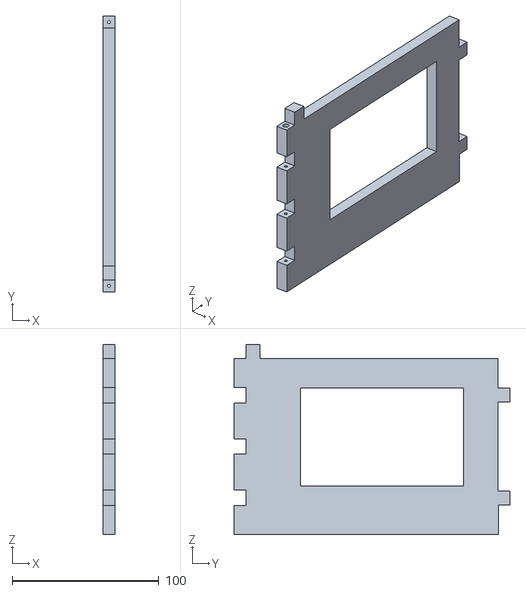
[picture p244: CAD file, 2021-07-27]
STL_SMARTHOME/Casa/Parets/ParetV.stl
8.00 x 188.0 x 129.5
