maynej/Smart-Home/STL_SMARTHOME/Casa/Portes/FinalCorrederes.stl

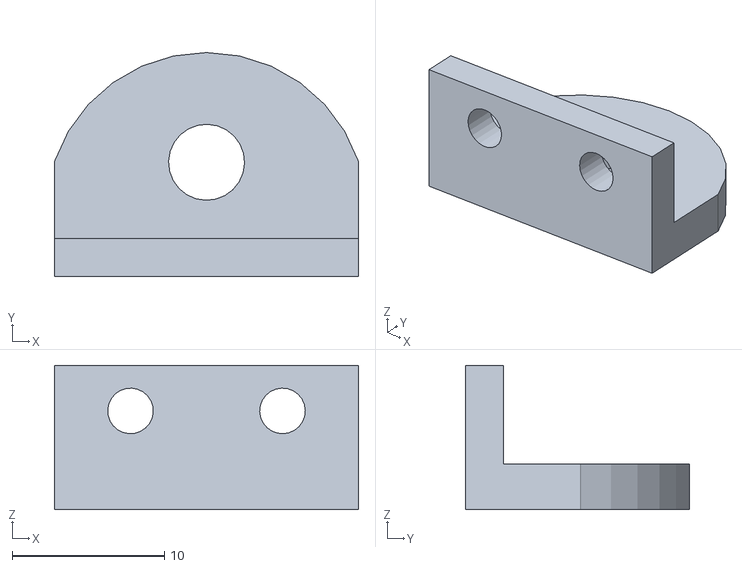
[picture p245: CAD file, 2021-07-27]
STL_SMARTHOME/Casa/Portes/FinalCorrederes.stl
20.0 x 14.7 x 9.50
