maynej/Smart-Home/STL_SMARTHOME/Casa/Teulada/Teulada Posterior/TeulatVerdE4.stl

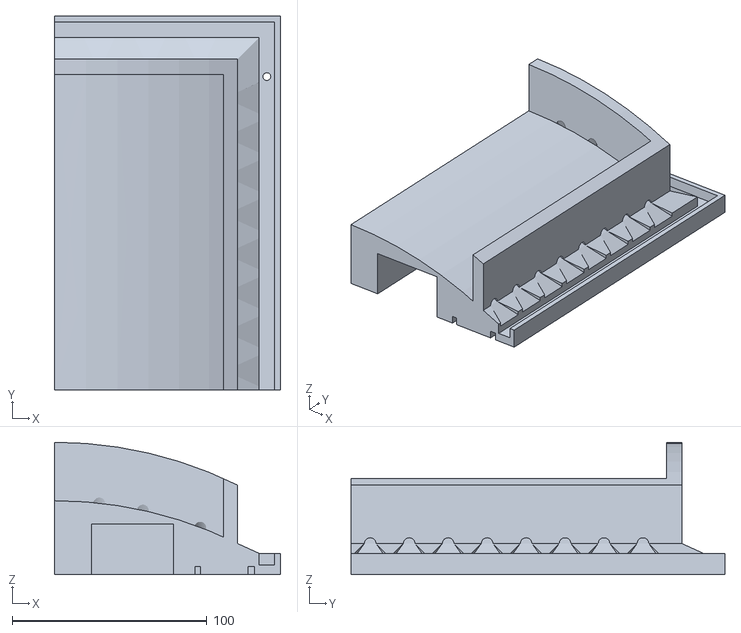
[picture p248: CAD file, 2021-07-27]
STL_SMARTHOME/Casa/Teulada/Teulada Posterior/TeulatVerdE4.stl
116.0 x 191.7 x 68.0
