maynej/Smart-Home/STL_SMARTHOME/Garatge/PortaInferiorGaratge.stl

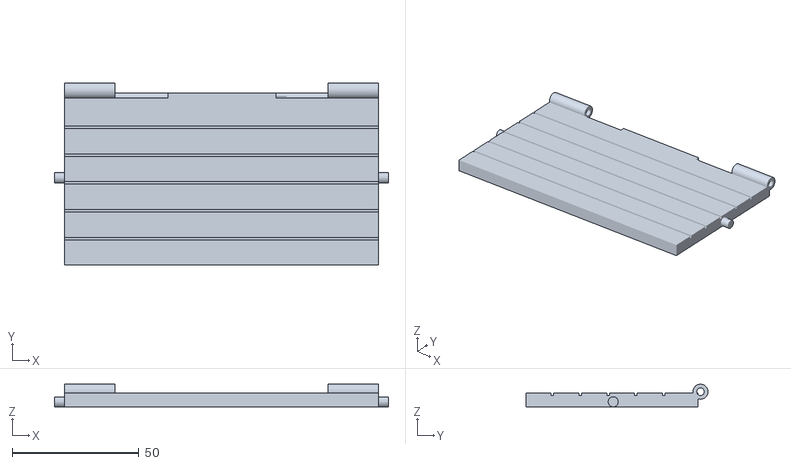
[picture p250: CAD file, 2021-07-27]
STL_SMARTHOME/Garatge/PortaInferiorGaratge.stl
132.0 x 72.0 x 9.00
