maynej/Smart-Home/STL_SMARTHOME/Casa/Parets/ParetY.stl

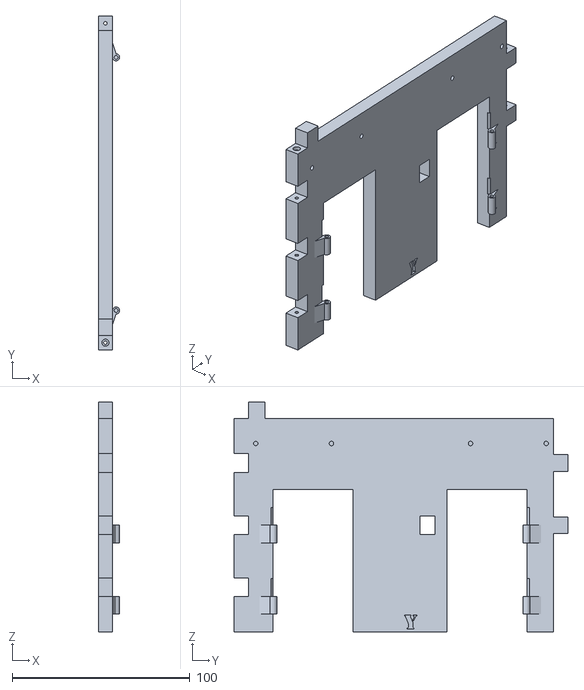
[picture p251: CAD file, 2021-07-27]
STL_SMARTHOME/Casa/Parets/ParetY.stl
12.0 x 188.0 x 129.2
