maynej/Smart-Home/STL_SMARTHOME/Garatge/GaratgeE.stl

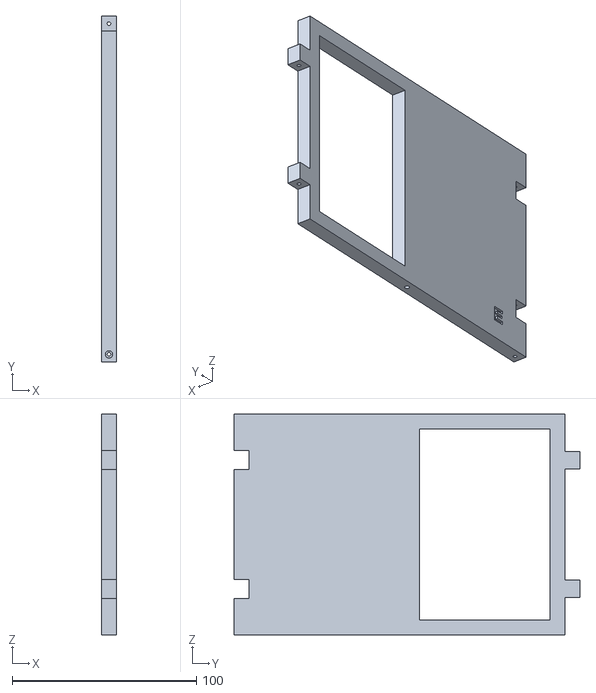
[picture p253: CAD file, 2021-07-27]
STL_SMARTHOME/Garatge/GaratgeE.stl
8.00 x 188.0 x 120.0
