maynej/Smart-Home/STL_SMARTHOME/Casa/Parets/ParetM.stl

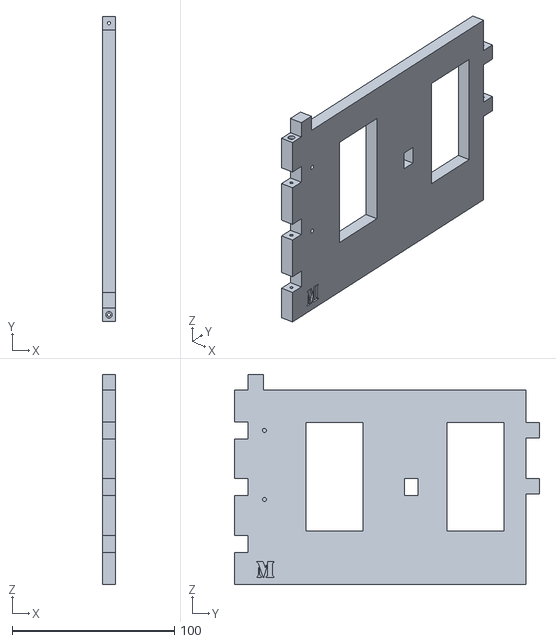
[picture p254: CAD file, 2021-07-27]
STL_SMARTHOME/Casa/Parets/ParetM.stl
8.00 x 188.0 x 129.5
