maynej/Smart-Home/STL_SMARTHOME/Garatge/Suport Porta.stl

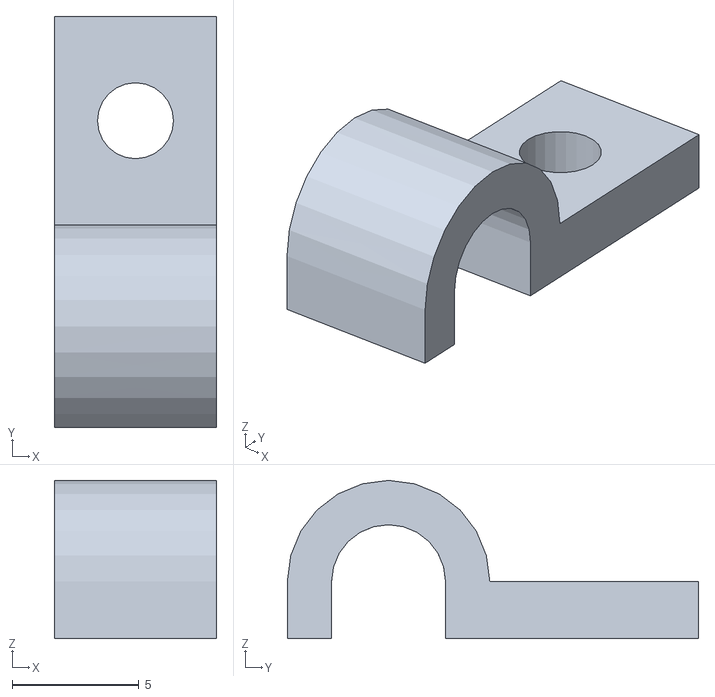
[picture p255: CAD file, 2021-07-27]
STL_SMARTHOME/Garatge/Suport Porta.stl
6.40 x 16.2 x 6.25
