maynej/Smart-Home/STL_SMARTHOME/Casa/Parets/ParetO.stl

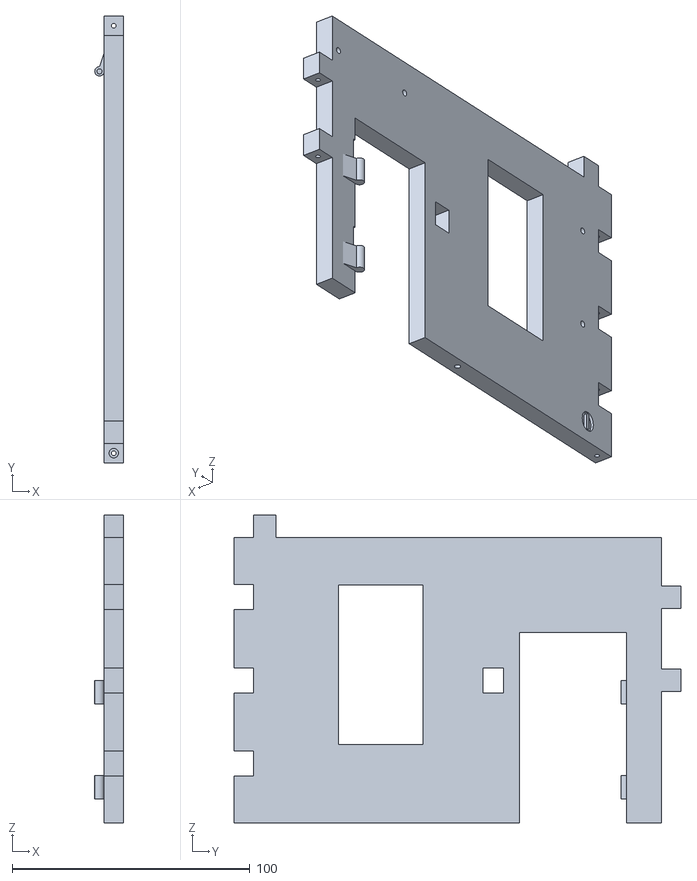
[picture p256: CAD file, 2021-07-27]
STL_SMARTHOME/Casa/Parets/ParetO.stl
12.0 x 188.0 x 129.5
