maynej/Smart-Home/STL_SMARTHOME/Garatge/ServoSuportGaratge.stl

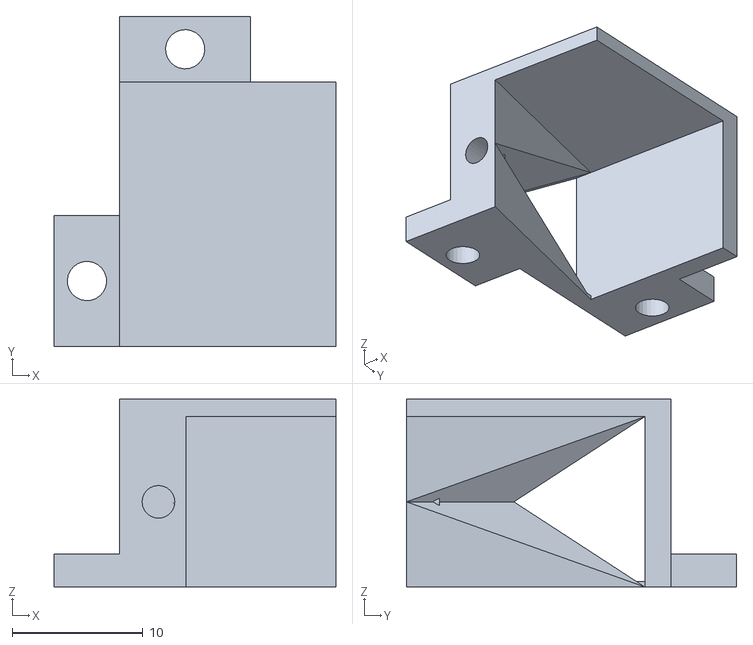
[picture p257: CAD file, 2021-07-27]
STL_SMARTHOME/Garatge/ServoSuportGaratge.stl
21.5 x 25.2 x 14.3
