maynej/Smart-Home/STL_SMARTHOME/Casa/Parets/ParetP.stl

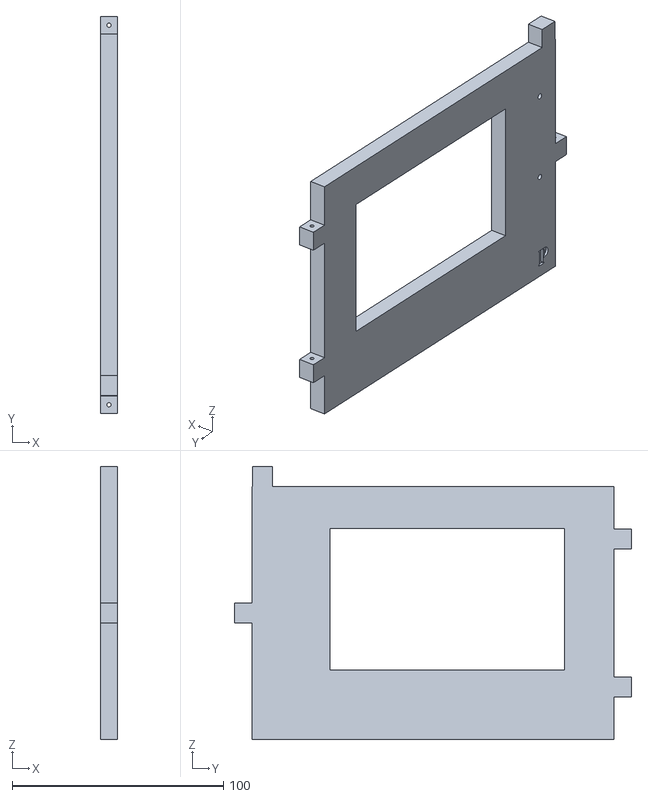
[picture p258: CAD file, 2021-07-27]
STL_SMARTHOME/Casa/Parets/ParetP.stl
8.00 x 188.0 x 129.5
