maynej/Smart-Home/STL_SMARTHOME/Casa/Parets/ParetX.stl

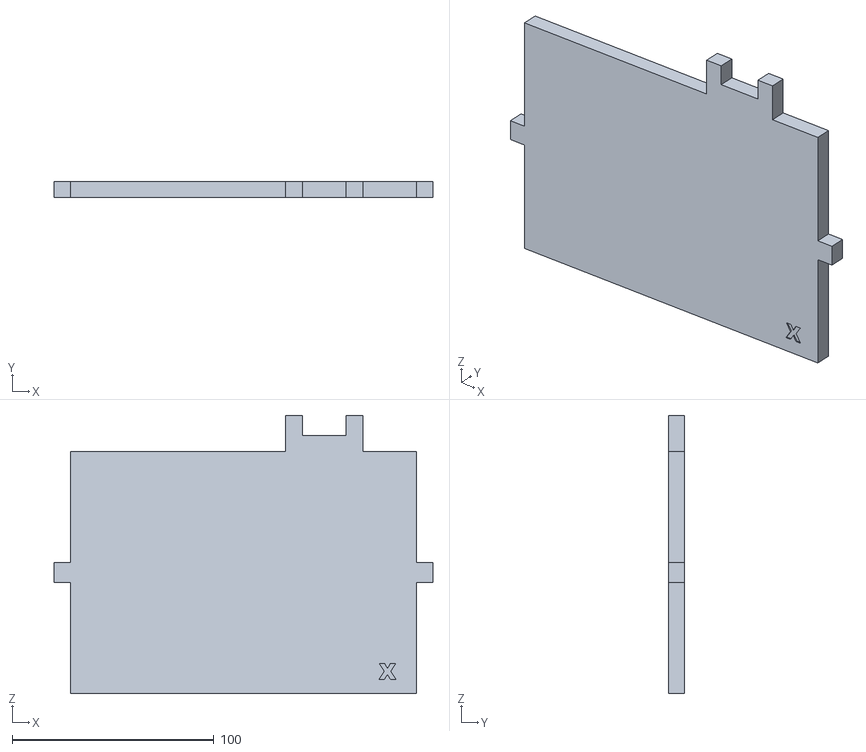
[picture p259: CAD file, 2021-07-27]
STL_SMARTHOME/Casa/Parets/ParetX.stl
188.0 x 8.00 x 138.0
