maynej/Smart-Home/STL_SMARTHOME/Garatge/ColumnaGaratgeX2.stl

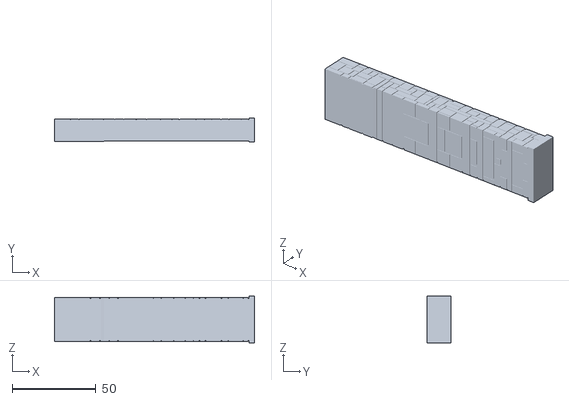
[picture p260: CAD file, 2021-07-27]
STL_SMARTHOME/Garatge/ColumnaGaratgeX2.stl
119.5 x 14.1 x 27.8
