maynej/Smart-Home/STL_SMARTHOME/Casa/Parets/ParetS.stl

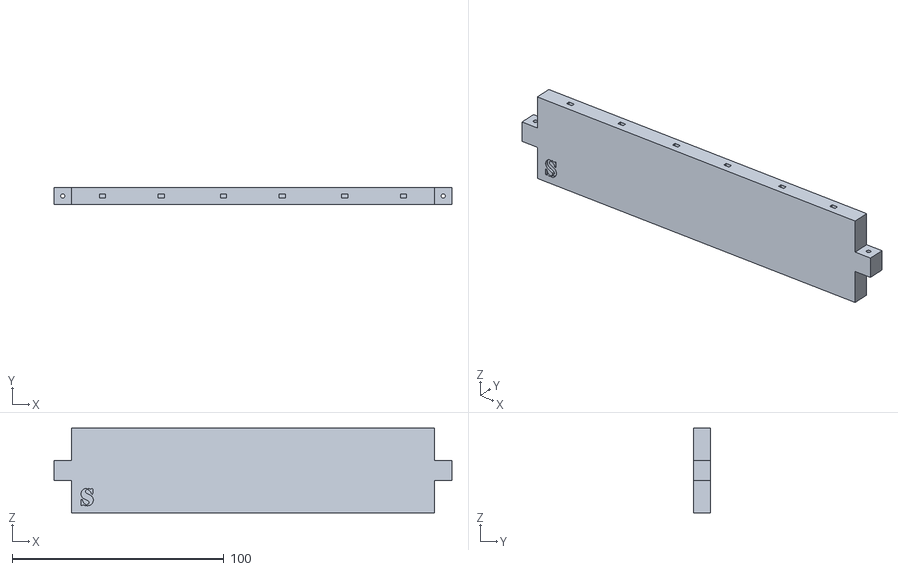
[picture p261: CAD file, 2021-07-27]
STL_SMARTHOME/Casa/Parets/ParetS.stl
188.0 x 8.00 x 40.0
