maynej/Smart-Home/STL_SMARTHOME/Casa/Parets/ParetT.stl

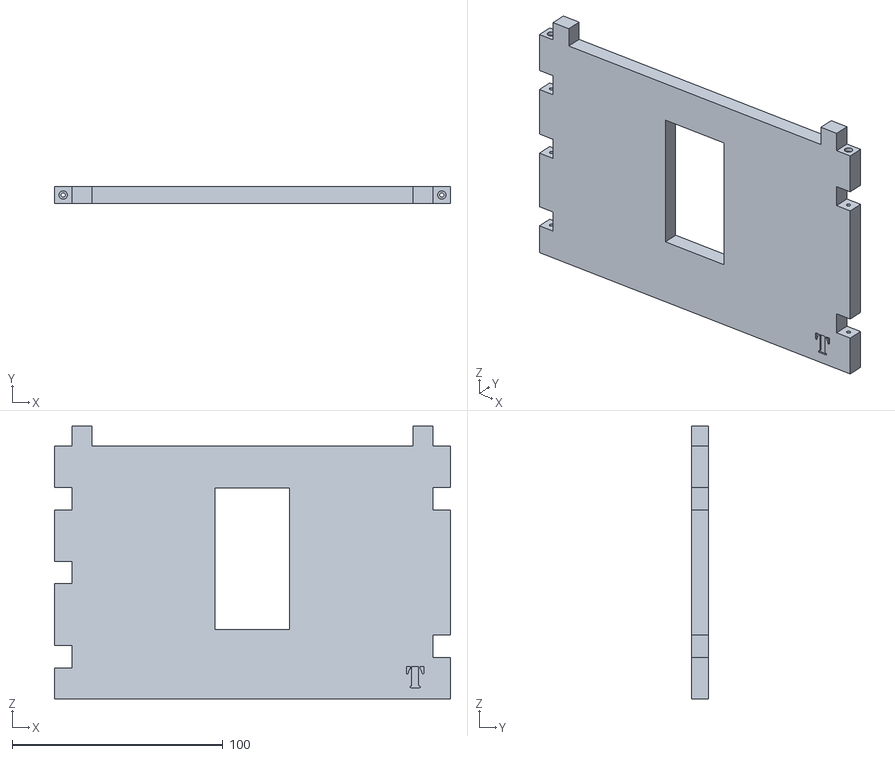
[picture p262: CAD file, 2021-07-27]
STL_SMARTHOME/Casa/Parets/ParetT.stl
188.0 x 8.00 x 129.5
