maynej/Smart-Home/STL_SMARTHOME/Casa/Parets/ParetB.stl

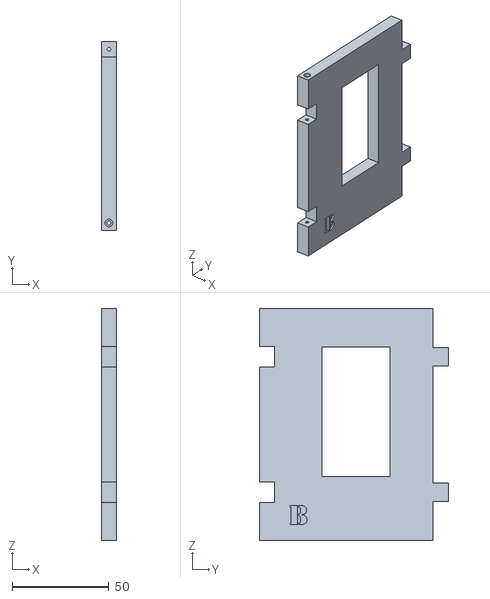
[picture p263: CAD file, 2021-07-27]
STL_SMARTHOME/Casa/Parets/ParetB.stl
8.00 x 98.0 x 120.0
