maynej/Smart-Home/STL_SMARTHOME/Casa/Parets/ParetF.stl

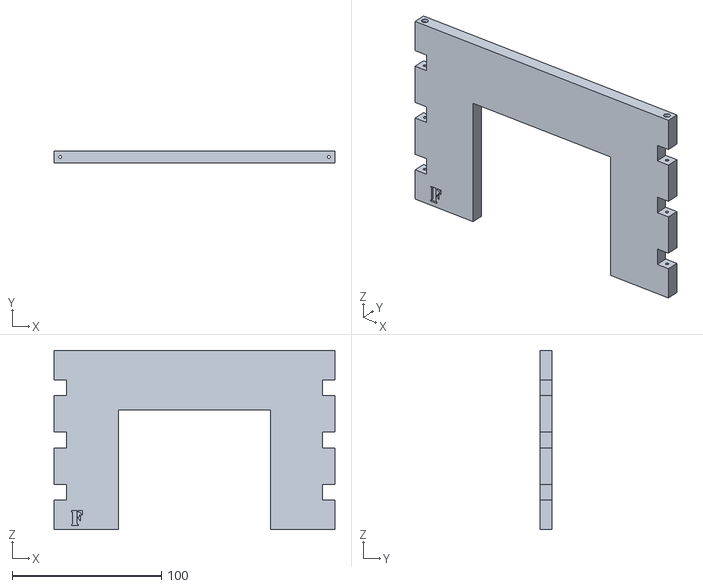
[picture p264: CAD file, 2021-07-27]
STL_SMARTHOME/Casa/Parets/ParetF.stl
188.0 x 8.00 x 120.0
