maynej/Smart-Home/STL_SMARTHOME/Casa/Parets/ParetU.stl

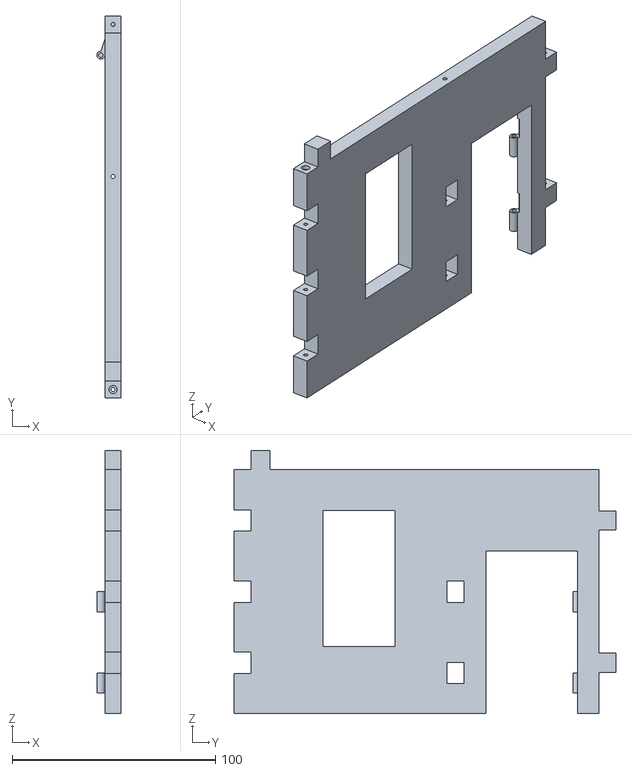
[picture p265: CAD file, 2021-07-27]
STL_SMARTHOME/Casa/Parets/ParetU.stl
12.0 x 188.0 x 129.5
