maynej/Smart-Home/STL_SMARTHOME/Casa/Parets/ParetR.stl

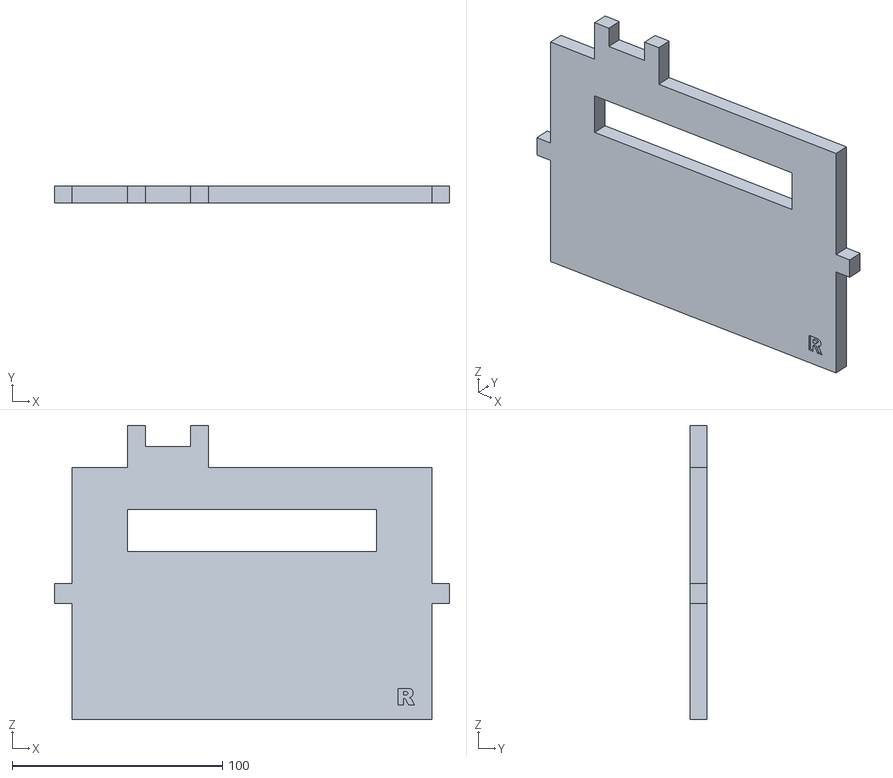
[picture p266: CAD file, 2021-07-27]
STL_SMARTHOME/Casa/Parets/ParetR.stl
188.0 x 8.00 x 140.0
